daveho/HW_VGA/Episode04/Materials/theory-010.pdf

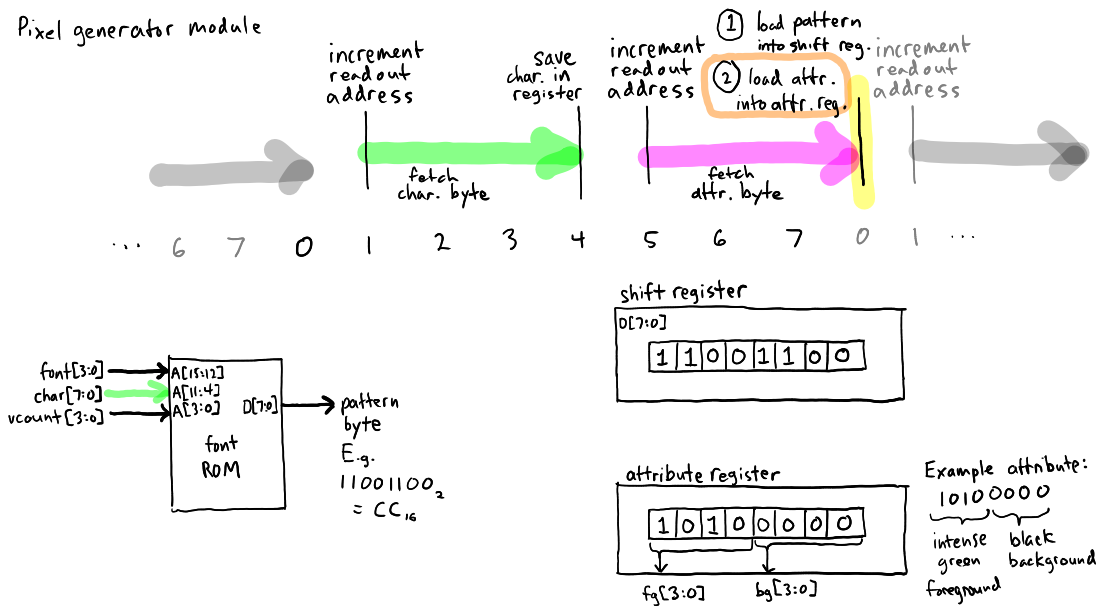
[picture p13: page 2]
