daveho/HW_VGA/Episode04/Materials/theory-011.pdf

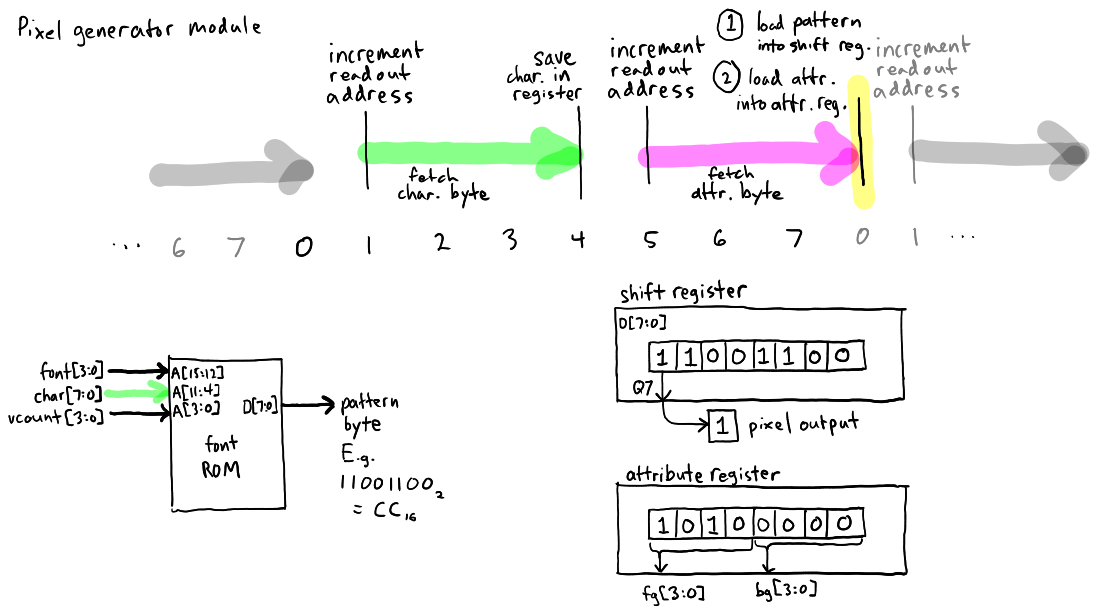
[picture p14: page 2]
