daveho/HW_VGA/Episode04/Materials/theory-012.pdf

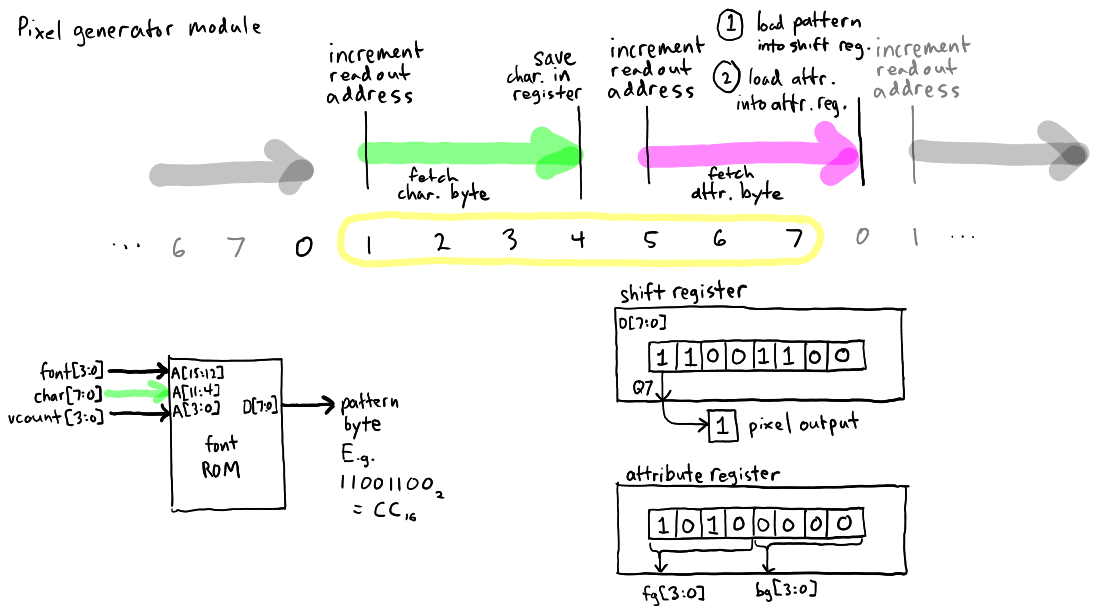
[picture p15: page 2]
