daveho/HW_VGA/Episode04/Materials/theory-013.pdf

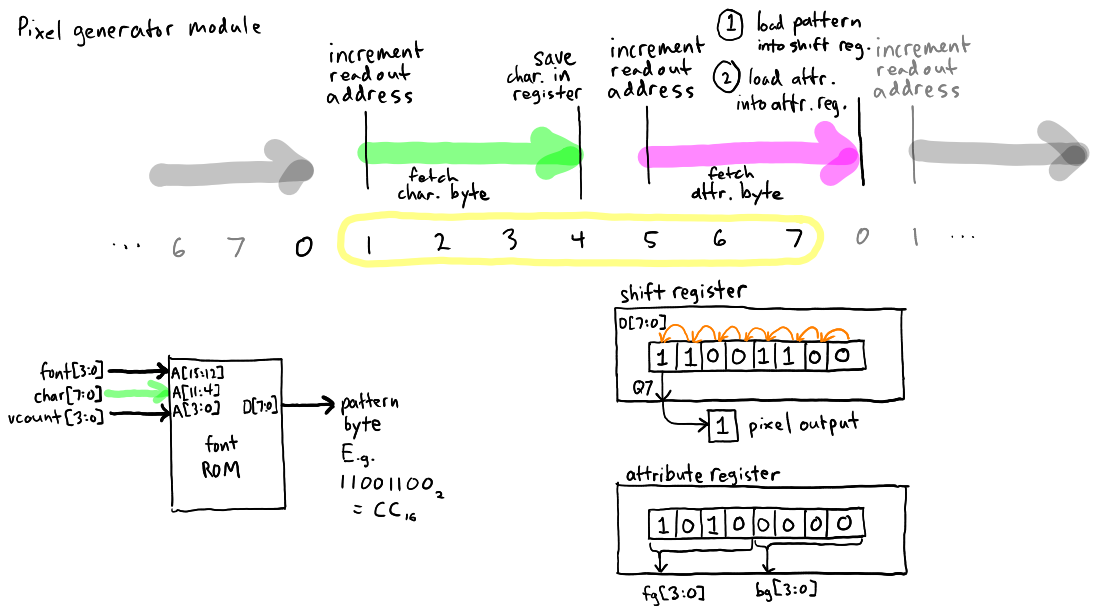
[picture p16: page 2]
