daveho/HW_VGA/Episode04/Materials/theory-014.pdf

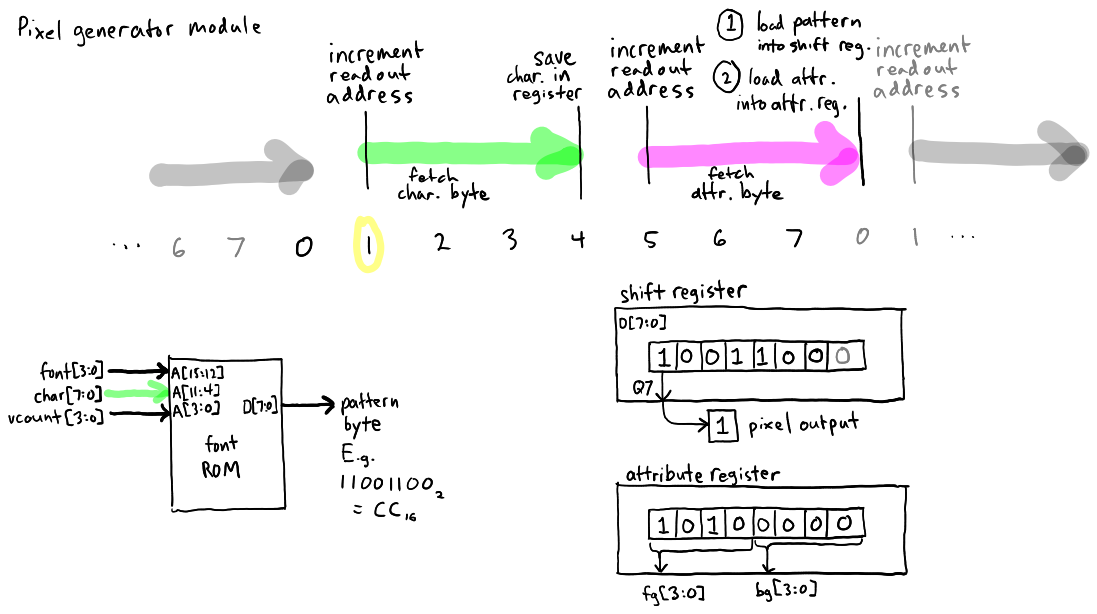
[picture p17: page 2]
