daveho/HW_VGA/Episode04/Materials/theory-015.pdf

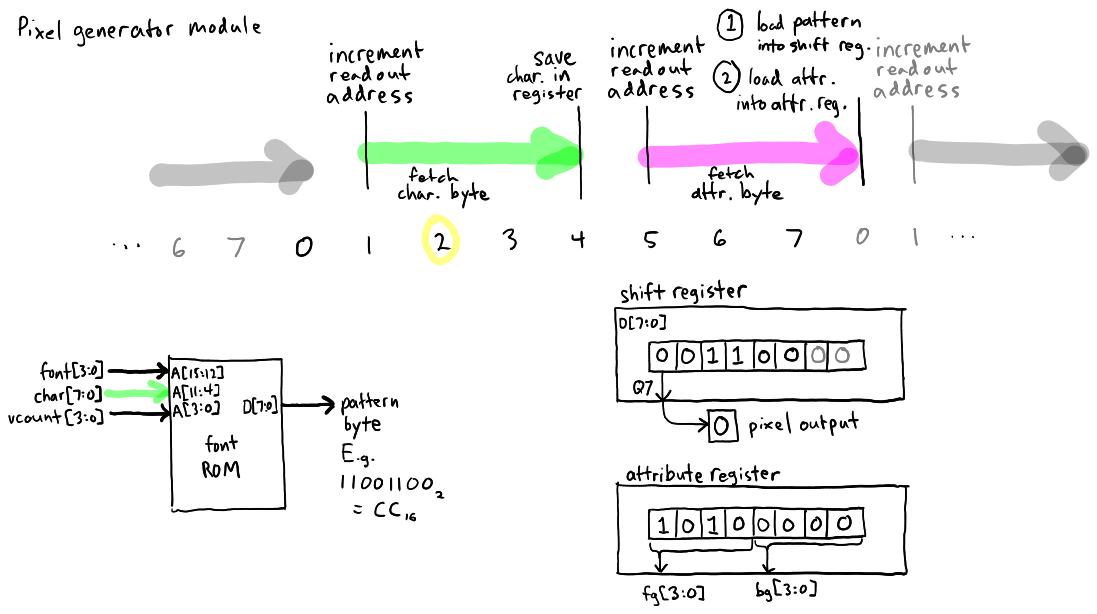
[picture p18: page 2]
