daveho/HW_VGA/Episode04/Materials/theory-016.pdf

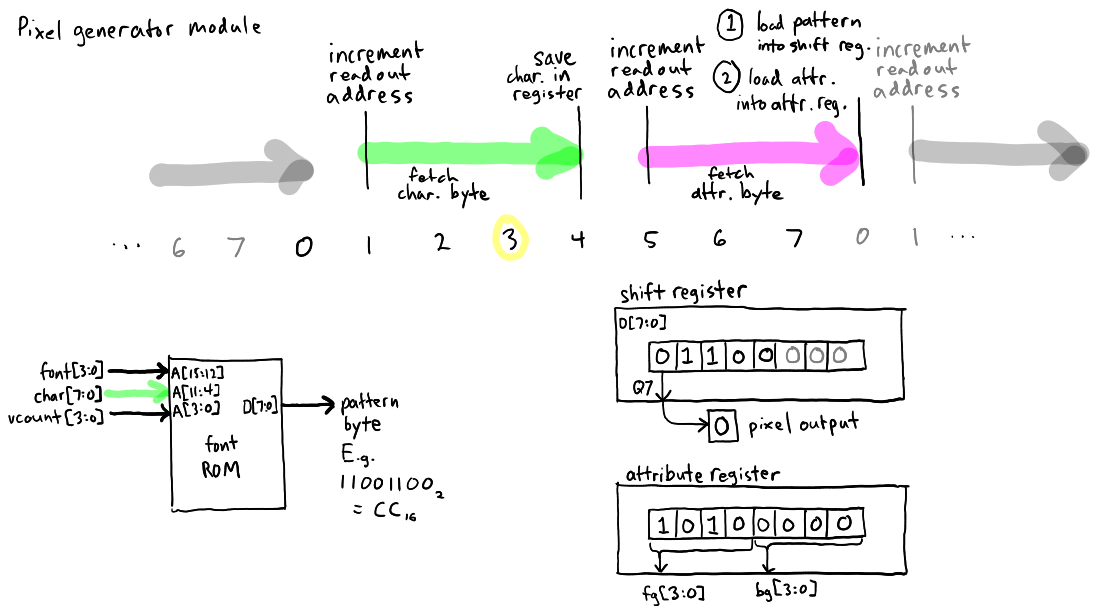
[picture p19: page 2]
