daveho/HW_VGA/Episode04/Materials/theory-017.pdf

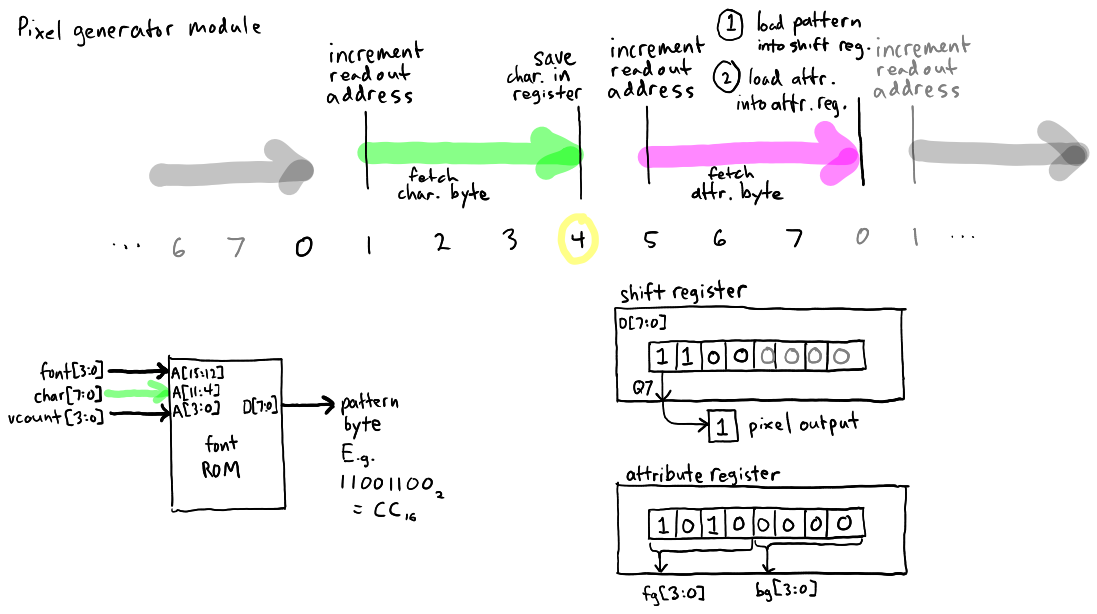
[picture p20: page 2]
