daveho/HW_VGA/Episode04/Materials/theory-018.pdf

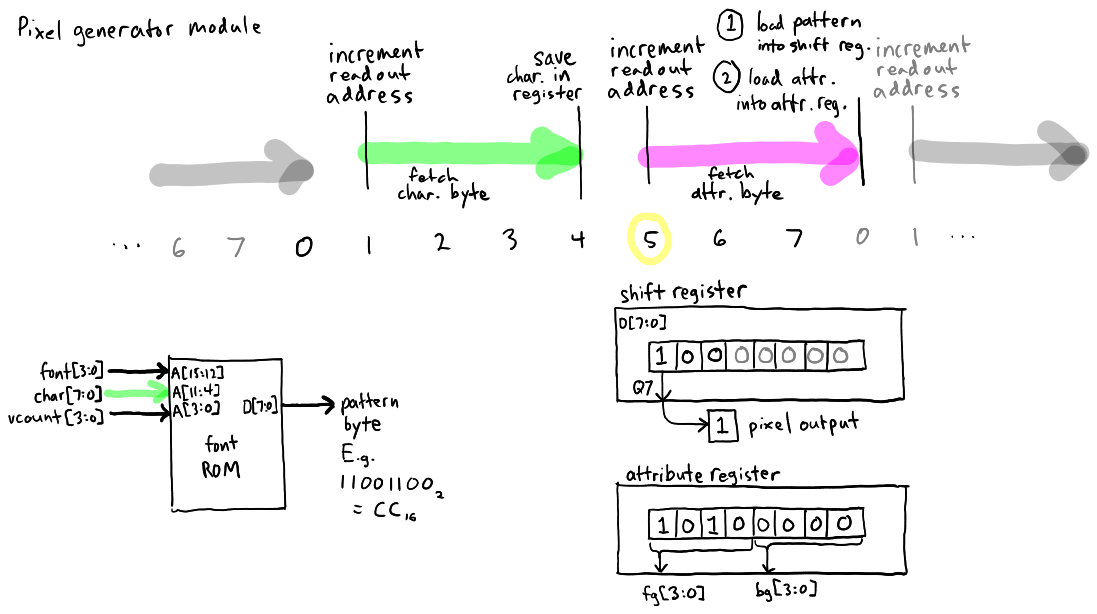
[picture p21: page 2]
