daveho/HW_VGA/Episode04/Materials/theory-019.pdf

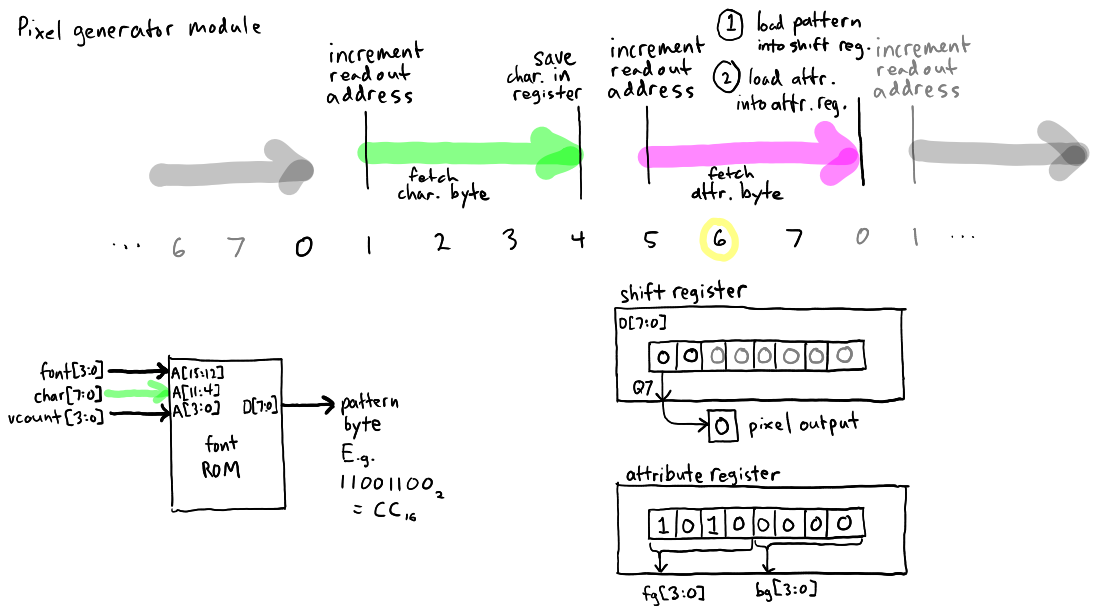
[picture p22: page 2]
