daveho/HW_VGA/Episode04/Materials/theory-020.pdf

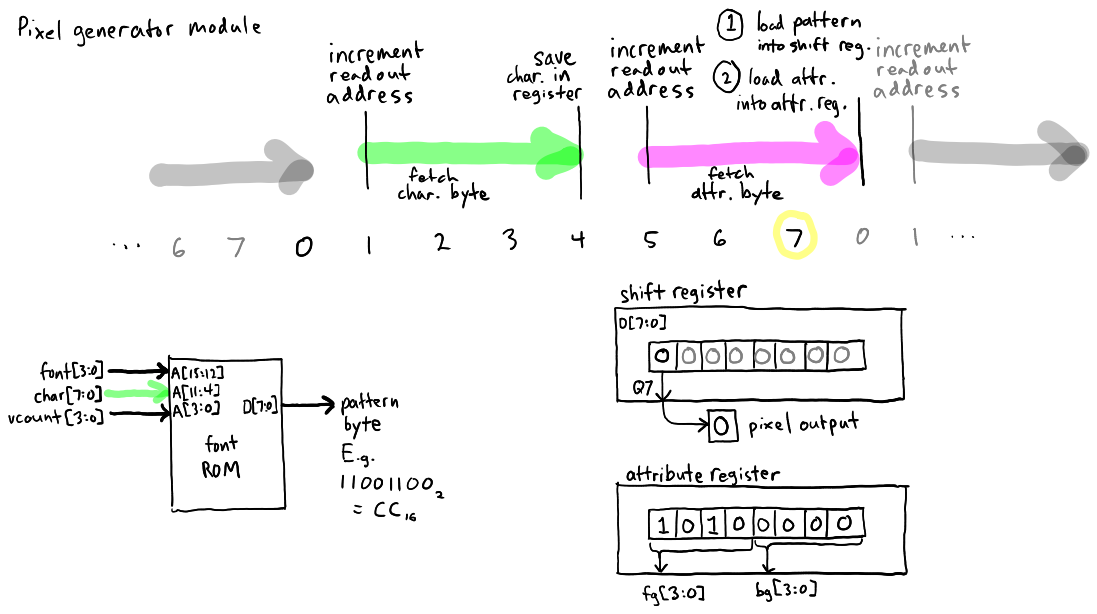
[picture p23: page 2]
