daveho/HW_VGA/Episode03/Materials/readout-overview-054.pdf

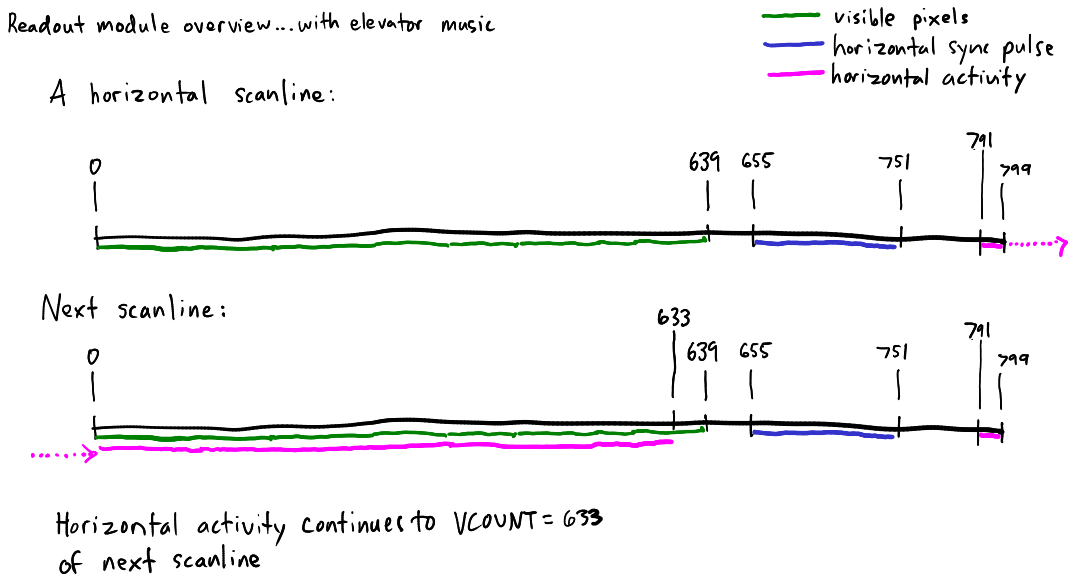
[picture p24: page 2]
