daveho/HW_VGA/Episode03/Materials/readout-overview-065.pdf

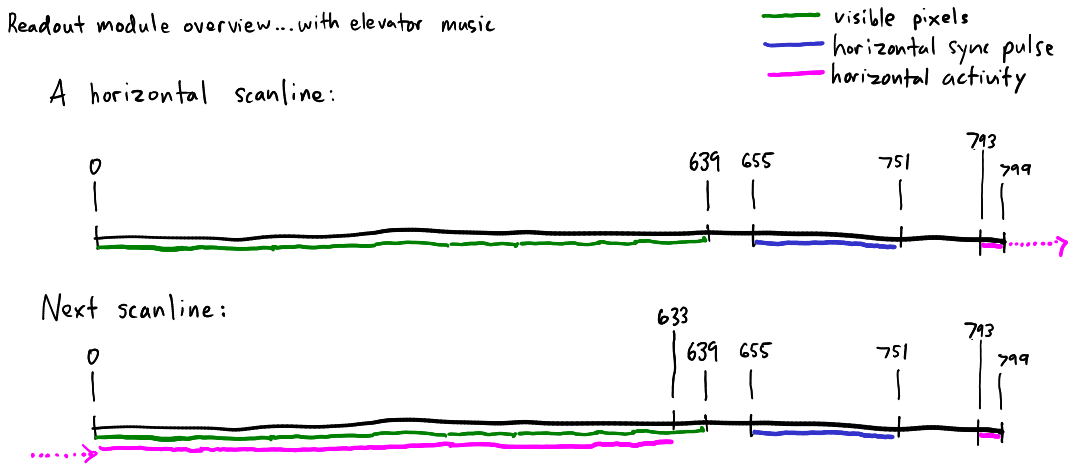
[picture p25: page 2]
