daveho/HW_VGA/Episode03/Materials/readout-overview-066.pdf

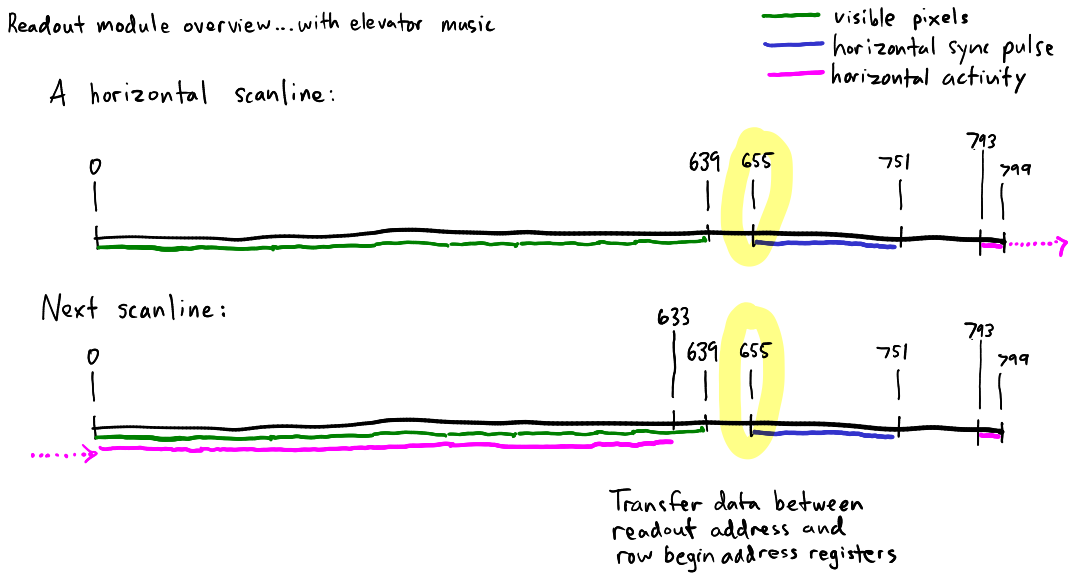
[picture p26: page 2]
