daveho/HW_VGA/Episode03/Materials/readout-overview-067.pdf

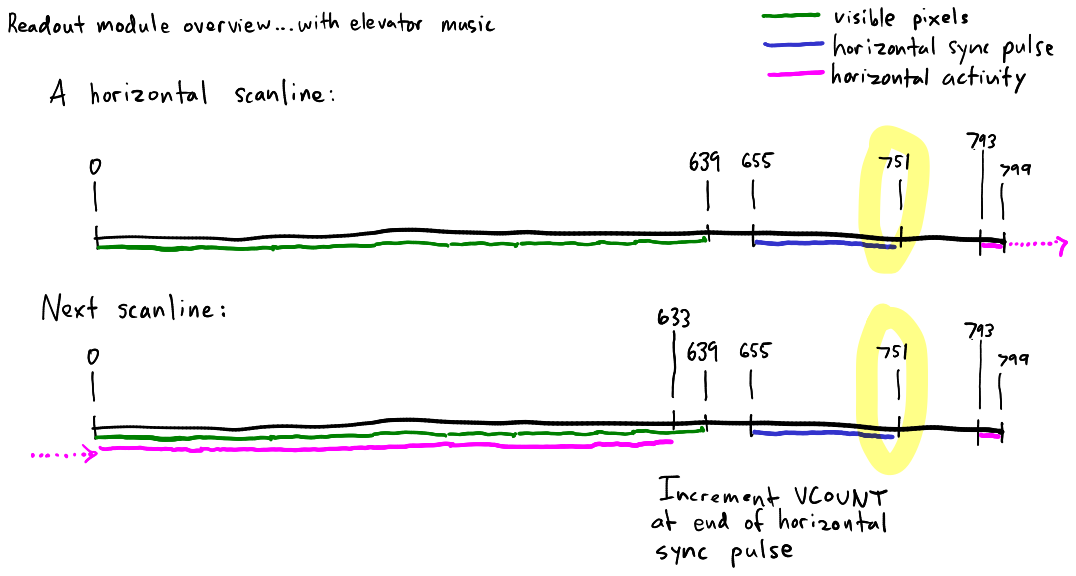
[picture p27: page 2]
