daveho/HW_VGA/Episode03/Materials/readout-overview-068.pdf

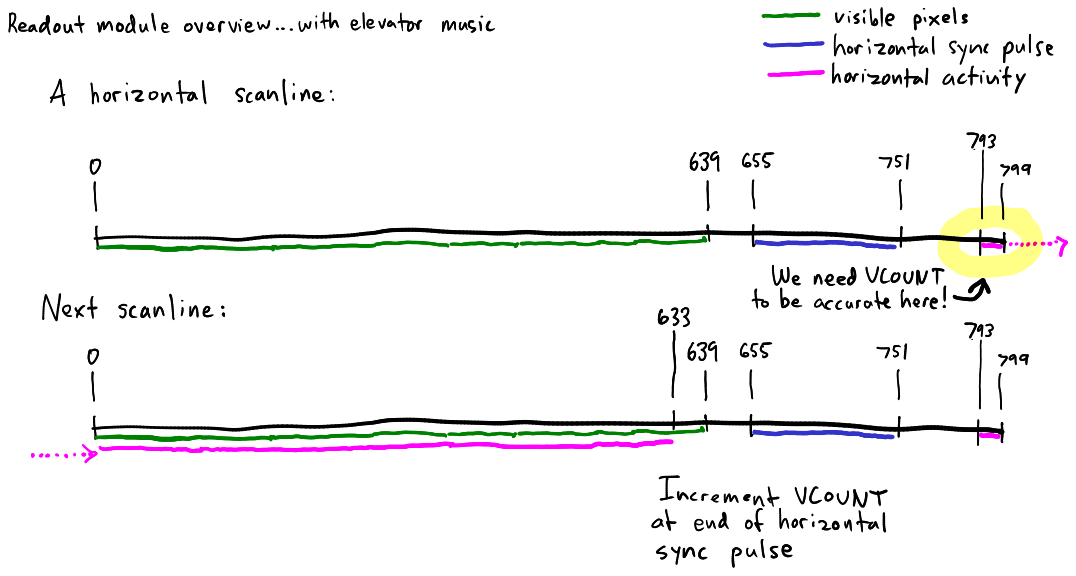
[picture p28: page 2]
