daveho/HW_VGA/Episode03/Materials/readout-overview-061.pdf

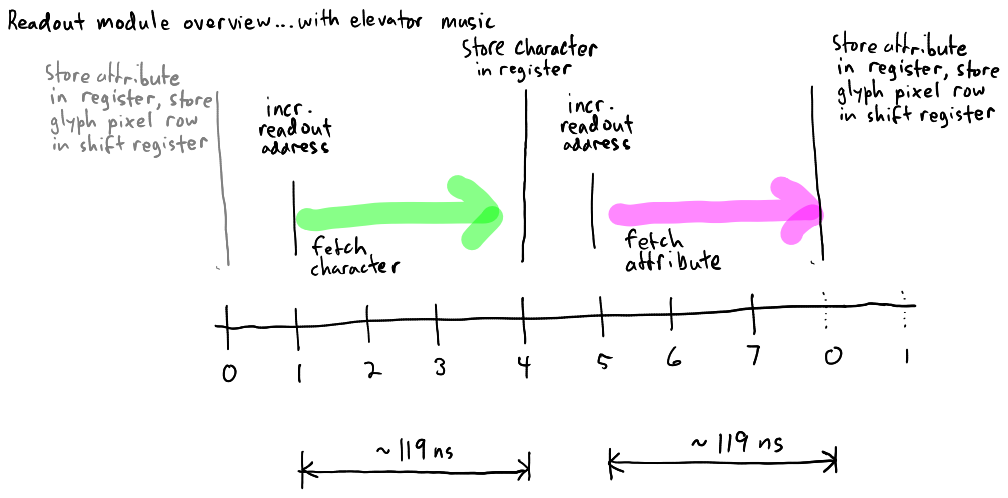
[picture p29: page 2]
