daveho/HW_VGA/Episode03/Materials/readout-overview-060a.pdf

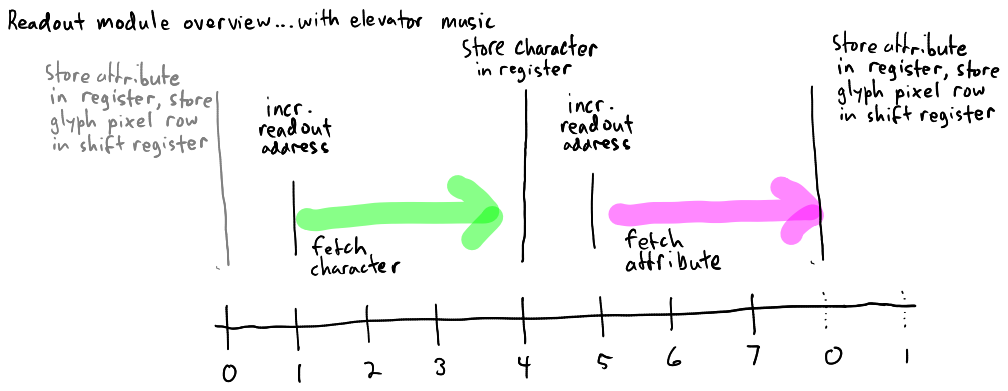
[picture p30: page 2]
