daveho/HW_VGA/Episode03/Materials/readout-overview-055.pdf

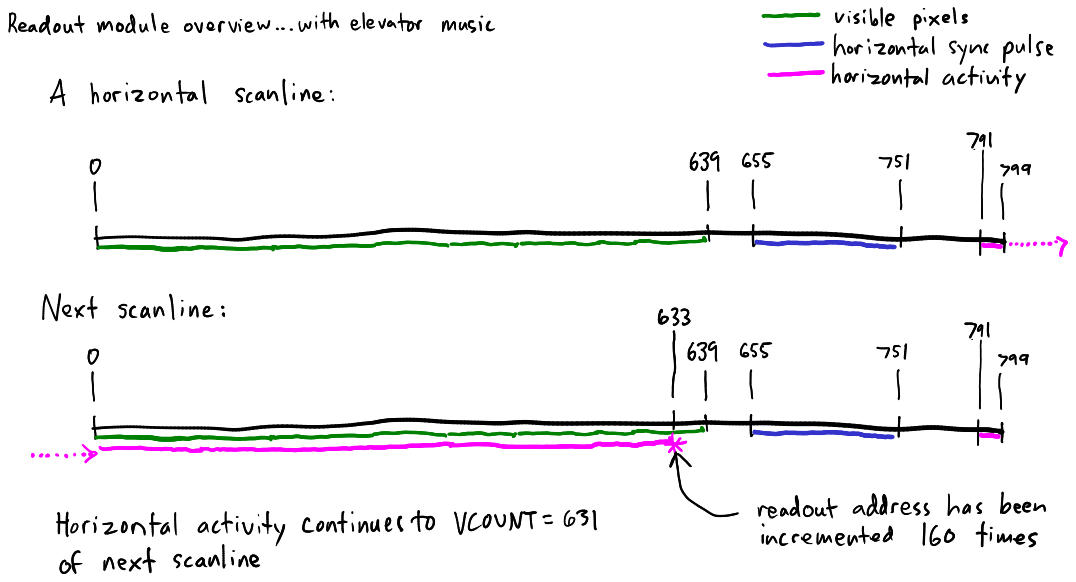
[picture p31: page 2]
