daveho/HW_VGA/Episode03/Materials/readout-overview-053a.pdf

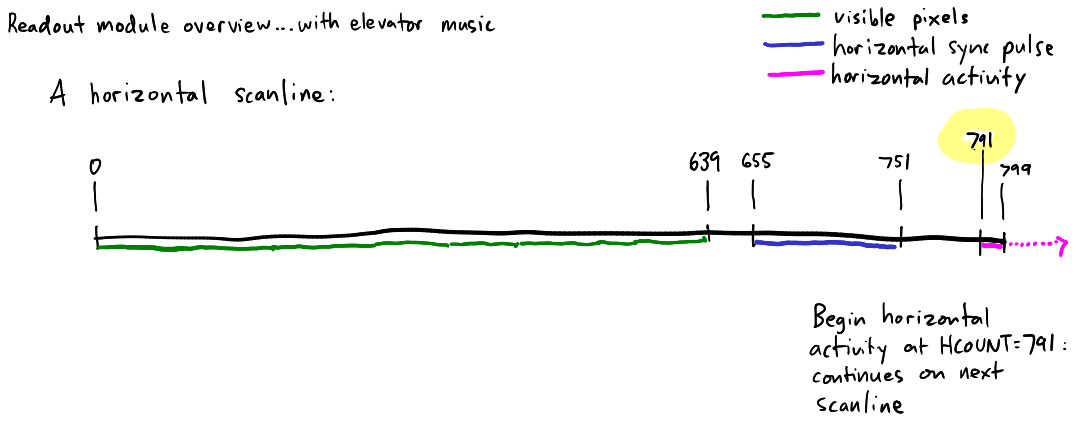
[picture p32: page 2]
