daveho/HW_VGA/Episode03/Materials/readout-overview-037b.pdf

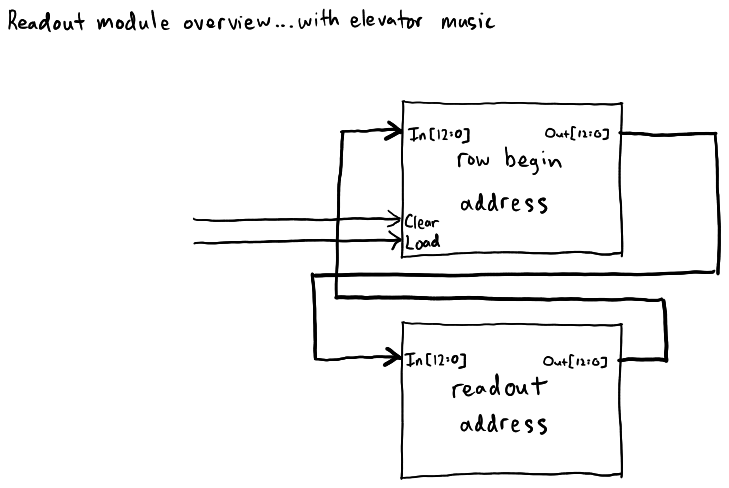
[picture p33: page 2]
