daveho/HW_VGA/Episode03/Materials/readout-overview-002.pdf

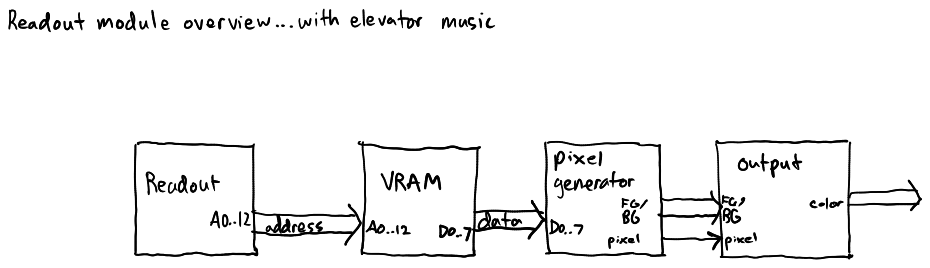
[picture p34: page 2]
