daveho/HW_VGA/Episode03/Materials/readout-overview-003.pdf

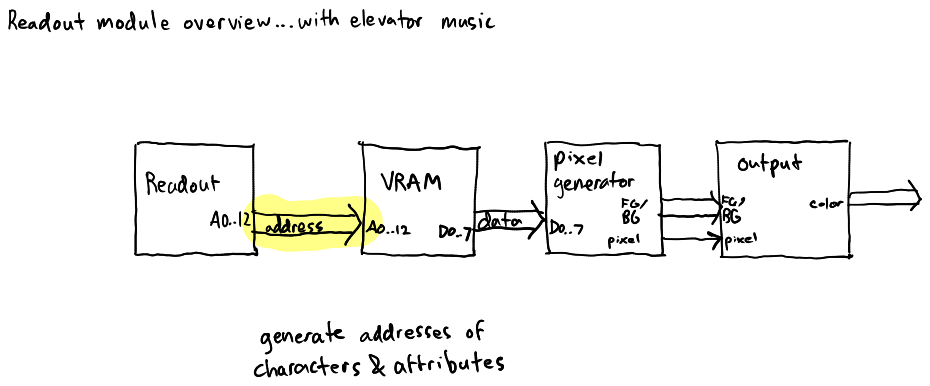
[picture p35: page 2]
