daveho/HW_VGA/Episode03/Materials/readout-overview-004.pdf

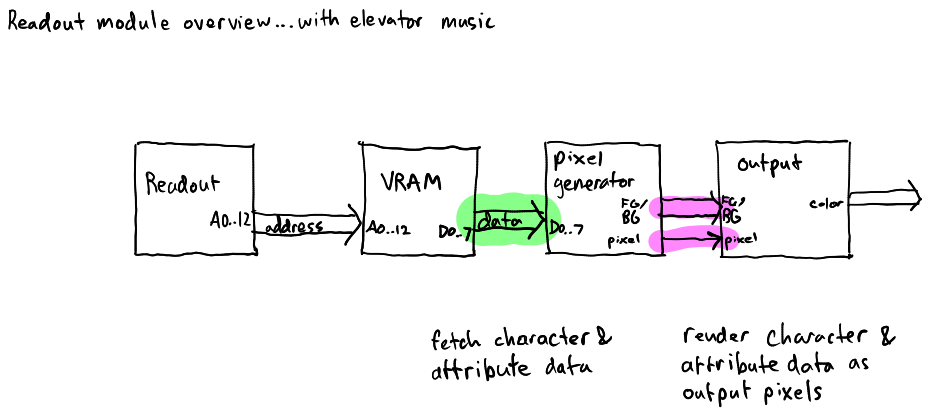
[picture p36: page 2]
