daveho/HW_VGA/Episode03/Materials/readout-overview-005.pdf

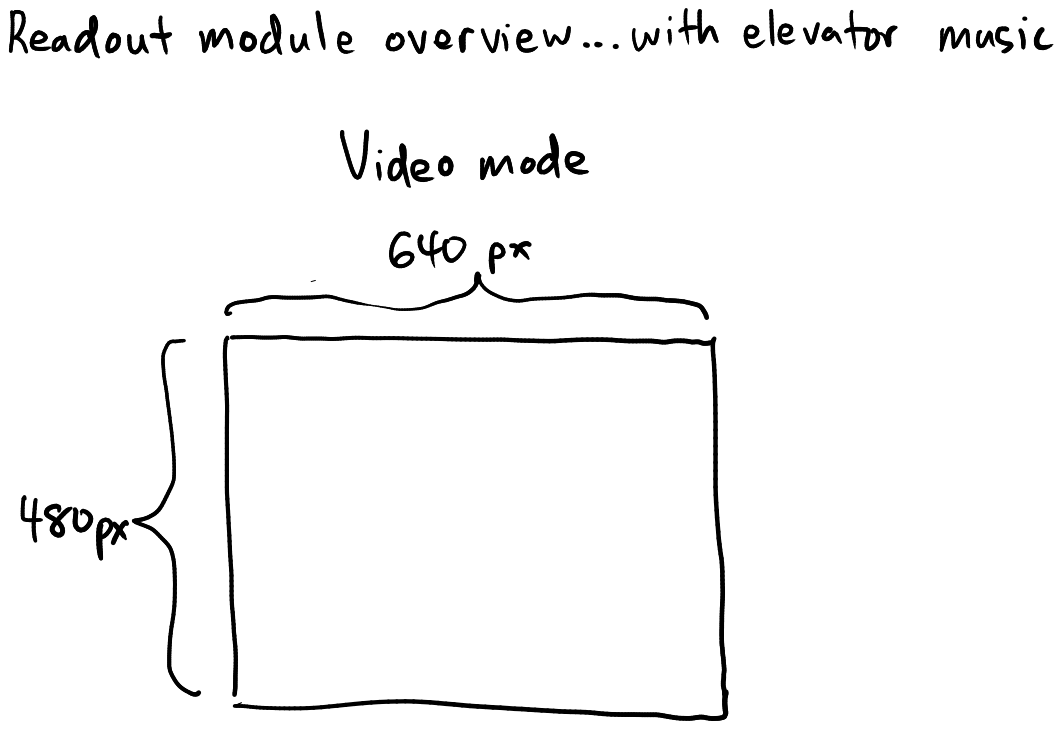
[picture p37: page 2]
