daveho/HW_VGA/Episode03/Materials/readout-overview-006.pdf

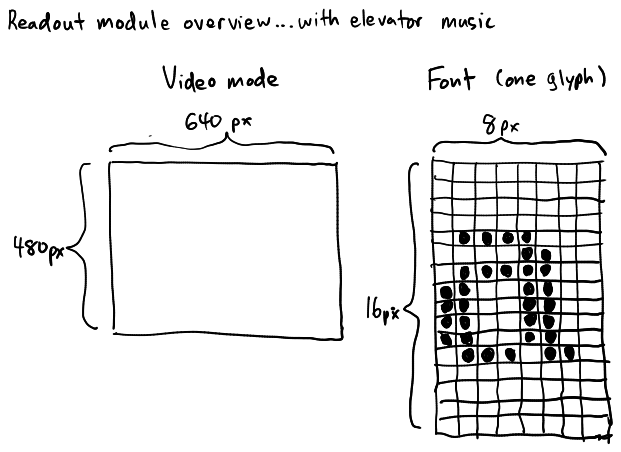
[picture p38: page 2]
