daveho/HW_VGA/Episode03/Materials/readout-overview-007.pdf

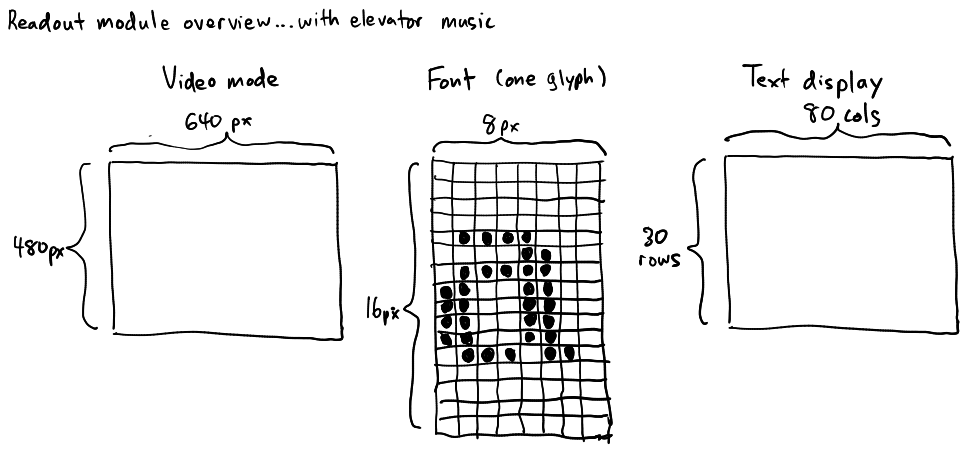
[picture p39: page 2]
