daveho/HW_VGA/Episode03/Materials/readout-overview-008.pdf

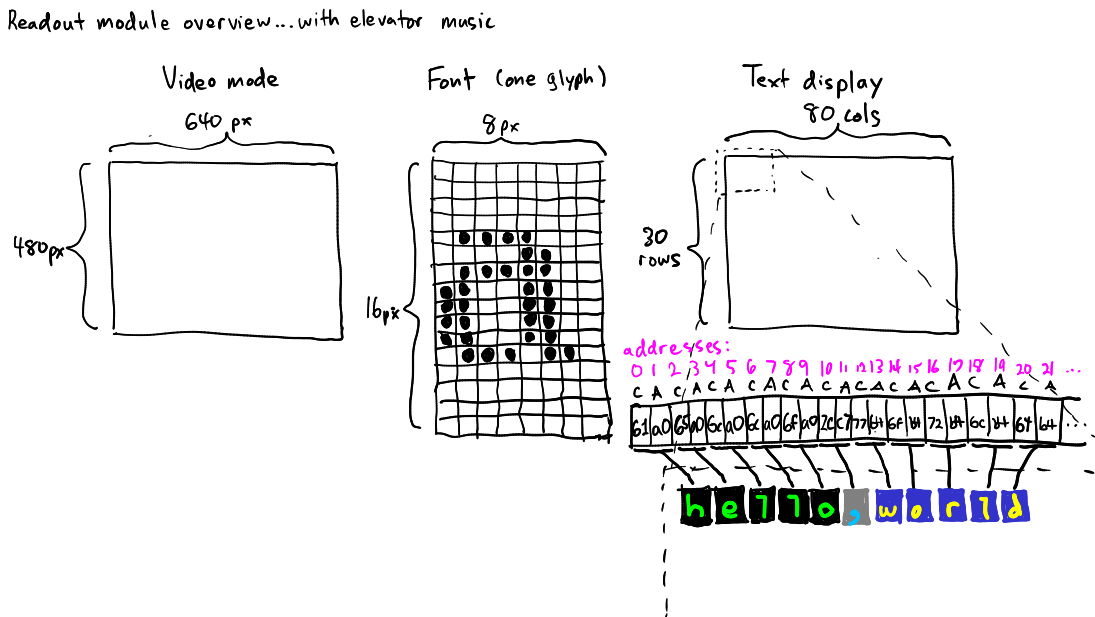
[picture p40: page 2]
