daveho/HW_VGA/Episode03/Materials/readout-overview-009.pdf

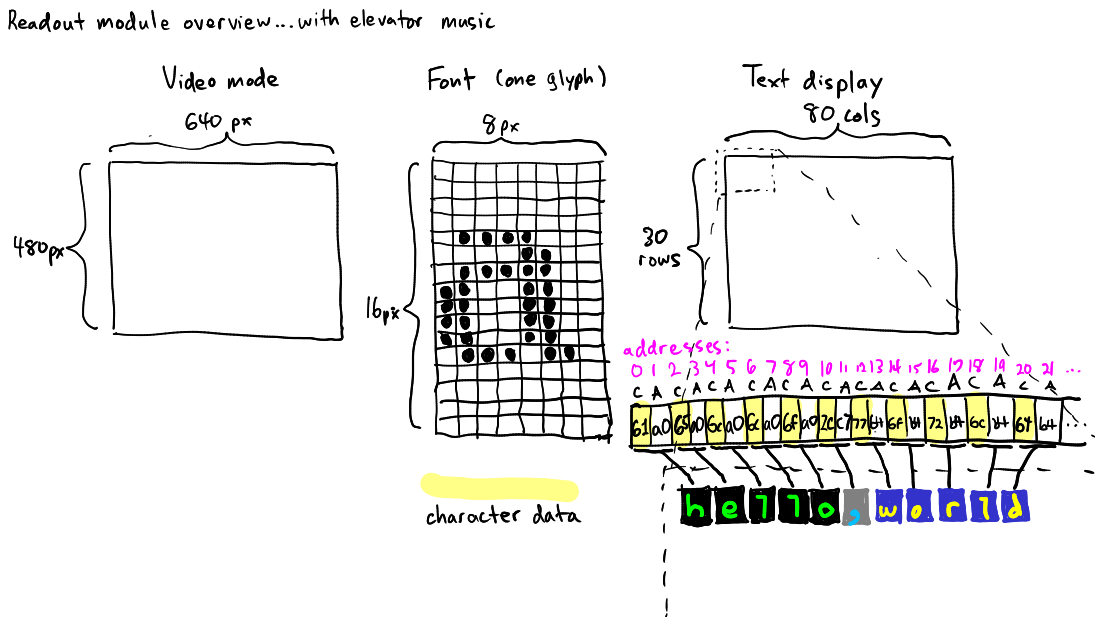
[picture p41: page 2]
