daveho/HW_VGA/Episode03/Materials/readout-overview-010.pdf

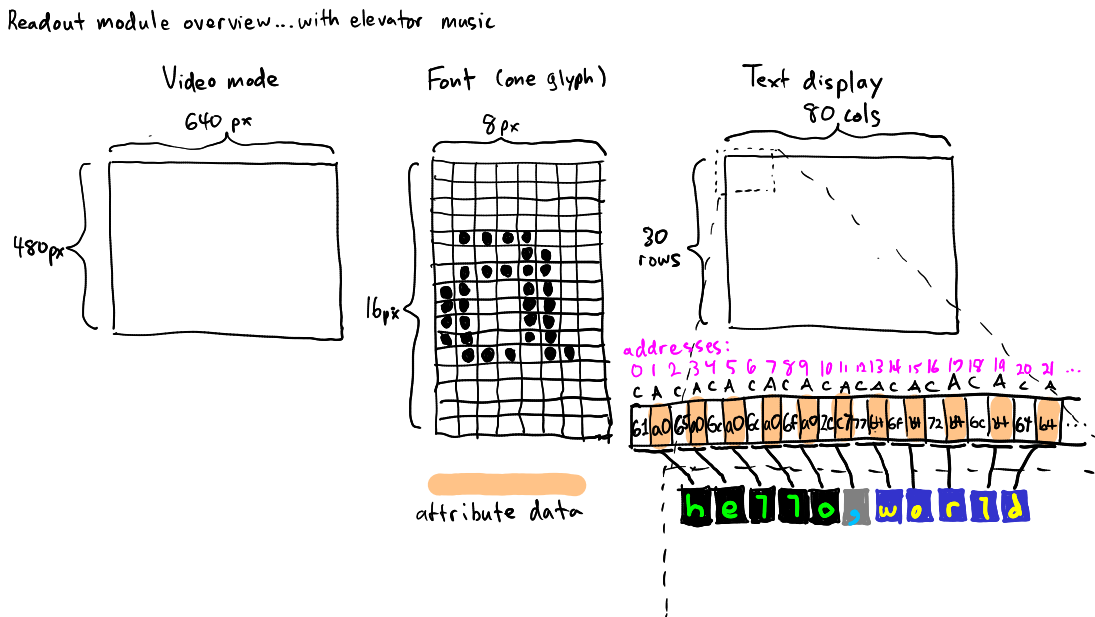
[picture p42: page 2]
