daveho/HW_VGA/Episode03/Materials/readout-overview-011.pdf

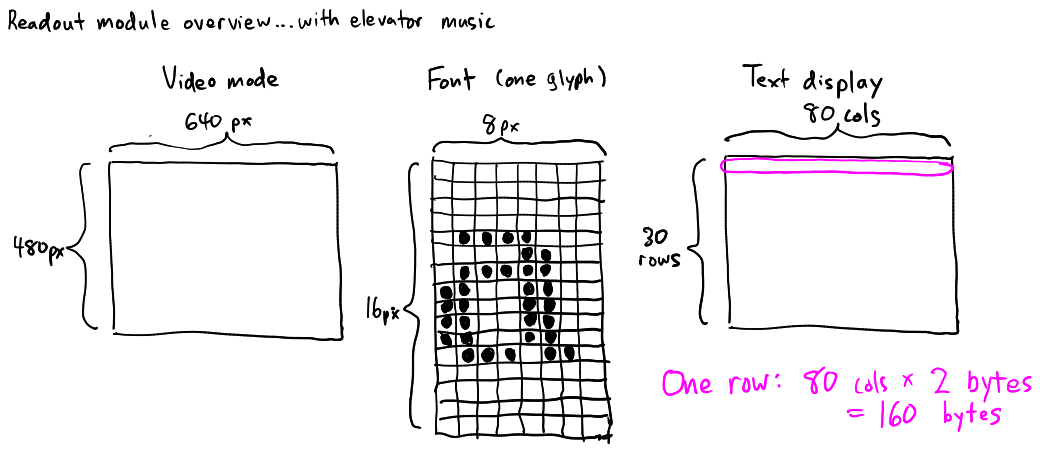
[picture p43: page 2]
