daveho/HW_VGA/Episode03/Materials/readout-overview-012.pdf

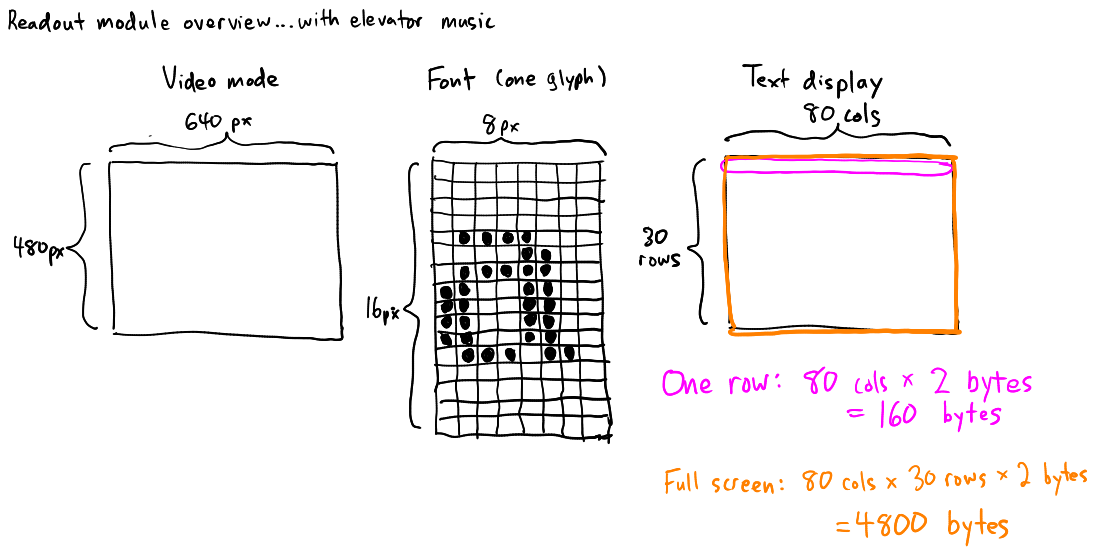
[picture p44: page 2]
