daveho/HW_VGA/Episode03/Materials/readout-overview-013.pdf

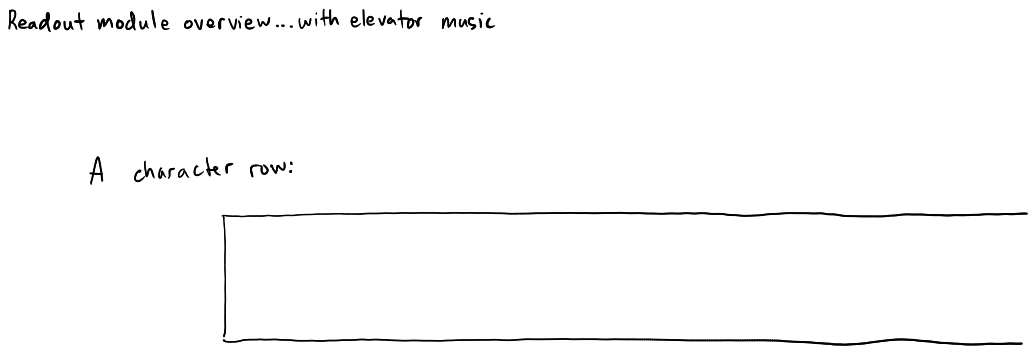
[picture p45: page 2]
