daveho/HW_VGA/Episode03/Materials/readout-overview-014.pdf

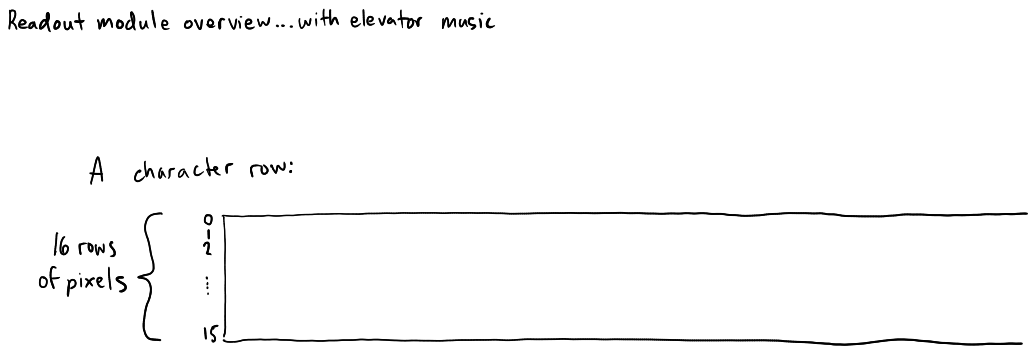
[picture p46: page 2]
