daveho/HW_VGA/Episode03/Materials/readout-overview-015.pdf

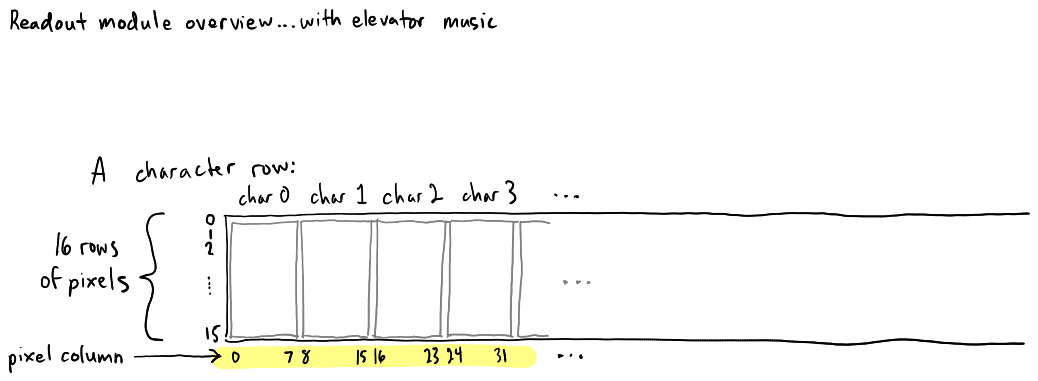
[picture p47: page 2]
