daveho/HW_VGA/Episode03/Materials/readout-overview-016.pdf

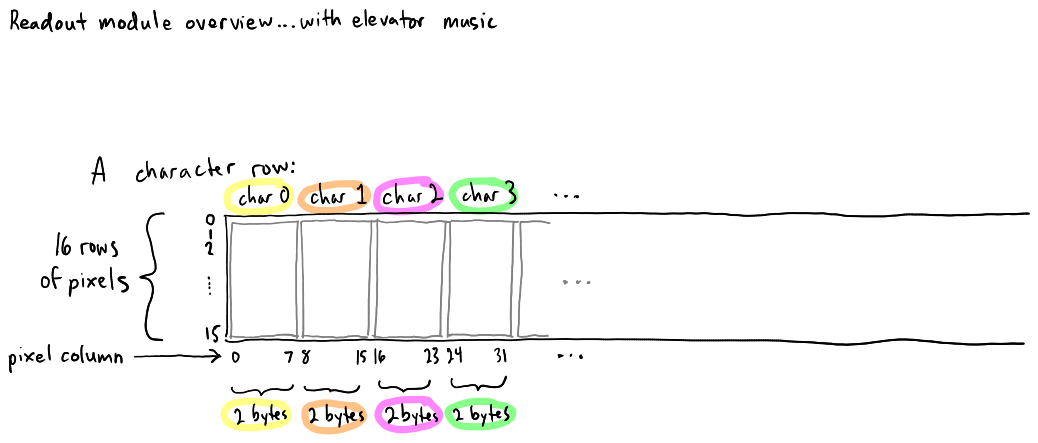
[picture p48: page 2]
