daveho/HW_VGA/Episode03/Materials/readout-overview-017.pdf

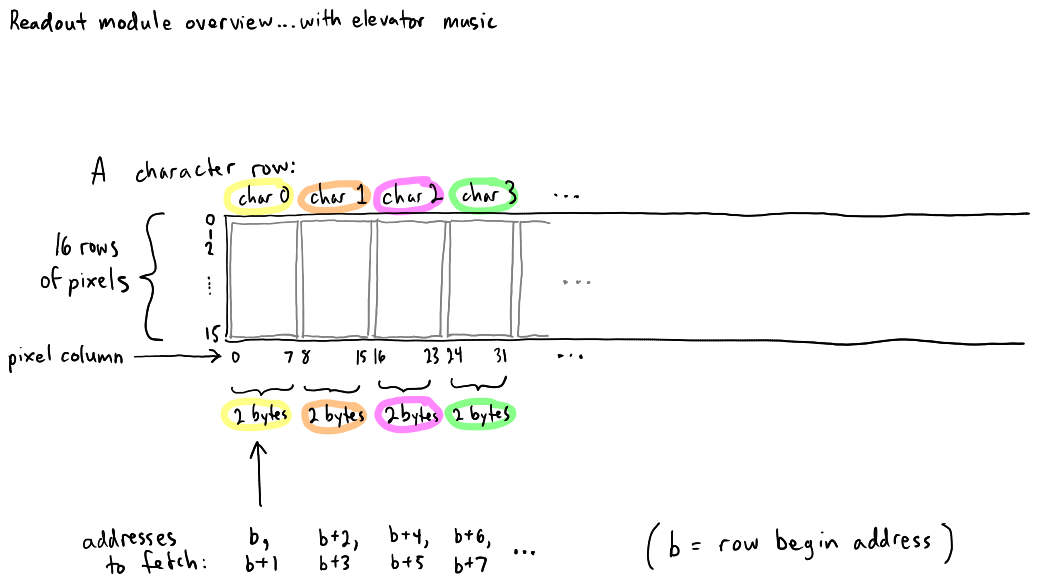
[picture p49: page 2]
