daveho/HW_VGA/Episode03/Materials/readout-overview-019.pdf

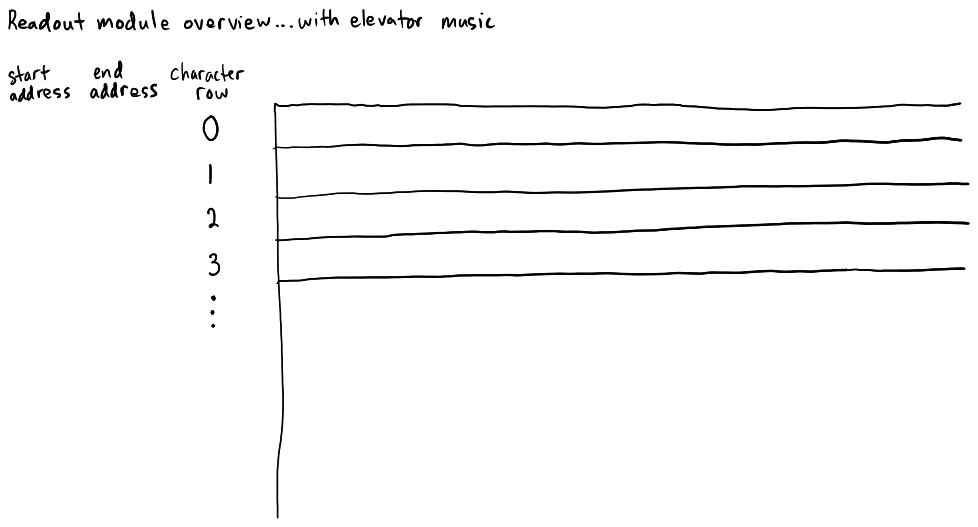
[picture p50: page 2]
