daveho/HW_VGA/Episode03/Materials/readout-overview-020.pdf

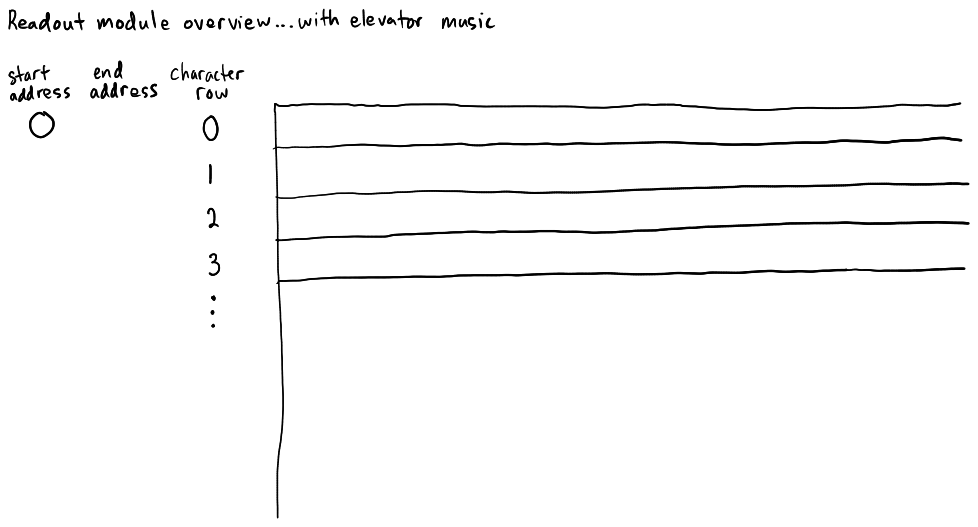
[picture p51: page 2]
