daveho/HW_VGA/Episode03/Materials/readout-overview-021.pdf

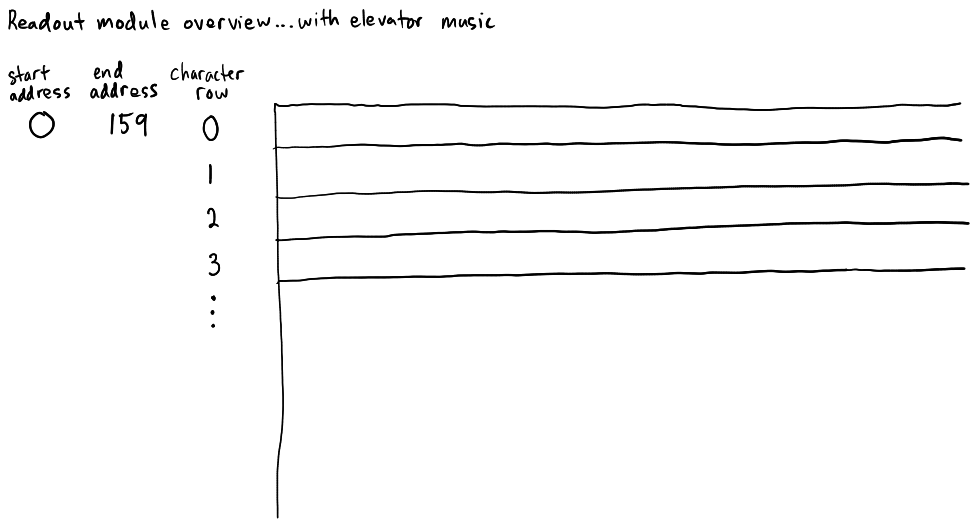
[picture p52: page 2]
