daveho/HW_VGA/Episode03/Materials/readout-overview-022.pdf

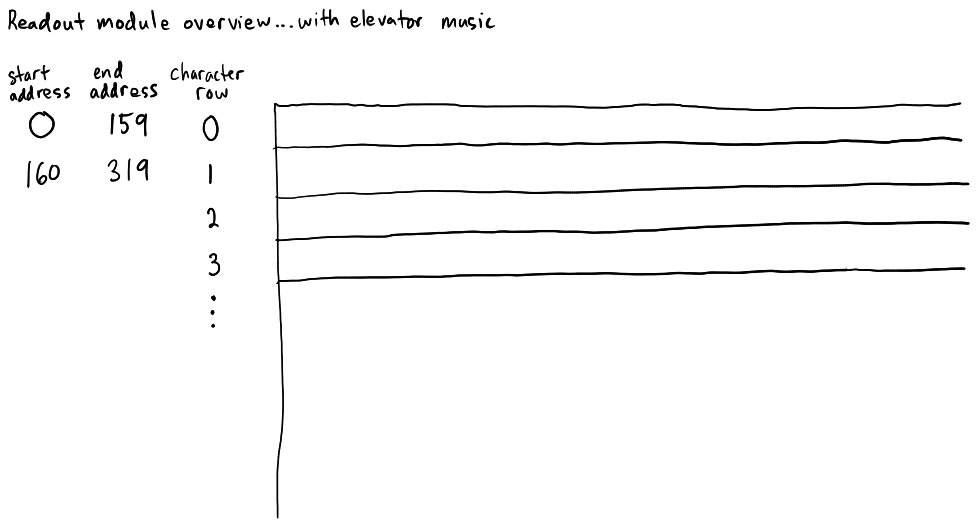
[picture p53: page 2]
