daveho/HW_VGA/Episode03/Materials/readout-overview-023.pdf

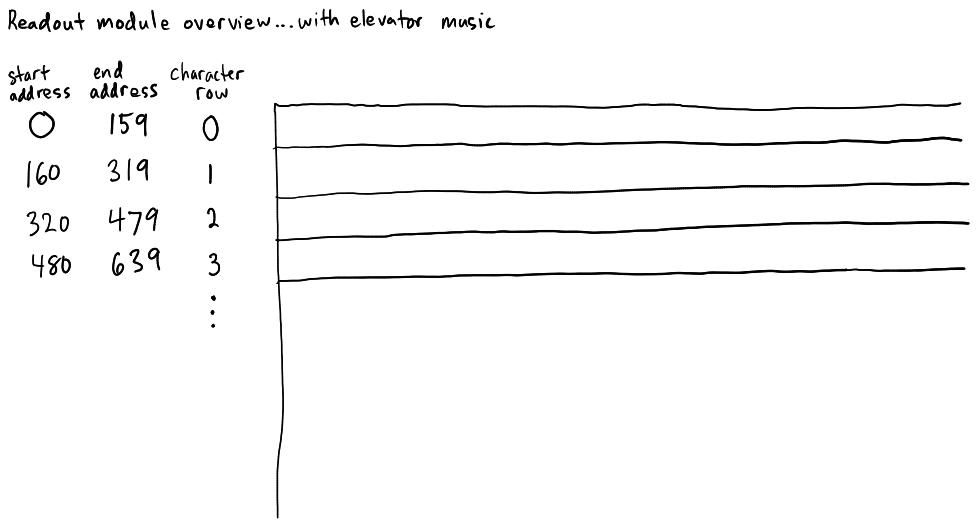
[picture p54: page 2]
