daveho/HW_VGA/Episode03/Materials/readout-overview-024.pdf

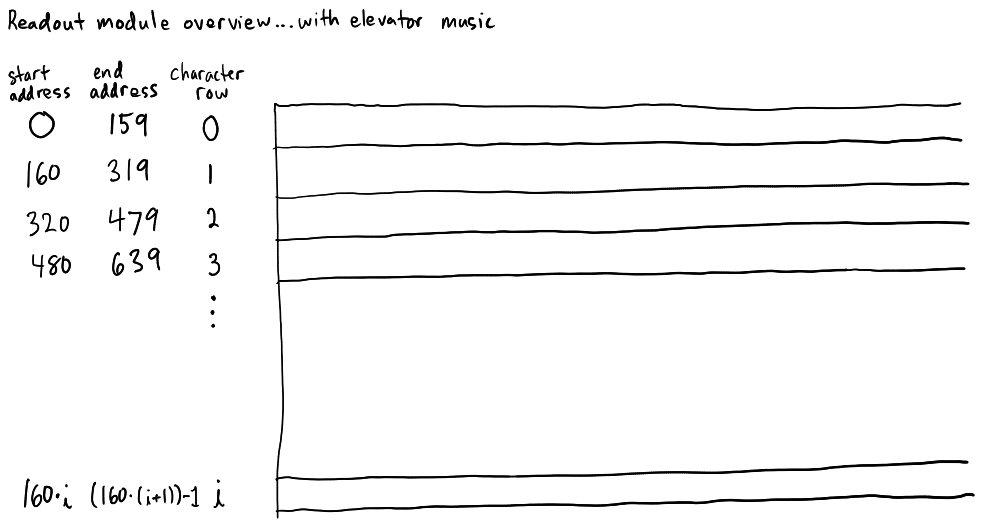
[picture p55: page 2]
