daveho/HW_VGA/Episode03/Materials/readout-overview-025.pdf

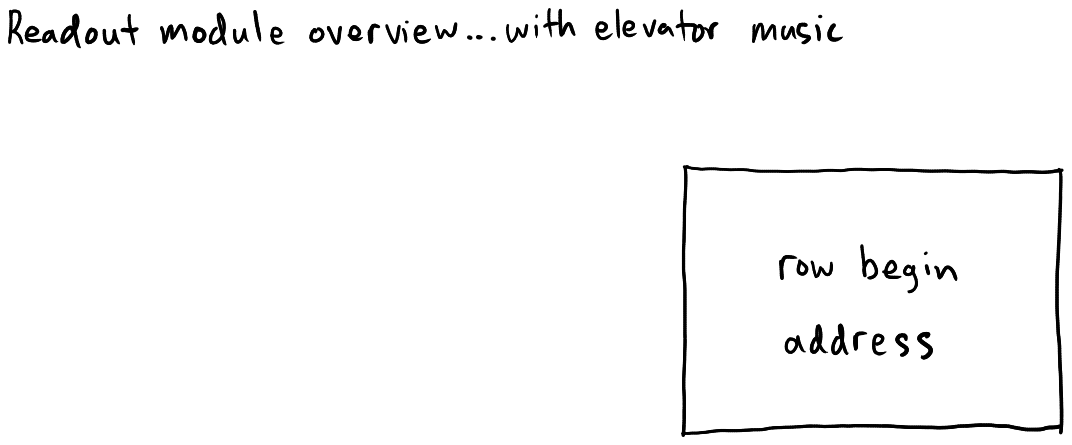
[picture p56: page 2]
