daveho/HW_VGA/Episode03/Materials/readout-overview-026.pdf

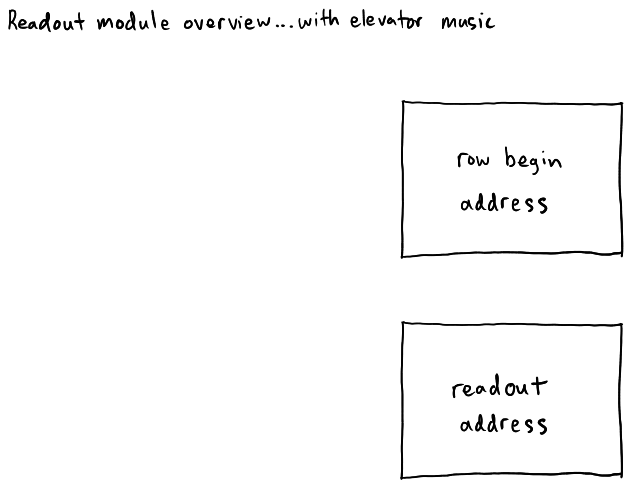
[picture p57: page 2]
