daveho/HW_VGA/Episode03/Materials/readout-overview-027.pdf

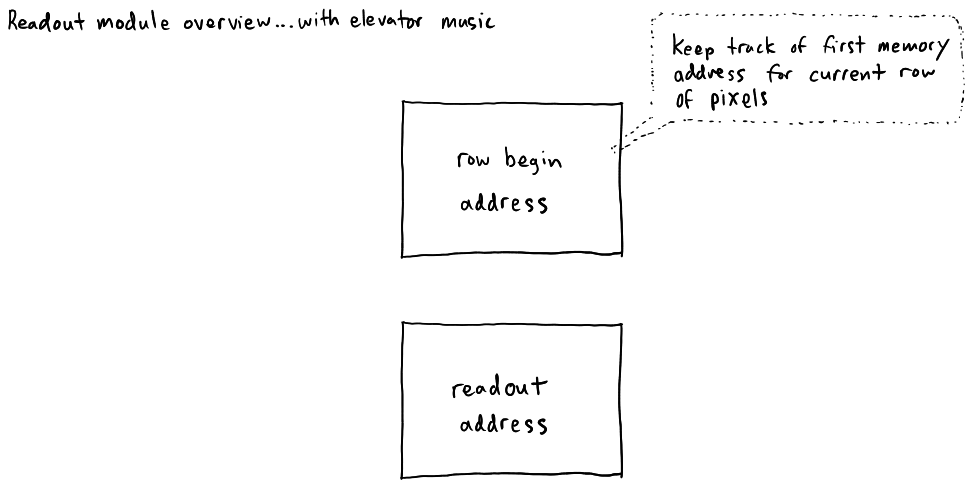
[picture p58: page 2]
