daveho/HW_VGA/Episode03/Materials/readout-overview-028.pdf

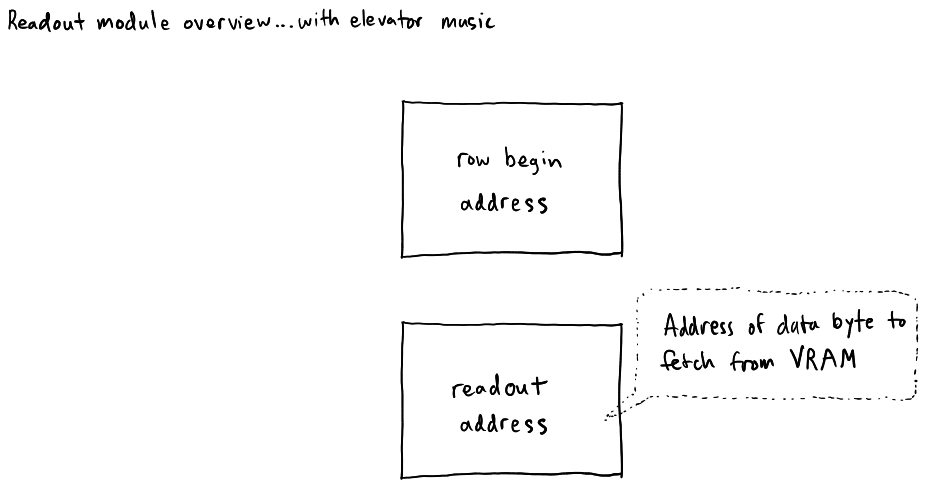
[picture p59: page 2]
