daveho/HW_VGA/Episode03/Materials/readout-overview-029.pdf

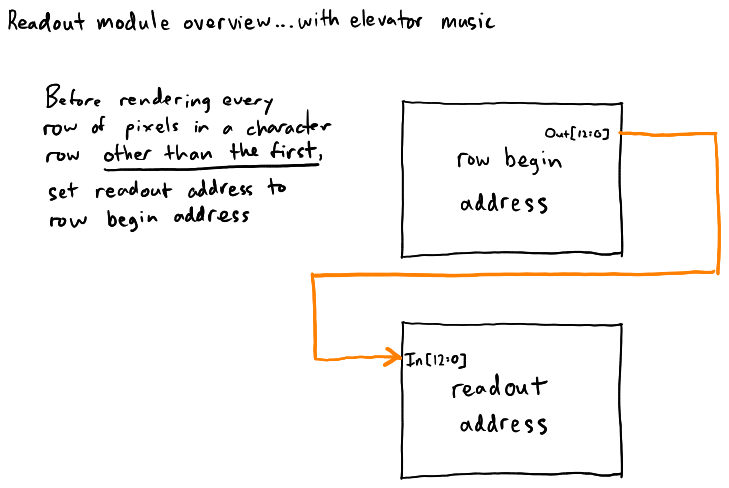
[picture p60: page 2]
