daveho/HW_VGA/Episode03/Materials/readout-overview-030.pdf

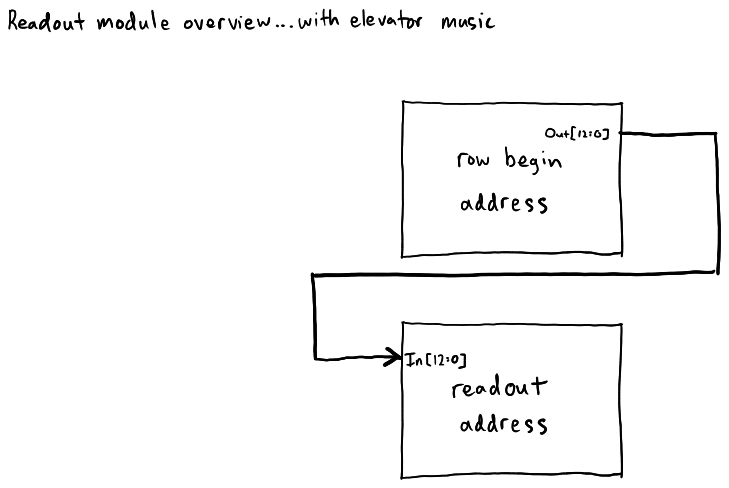
[picture p61: page 2]
