daveho/HW_VGA/Episode03/Materials/readout-overview-031.pdf

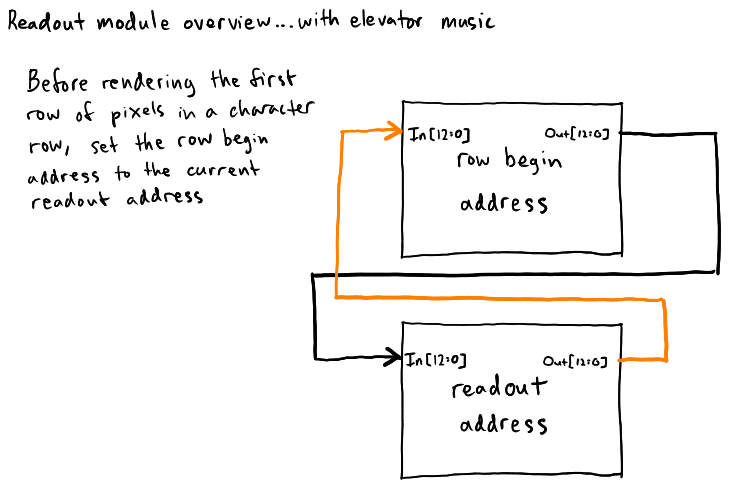
[picture p62: page 2]
