daveho/HW_VGA/Episode03/Materials/readout-overview-032.pdf

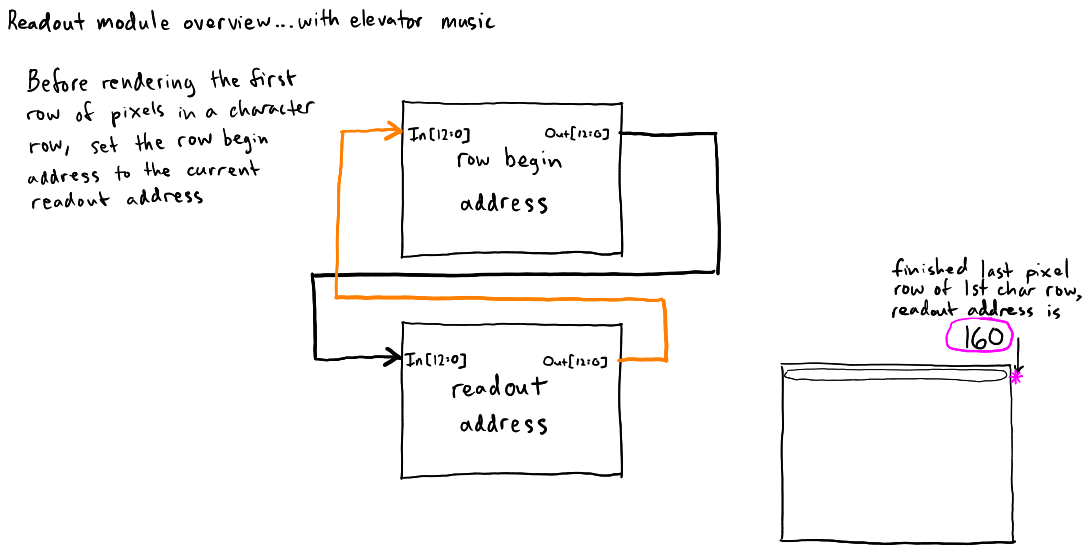
[picture p63: page 2]
