daveho/HW_VGA/Episode03/Materials/readout-overview-033.pdf

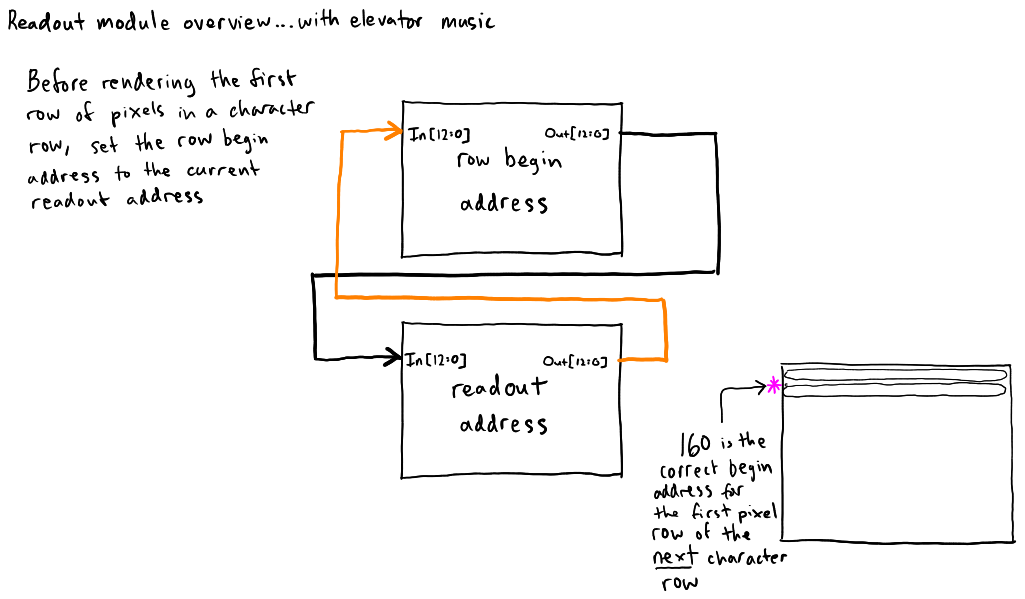
[picture p64: page 2]
