daveho/HW_VGA/Episode03/Materials/readout-overview-001.png

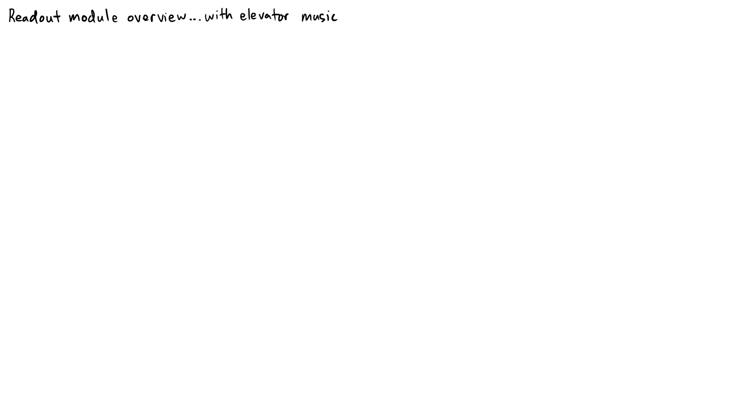
Episode03/Materials/readout-overview-001.png
