daveho/HW_VGA/Episode03/Materials/readout-overview-002.png

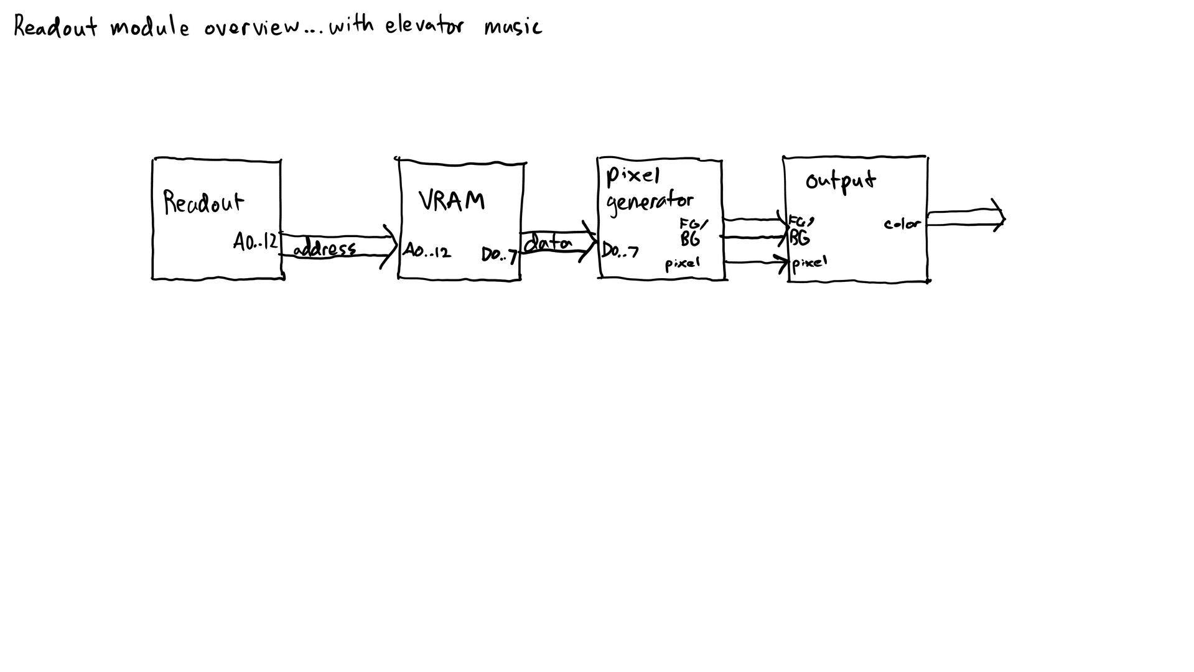
Episode03/Materials/readout-overview-002.png
