daveho/HW_VGA/Episode03/Materials/readout-overview-004.png

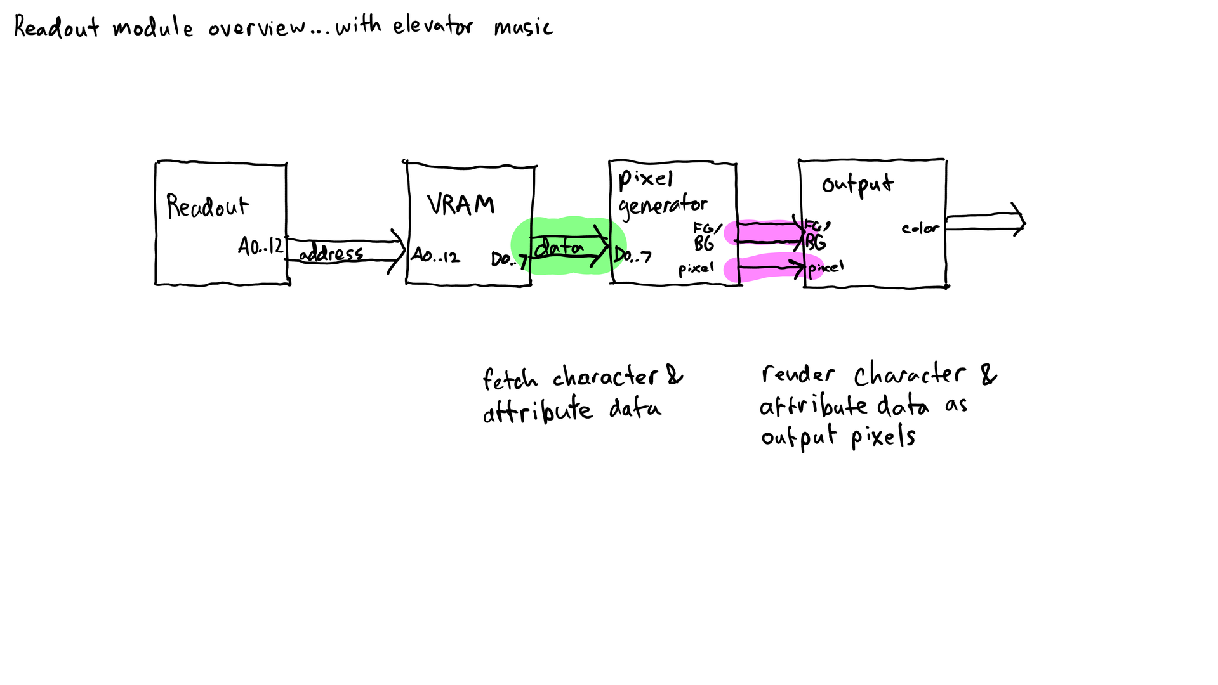
Episode03/Materials/readout-overview-004.png
