daveho/HW_VGA/Episode03/Materials/readout-overview-005.png

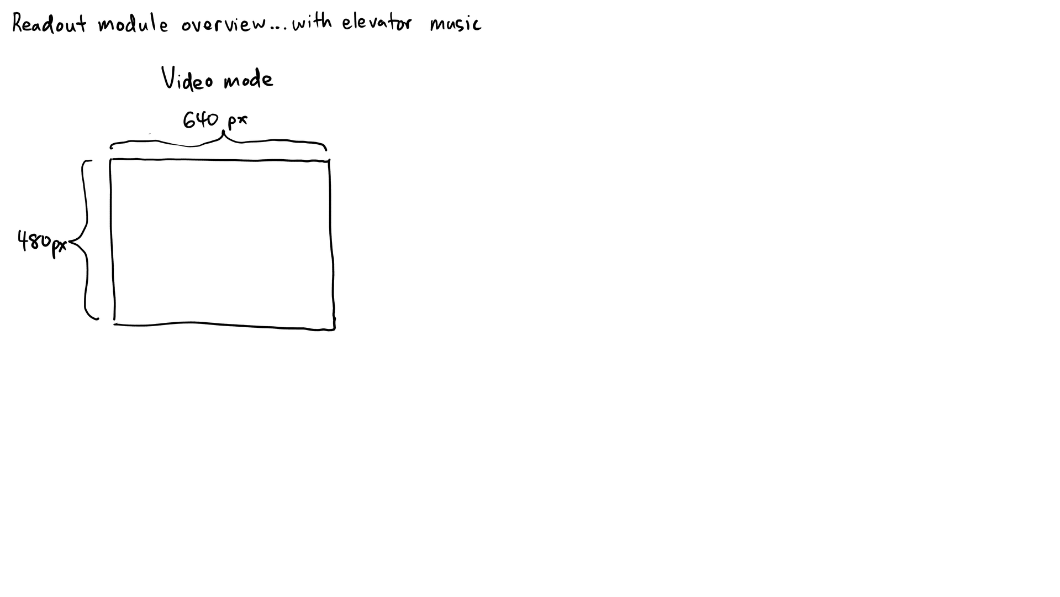
Episode03/Materials/readout-overview-005.png
