daveho/HW_VGA/Episode03/Materials/readout-overview-006.png

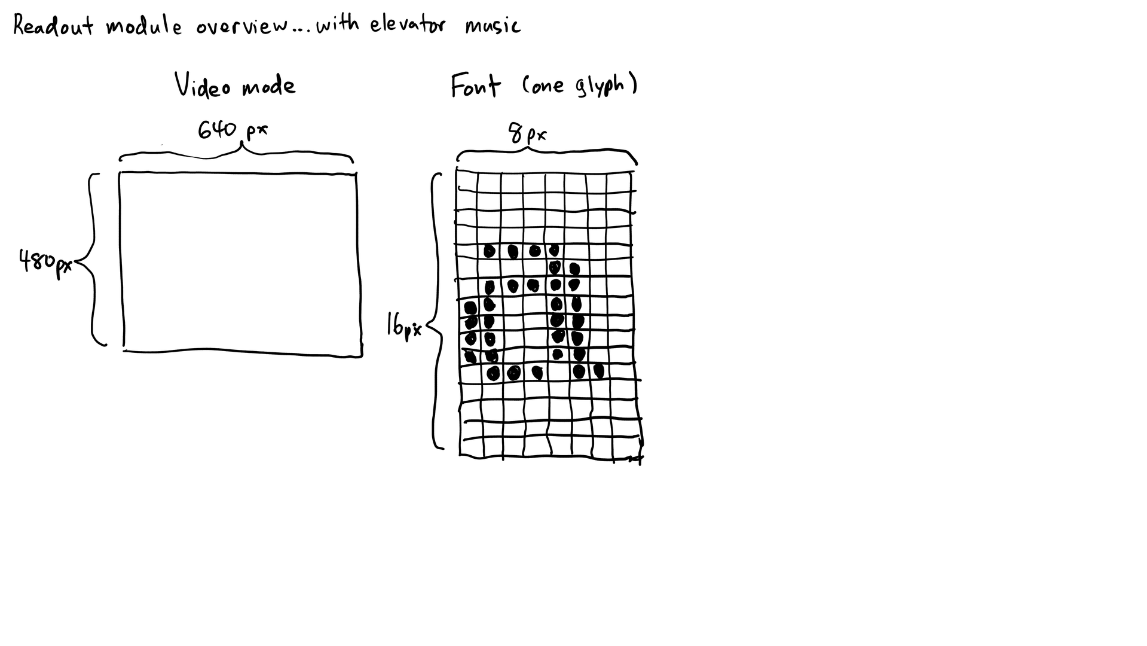
Episode03/Materials/readout-overview-006.png
