daveho/HW_VGA/Episode03/Materials/readout-overview-007.png

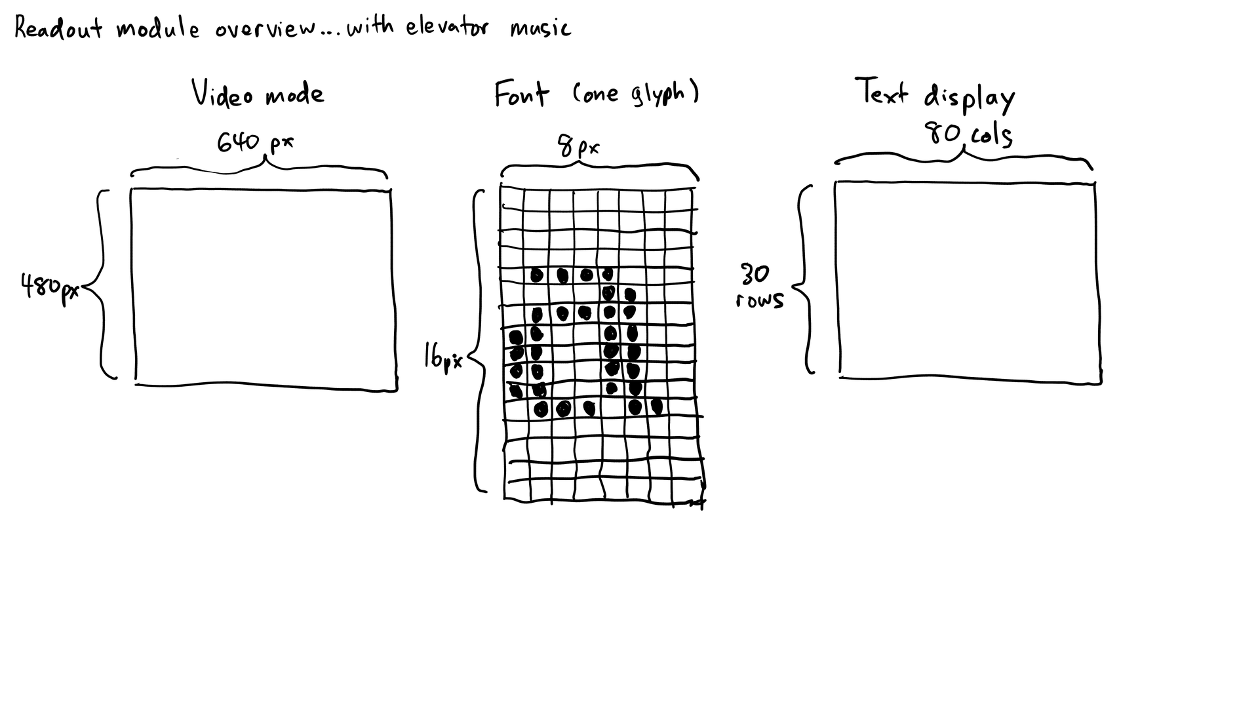
Episode03/Materials/readout-overview-007.png
