daveho/HW_VGA/Episode03/Materials/readout-overview-012.png

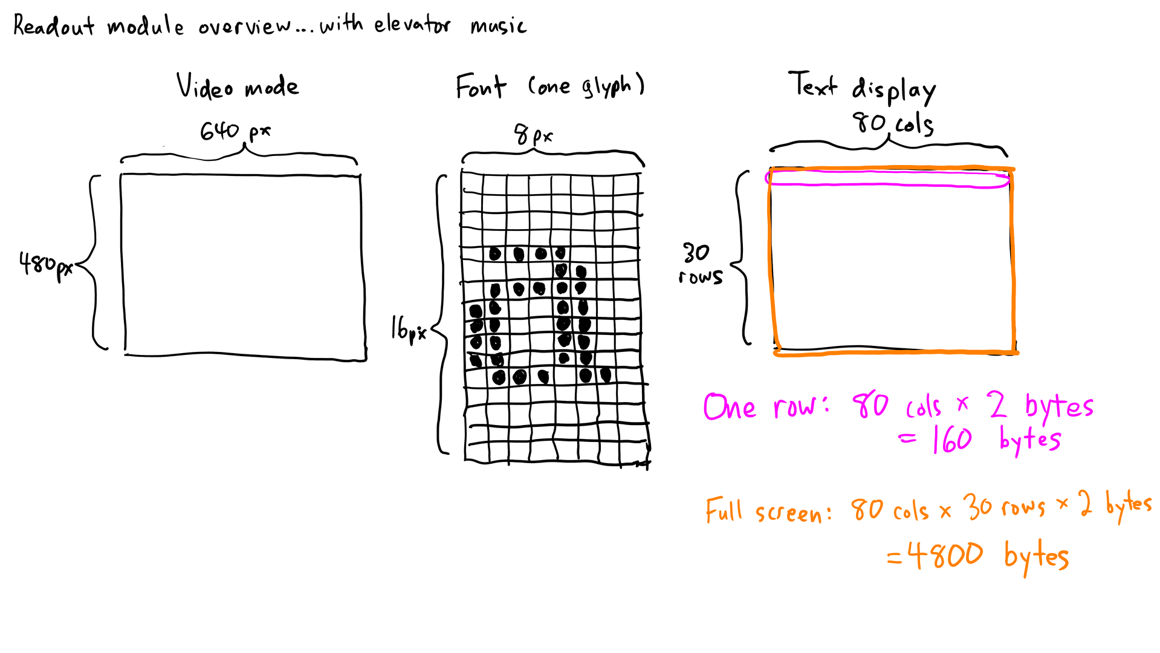
Episode03/Materials/readout-overview-012.png
