daveho/HW_VGA/Episode03/Materials/readout-overview-013.png

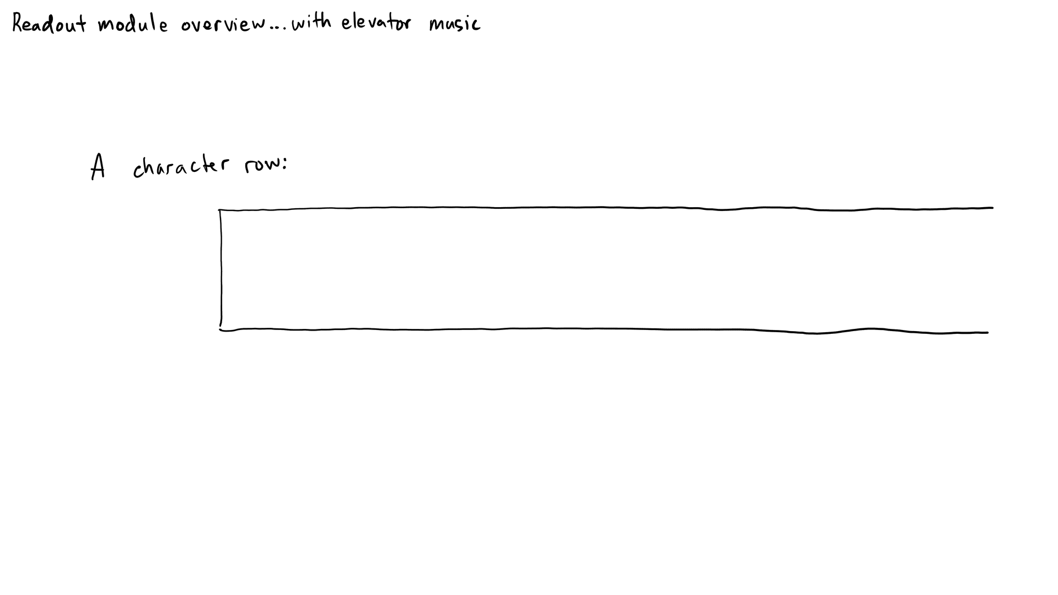
Episode03/Materials/readout-overview-013.png
