daveho/HW_VGA/Episode03/Materials/readout-overview-015.png

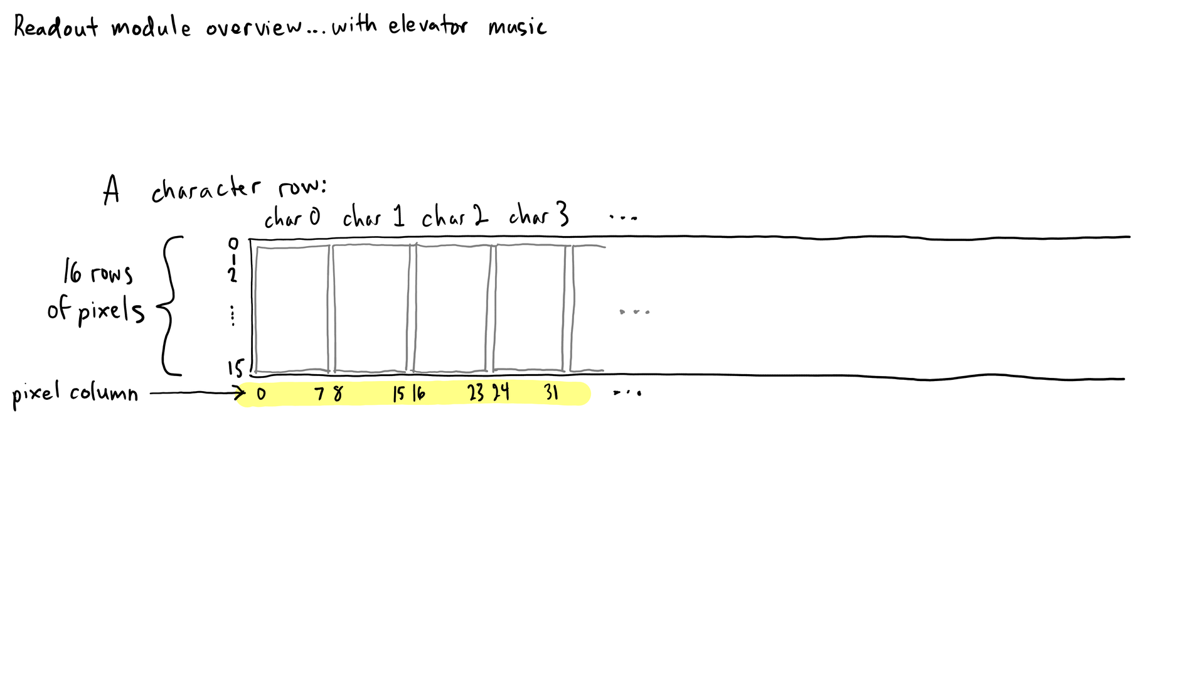
Episode03/Materials/readout-overview-015.png
