daveho/HW_VGA/Episode03/Materials/readout-overview-016.png

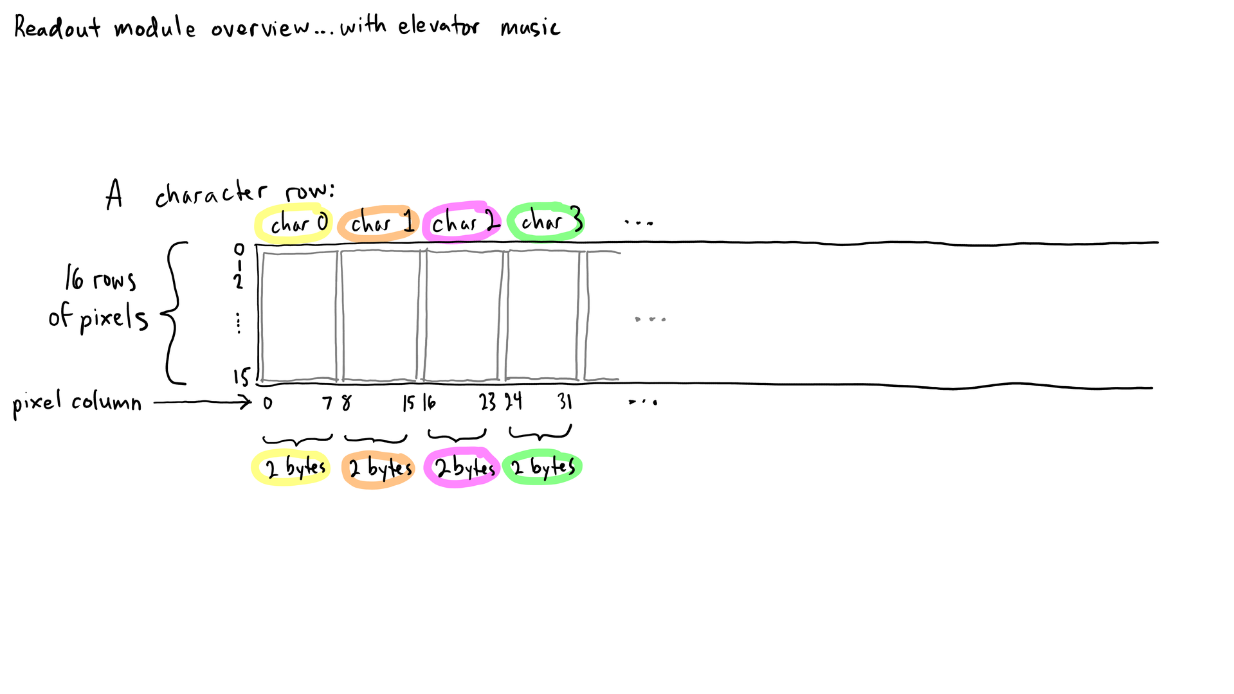
Episode03/Materials/readout-overview-016.png
