daveho/HW_VGA/Episode03/Materials/readout-overview-017.png

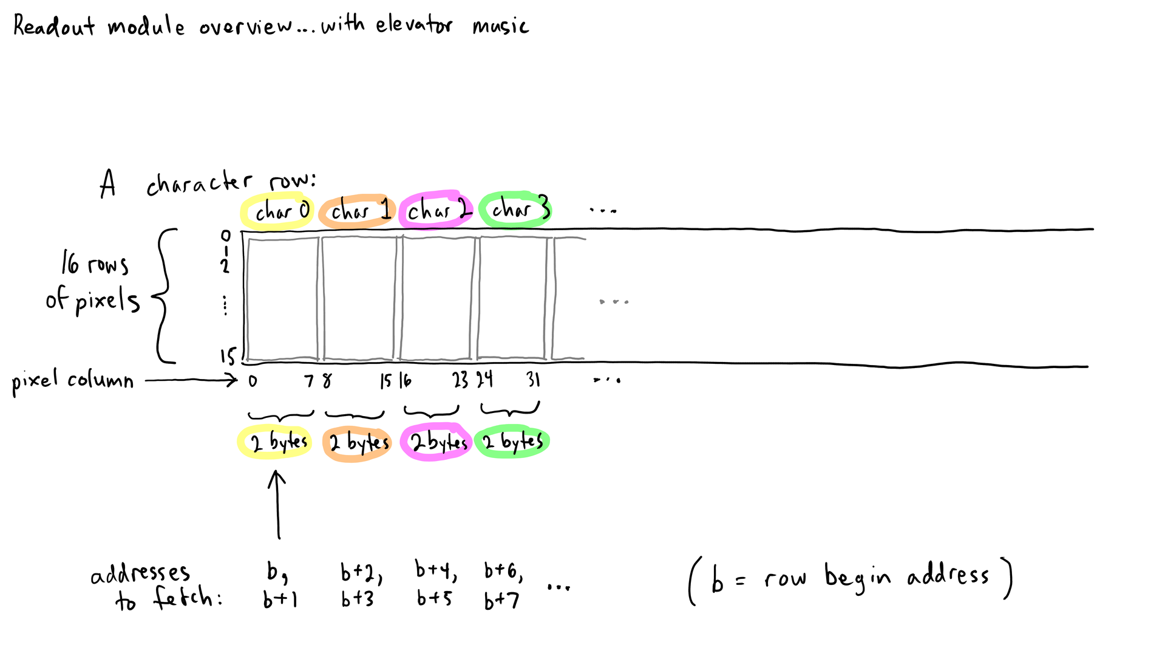
Episode03/Materials/readout-overview-017.png
