daveho/HW_VGA/Episode03/Materials/readout-overview-018.png

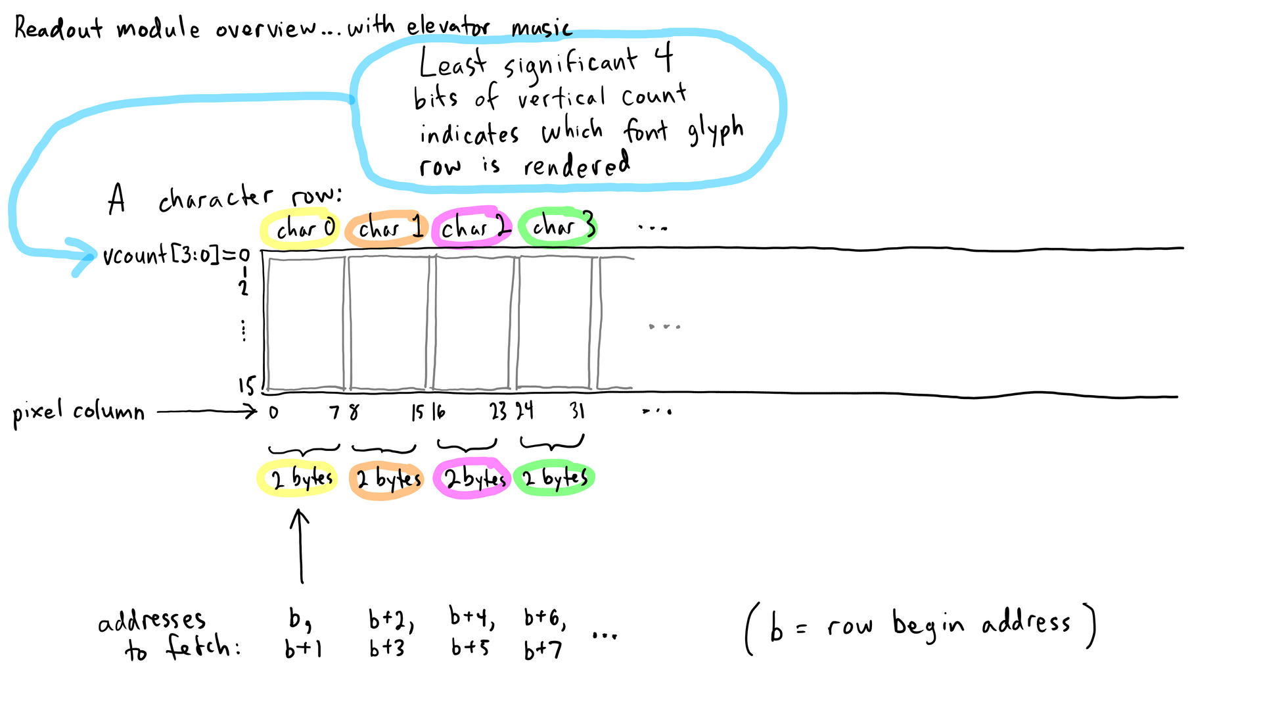
Episode03/Materials/readout-overview-018.png
