daveho/HW_VGA/Episode03/Materials/readout-overview-019.png

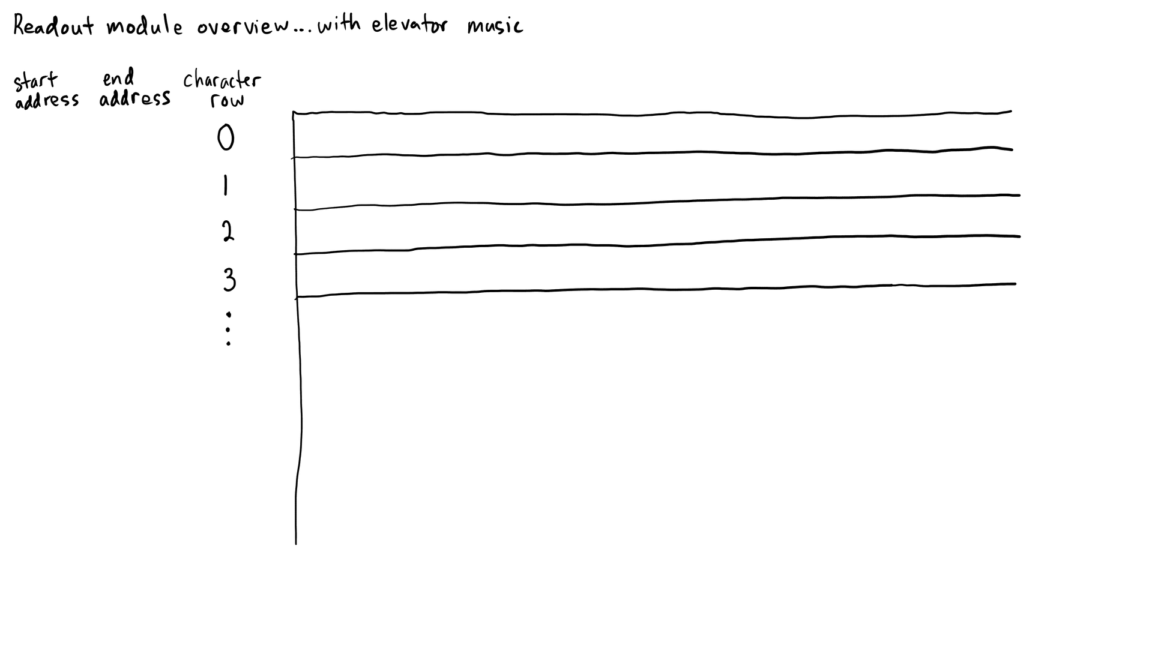
Episode03/Materials/readout-overview-019.png
