daveho/HW_VGA/Episode03/Materials/readout-overview-024.png

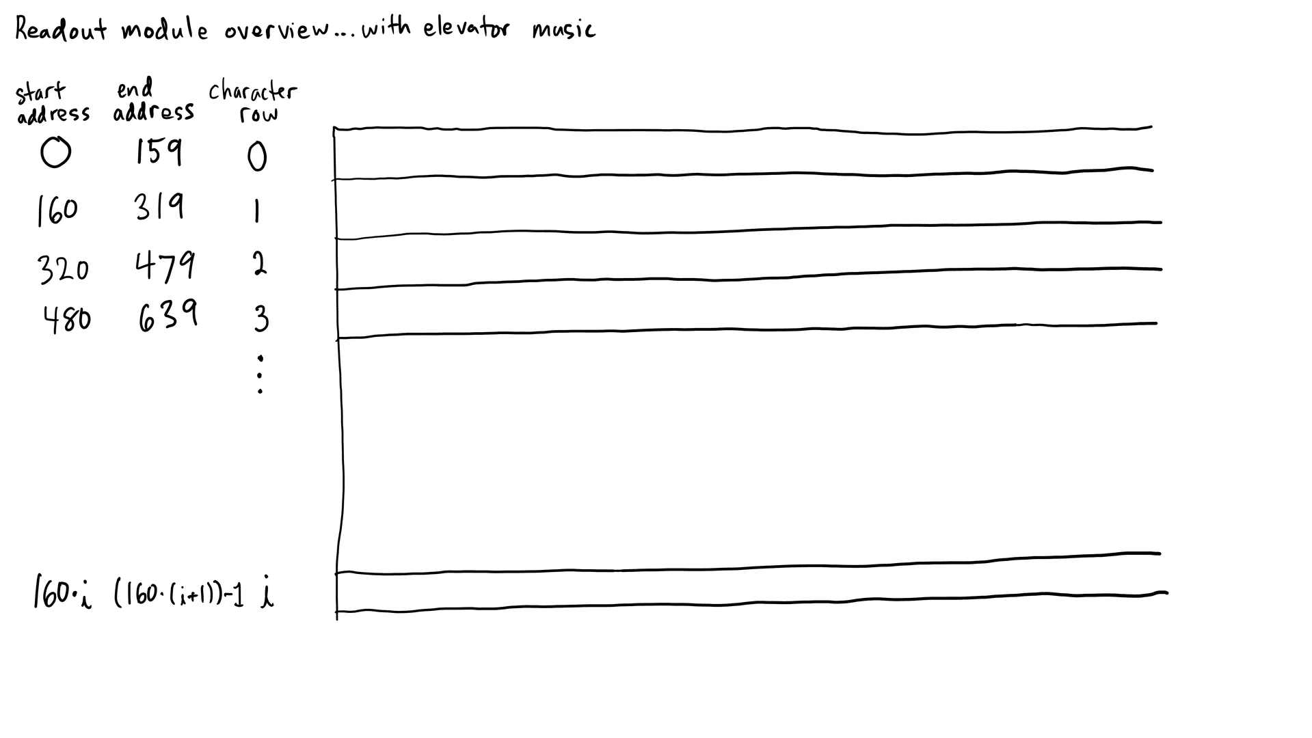
Episode03/Materials/readout-overview-024.png
