daveho/HW_VGA/Episode03/Materials/readout-overview-025.png

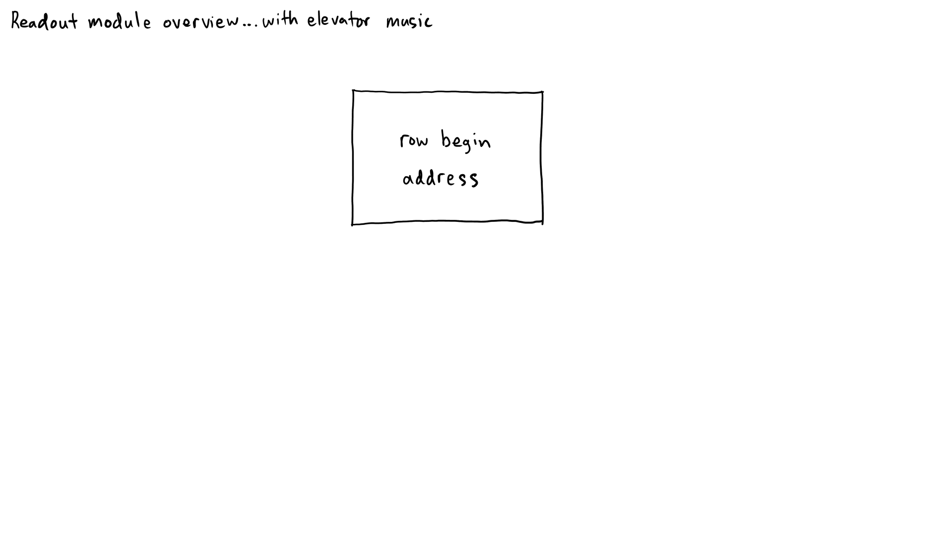
Episode03/Materials/readout-overview-025.png
