daveho/HW_VGA/Episode03/Materials/readout-overview-026.png

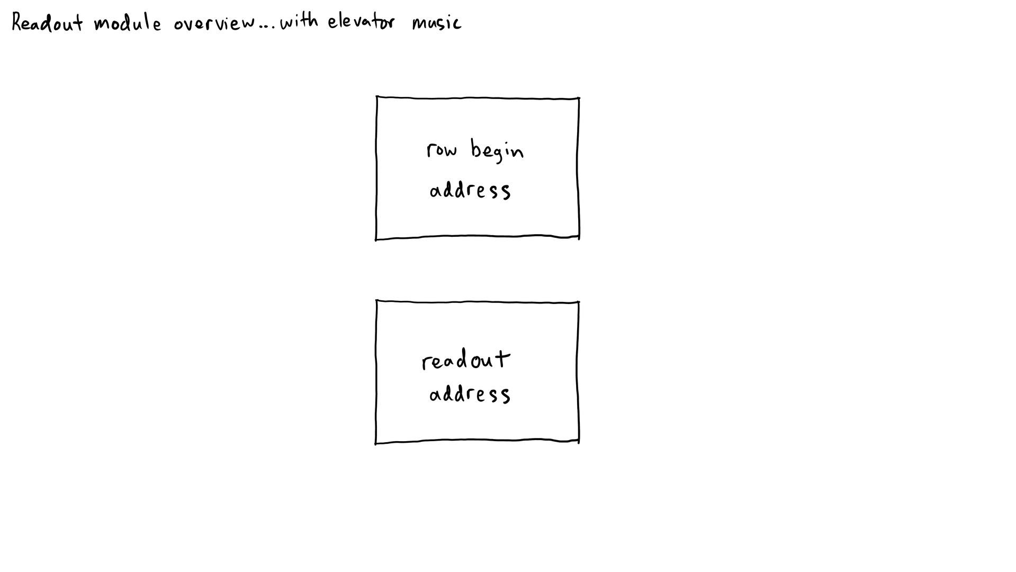
Episode03/Materials/readout-overview-026.png
