daveho/HW_VGA/Episode03/Materials/readout-overview-027.png

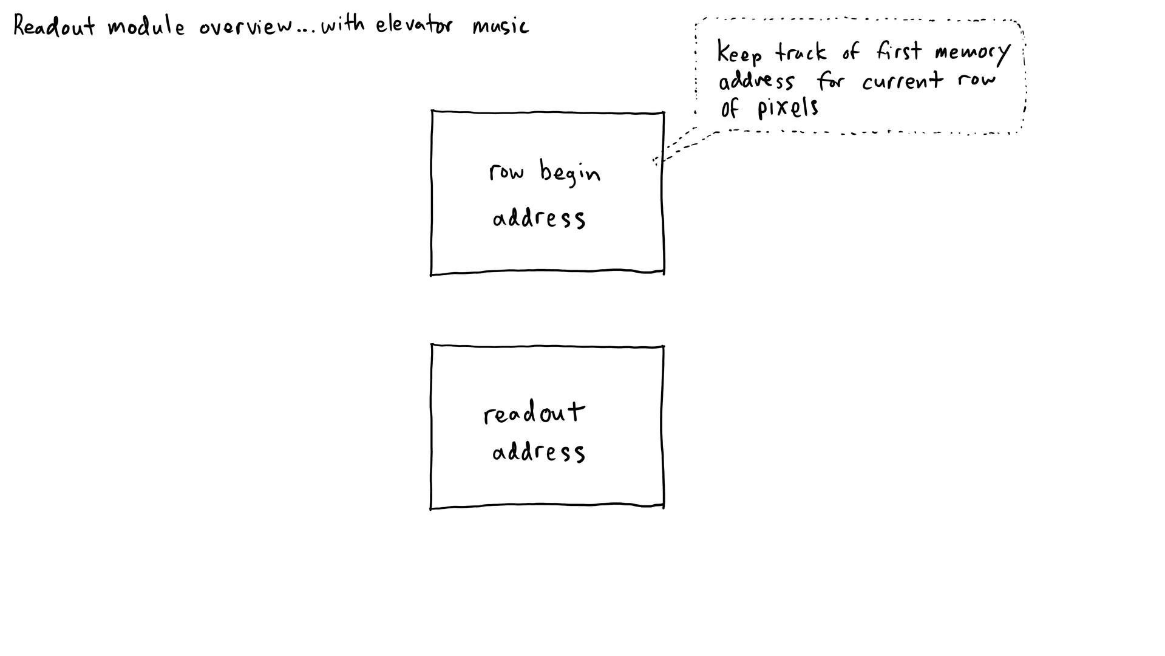
Episode03/Materials/readout-overview-027.png
