daveho/HW_VGA/Episode03/Materials/readout-overview-028.png

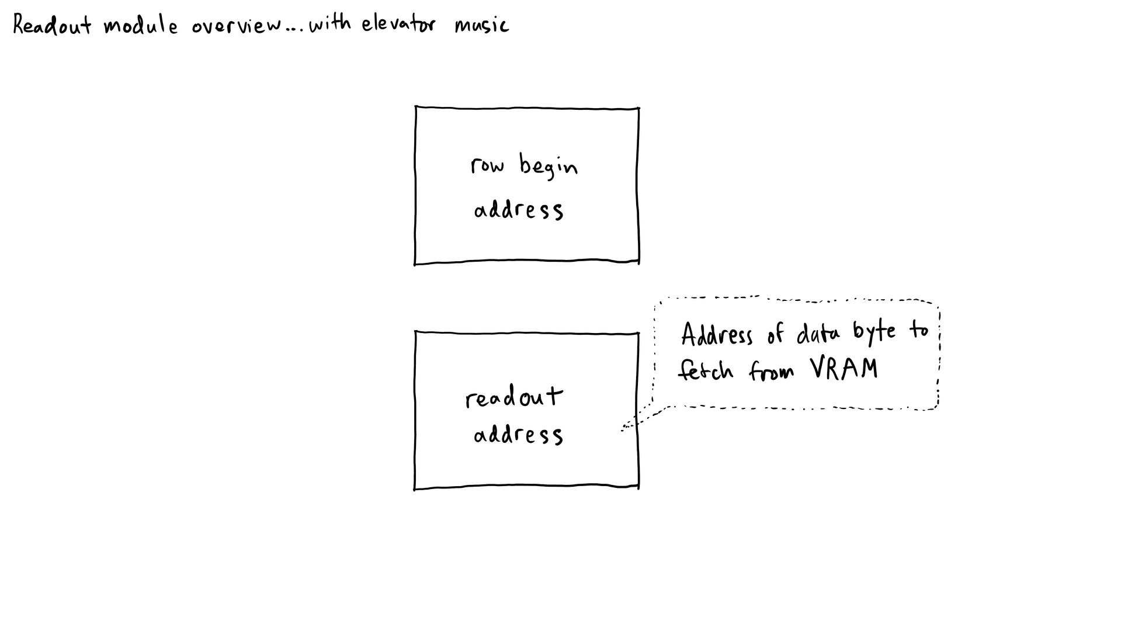
Episode03/Materials/readout-overview-028.png
