daveho/HW_VGA/Episode03/Materials/readout-overview-029.png

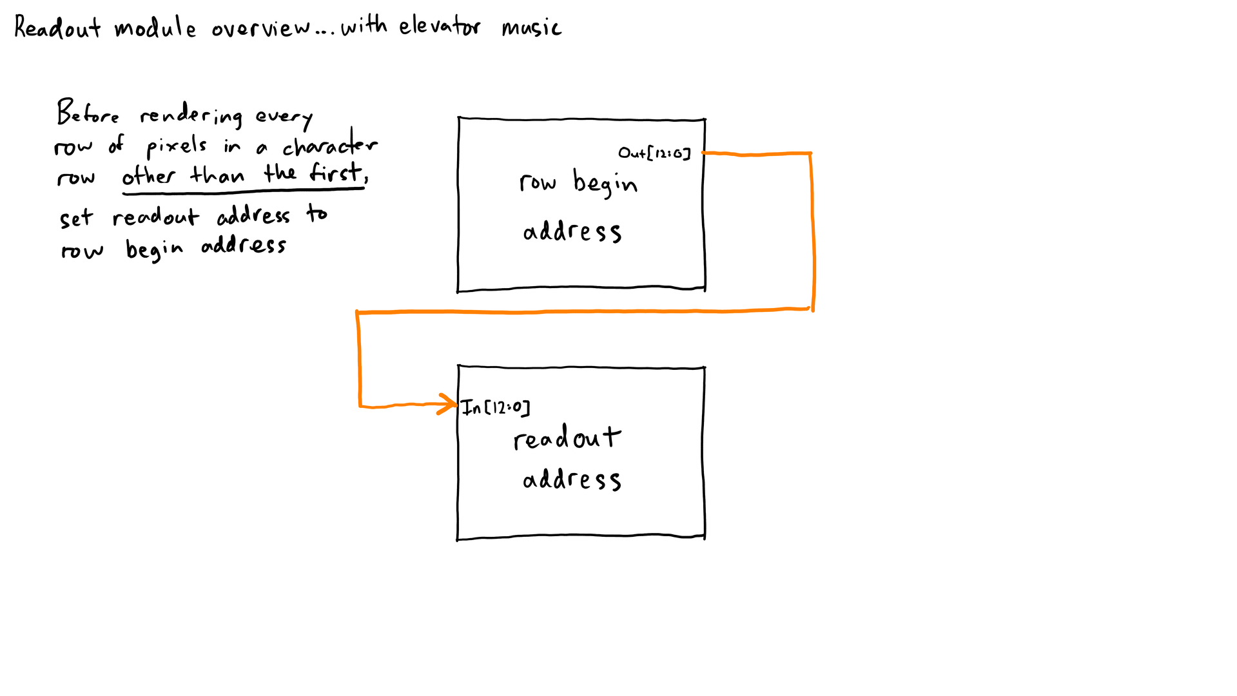
Episode03/Materials/readout-overview-029.png
