daveho/HW_VGA/Episode03/Materials/readout-overview-032.png

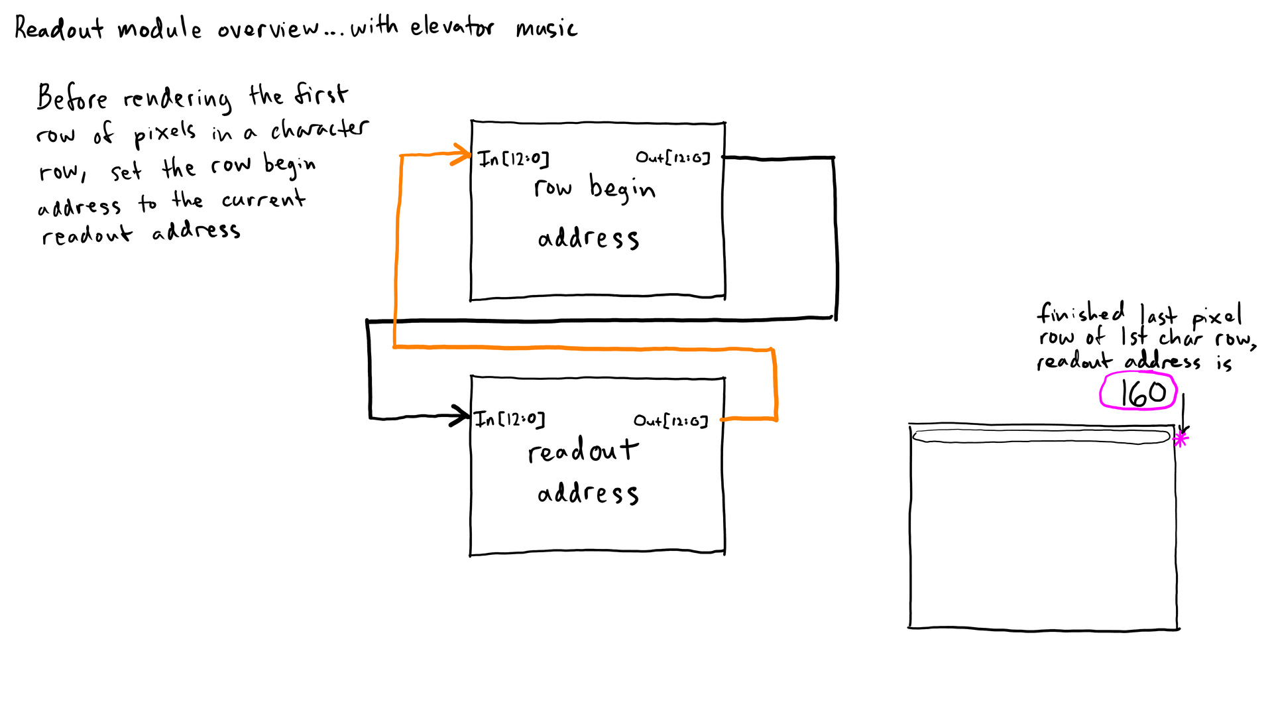
Episode03/Materials/readout-overview-032.png
