daveho/HW_VGA/Episode03/Materials/readout-overview-033.png

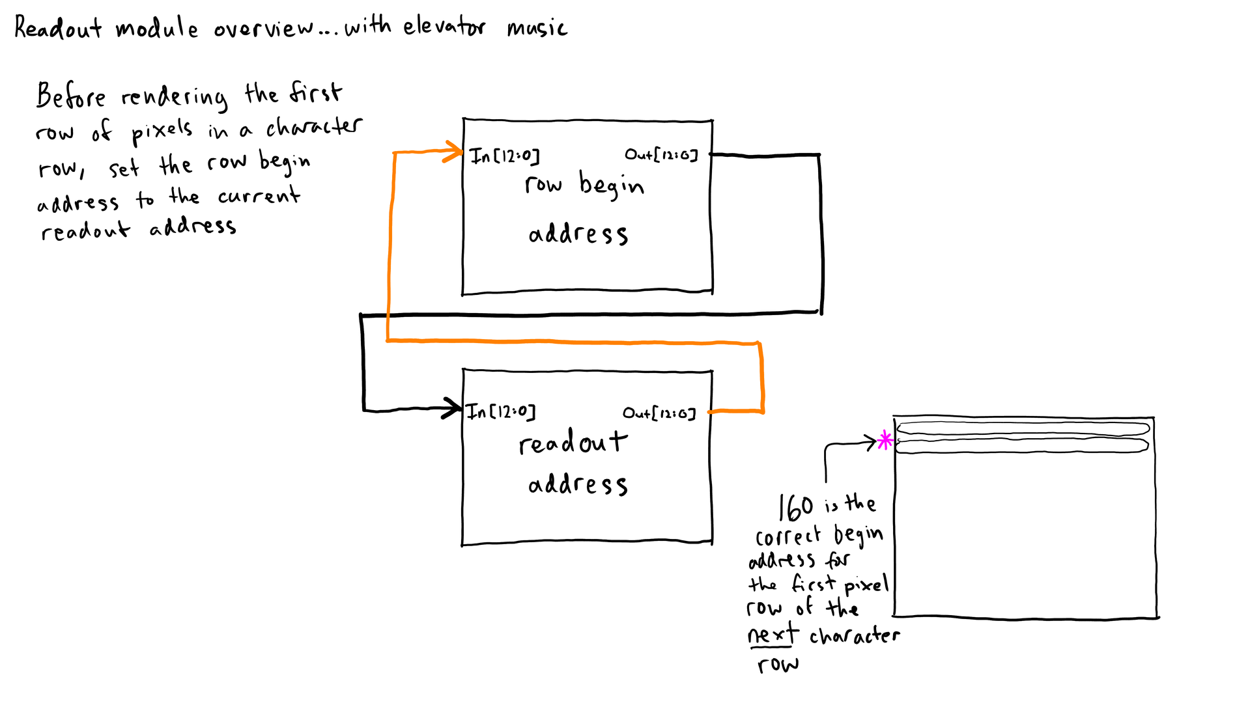
Episode03/Materials/readout-overview-033.png
