daveho/HW_VGA/Episode03/Materials/readout-overview-035.png

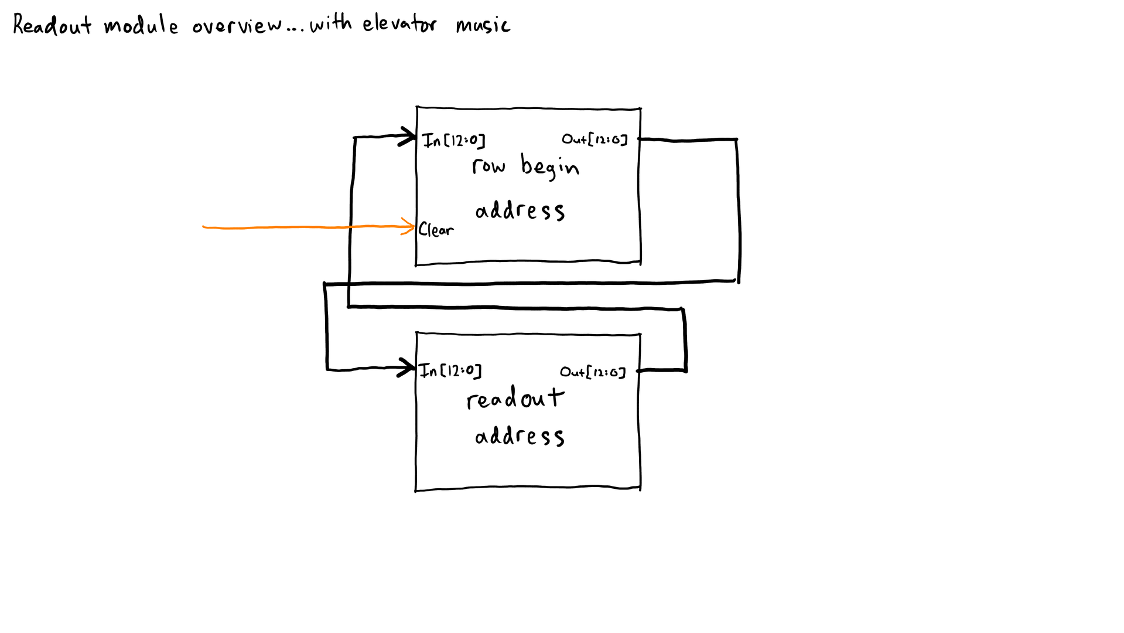
Episode03/Materials/readout-overview-035.png
