daveho/HW_VGA/Episode03/Materials/readout-overview-037a.png

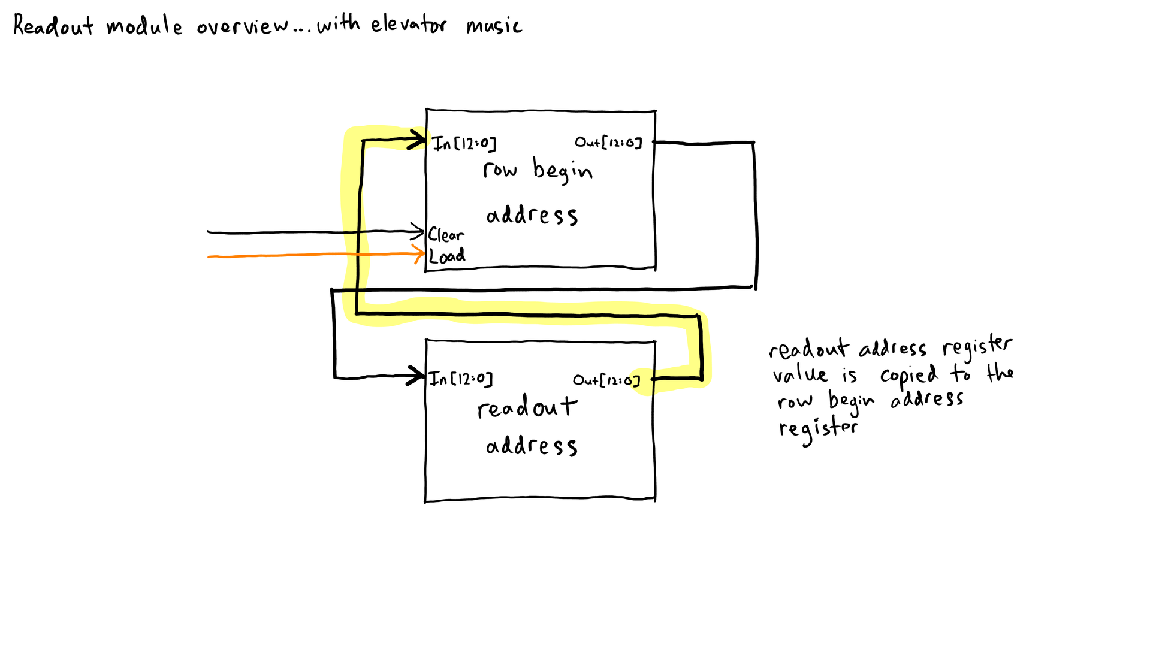
Episode03/Materials/readout-overview-037a.png
