daveho/HW_VGA/Episode03/Materials/readout-overview-039a.png

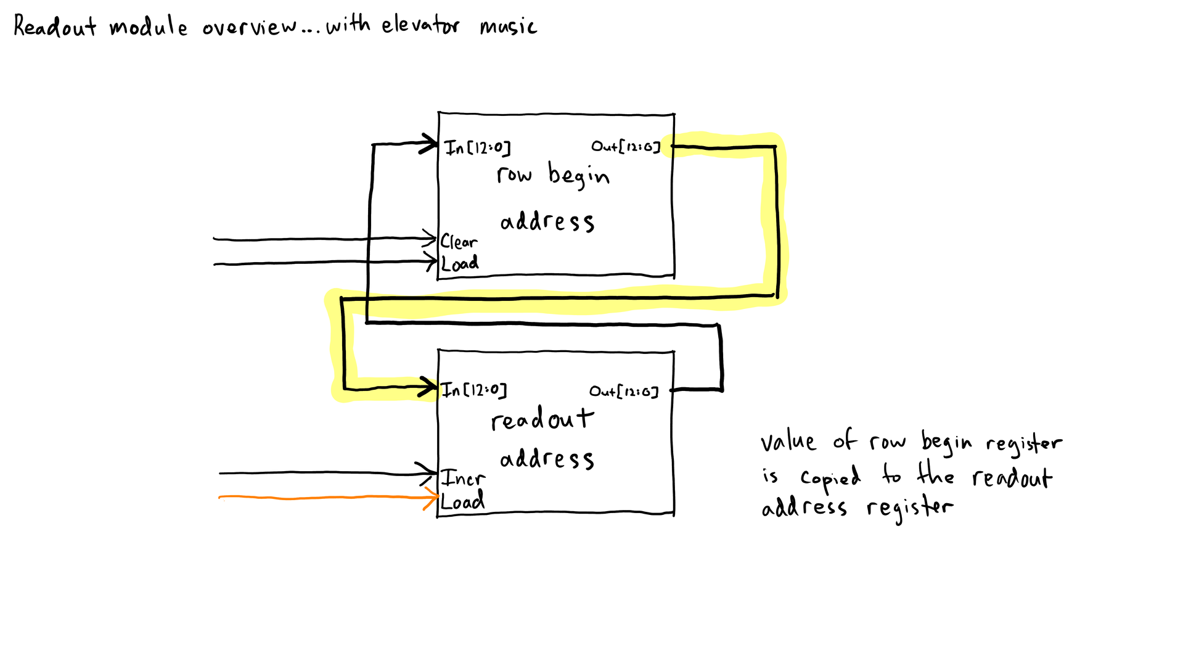
Episode03/Materials/readout-overview-039a.png
