daveho/HW_VGA/Episode03/Materials/readout-overview-040.png

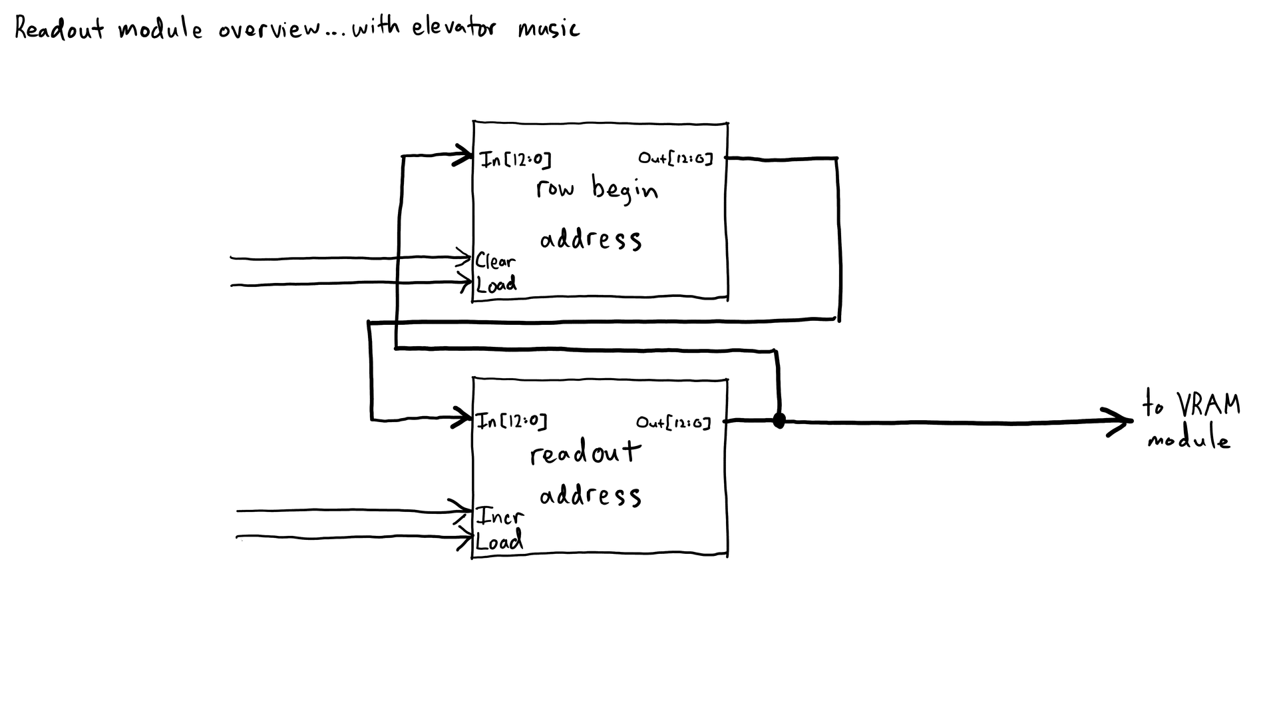
Episode03/Materials/readout-overview-040.png
