daveho/HW_VGA/Episode03/Materials/readout-overview-047.png

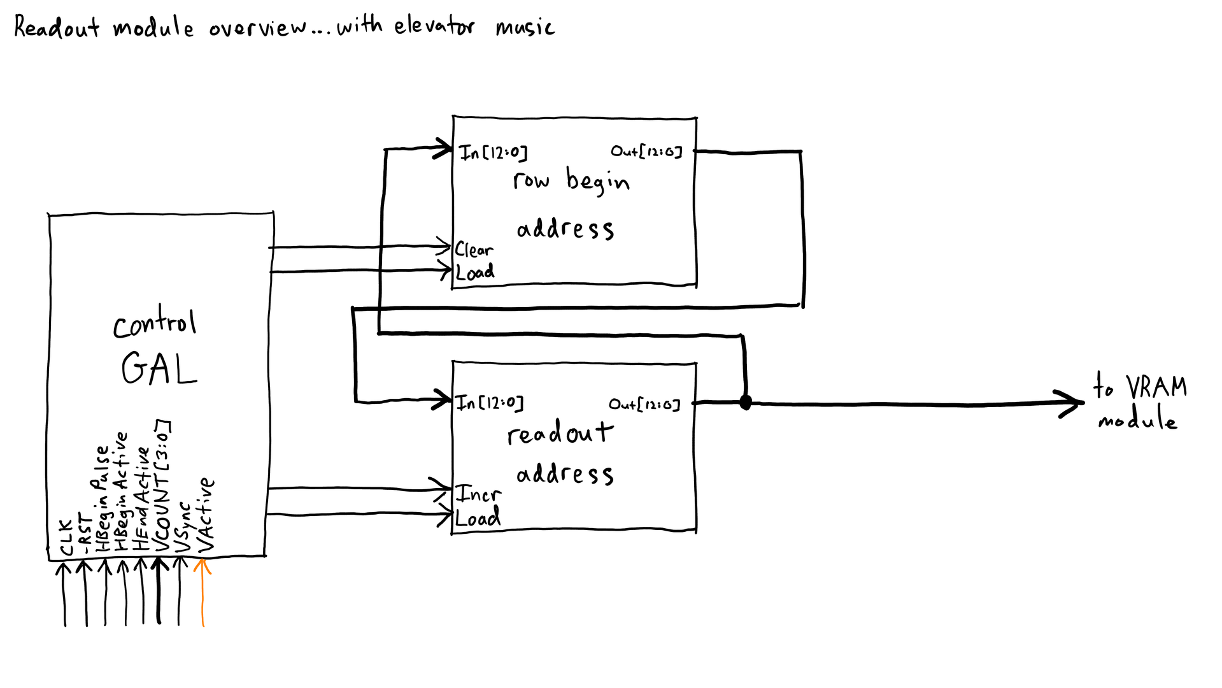
Episode03/Materials/readout-overview-047.png
