daveho/HW_VGA/Episode03/Materials/readout-overview-050.png

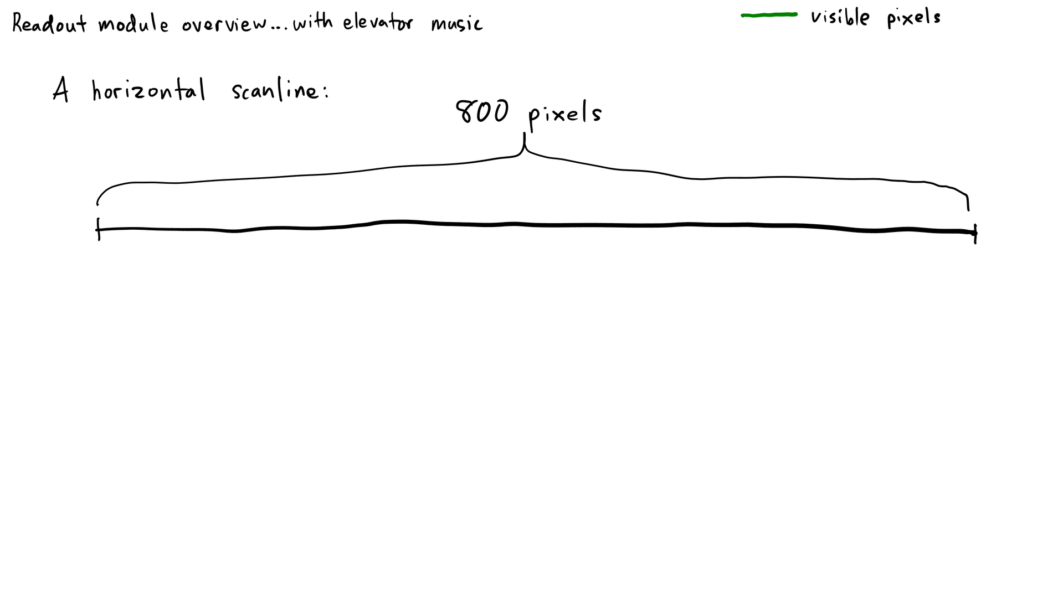
Episode03/Materials/readout-overview-050.png
