daveho/HW_VGA/Episode03/Materials/readout-overview-051.png

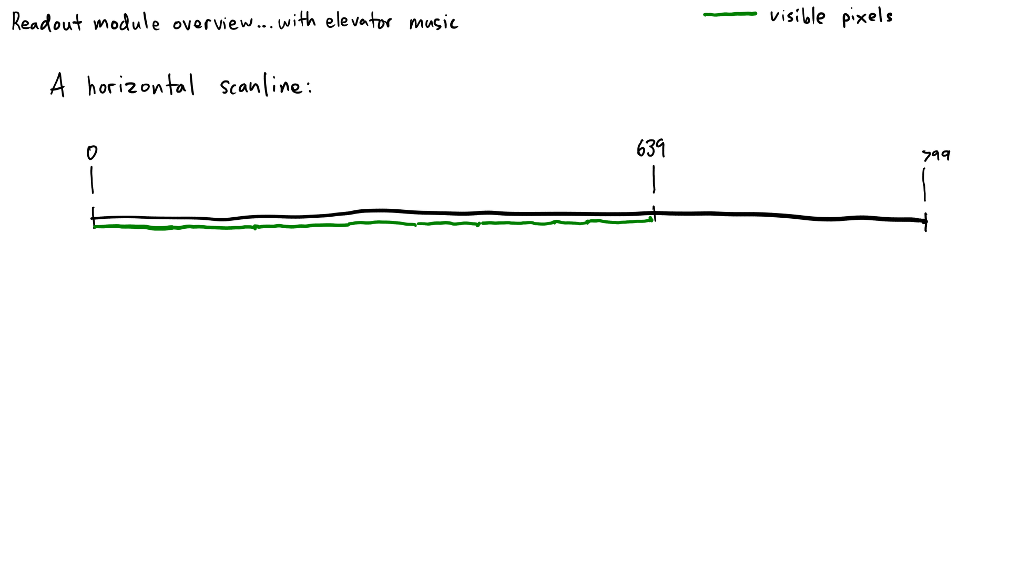
Episode03/Materials/readout-overview-051.png
