daveho/HW_VGA/Episode03/Materials/readout-overview-052.png

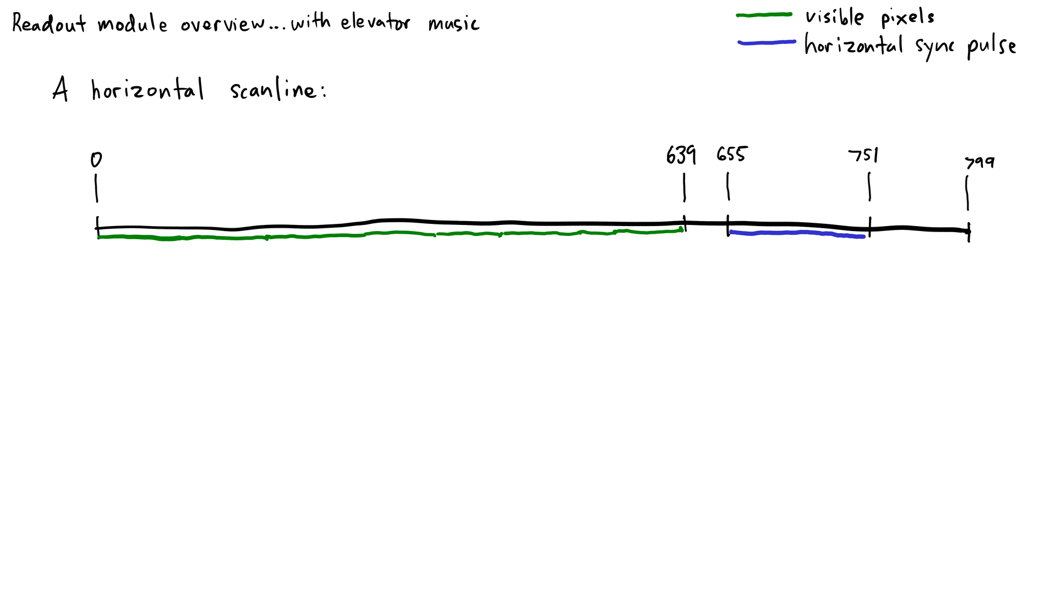
Episode03/Materials/readout-overview-052.png
