daveho/HW_VGA/Episode03/Materials/readout-overview-053.png

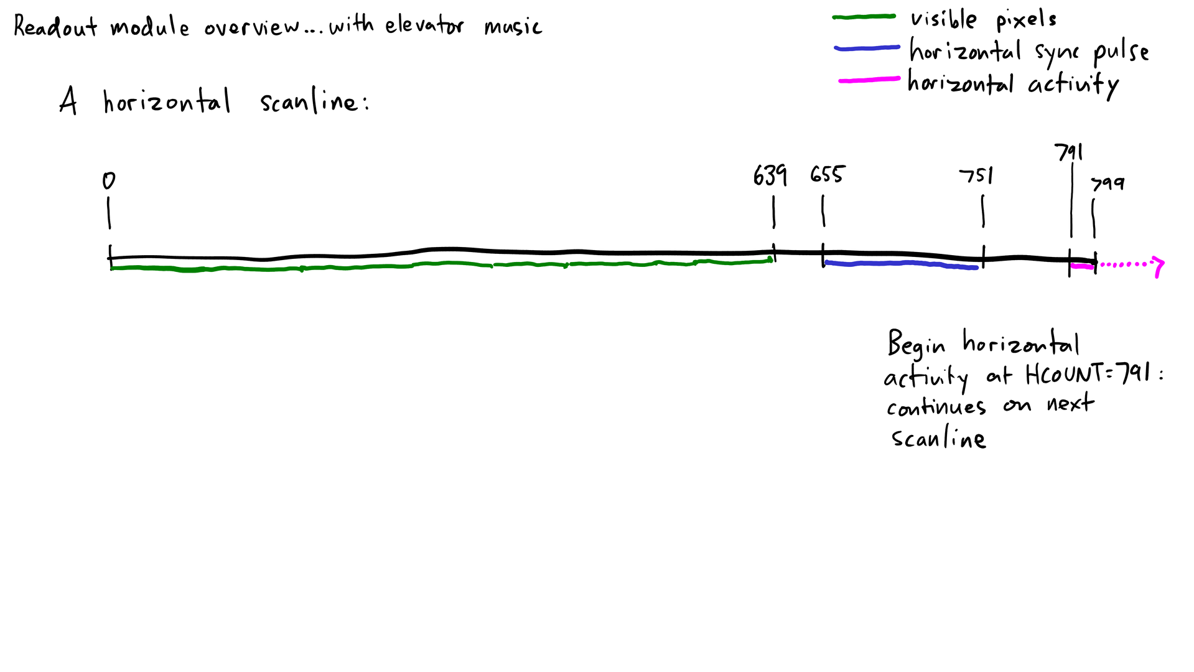
Episode03/Materials/readout-overview-053.png
