daveho/HW_VGA/Episode03/Materials/readout-overview-054.png

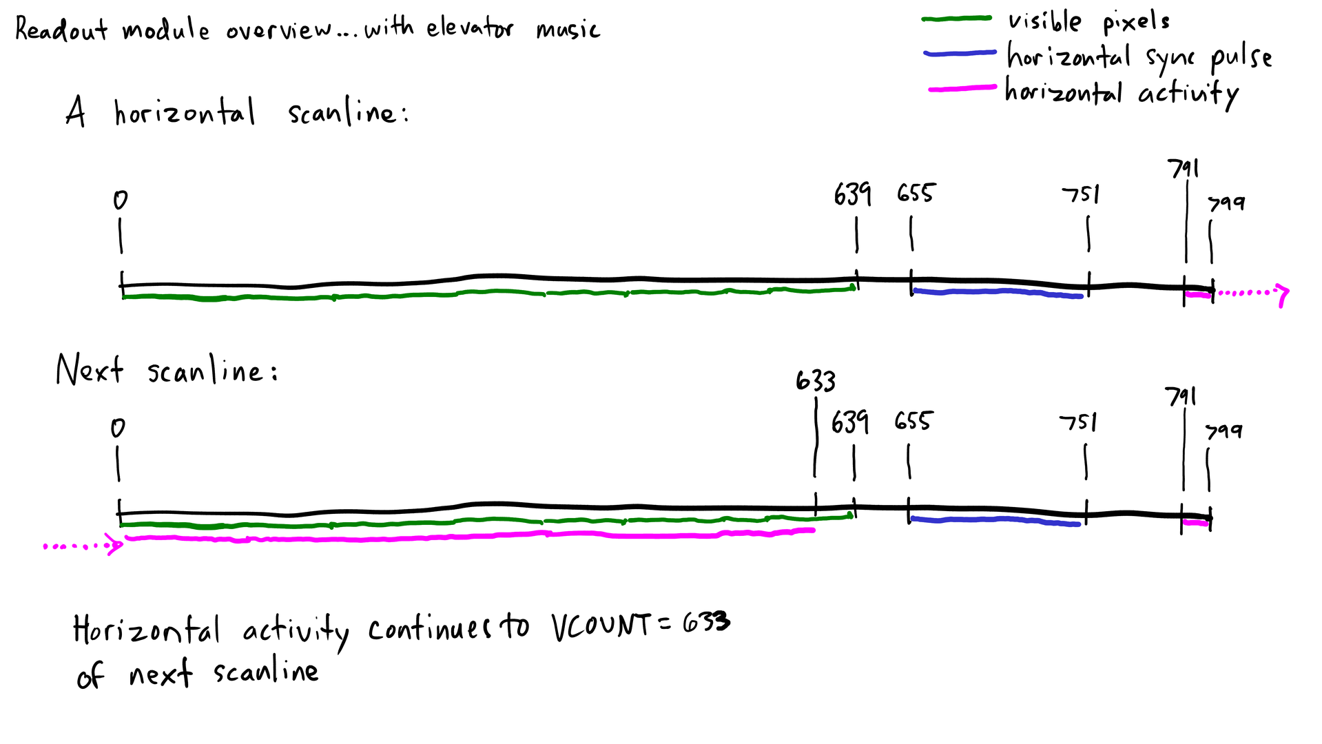
Episode03/Materials/readout-overview-054.png
