daveho/HW_VGA/Episode03/Materials/readout-overview-055.png

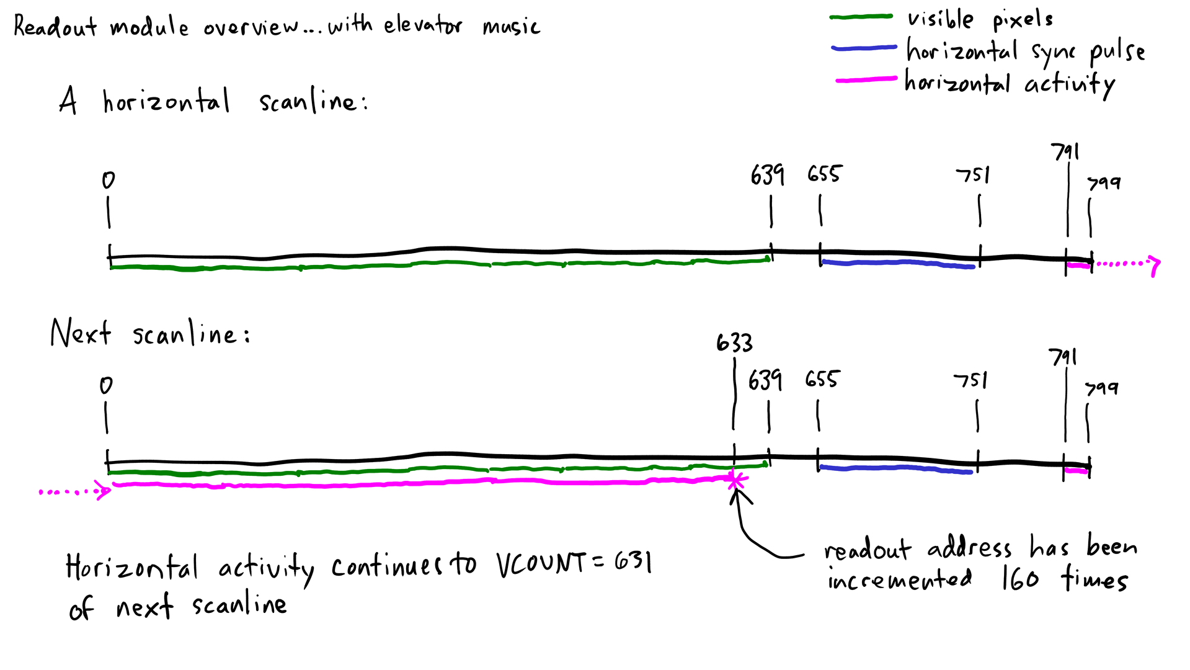
Episode03/Materials/readout-overview-055.png
