daveho/HW_VGA/Episode03/Materials/readout-overview-056.png

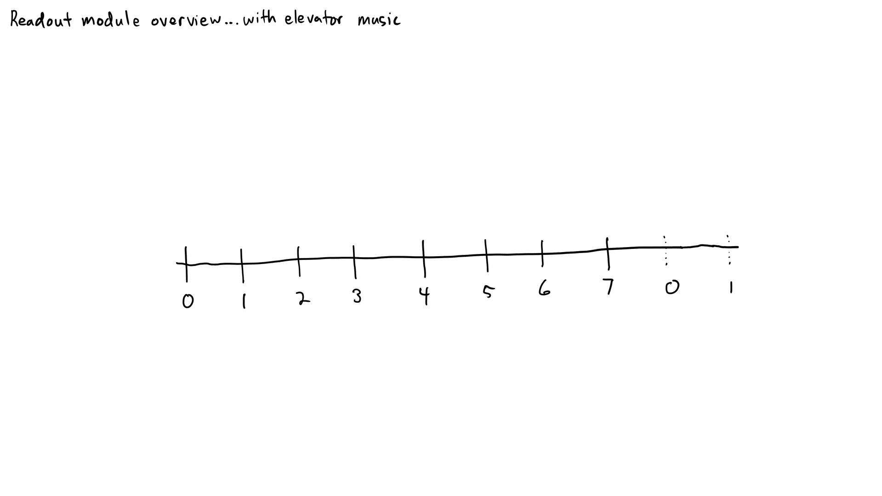
Episode03/Materials/readout-overview-056.png
