daveho/HW_VGA/Episode03/Materials/readout-overview-057.png

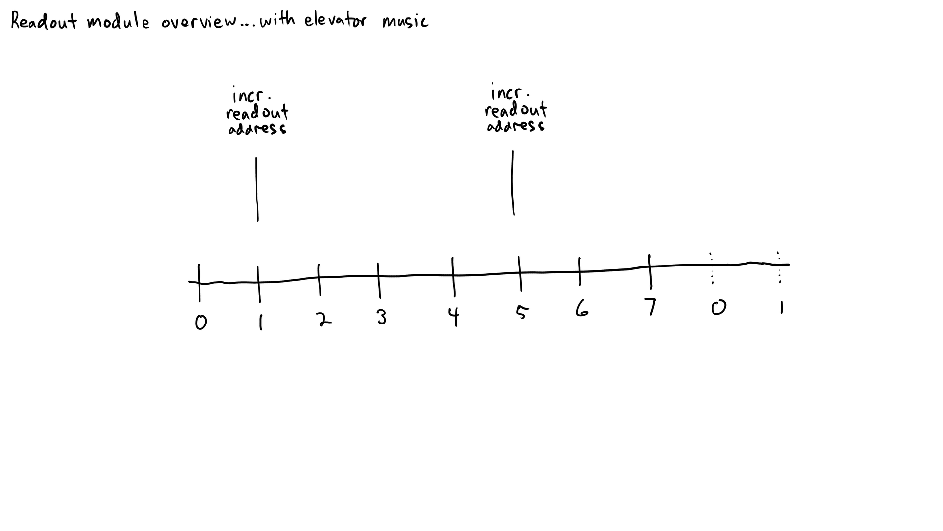
Episode03/Materials/readout-overview-057.png
