daveho/HW_VGA/Episode03/Materials/readout-overview-058.png

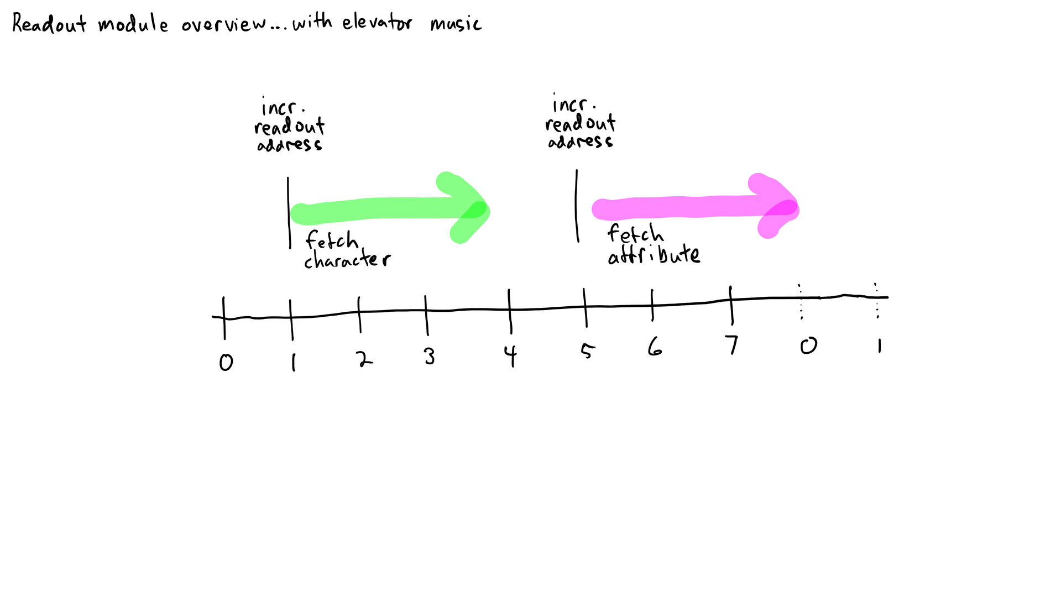
Episode03/Materials/readout-overview-058.png
