daveho/HW_VGA/Episode03/Materials/readout-overview-060.png

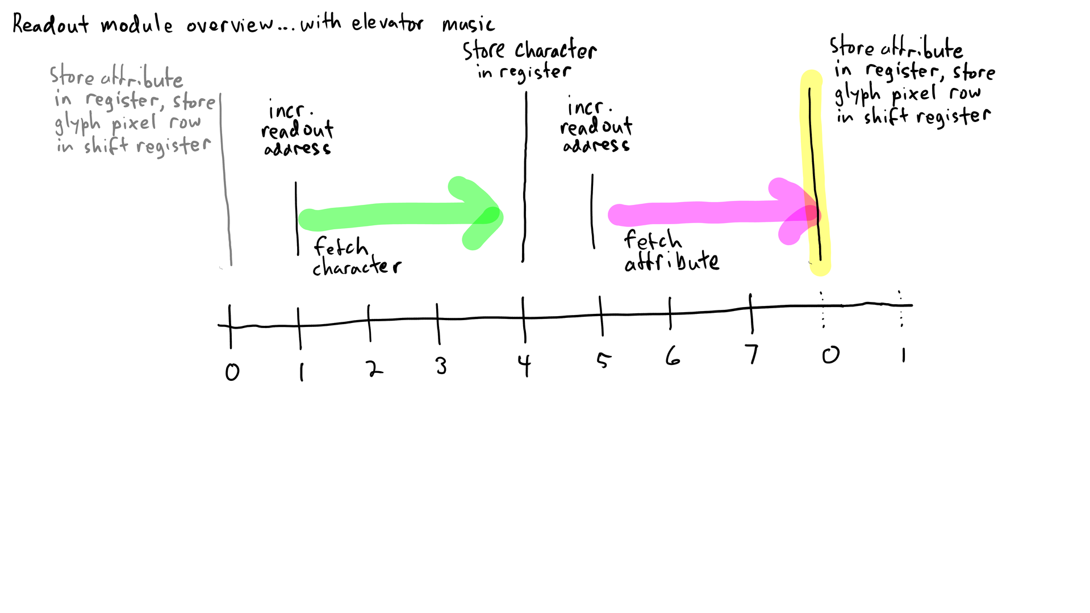
Episode03/Materials/readout-overview-060.png
