daveho/HW_VGA/Episode03/Materials/readout-overview-061.png

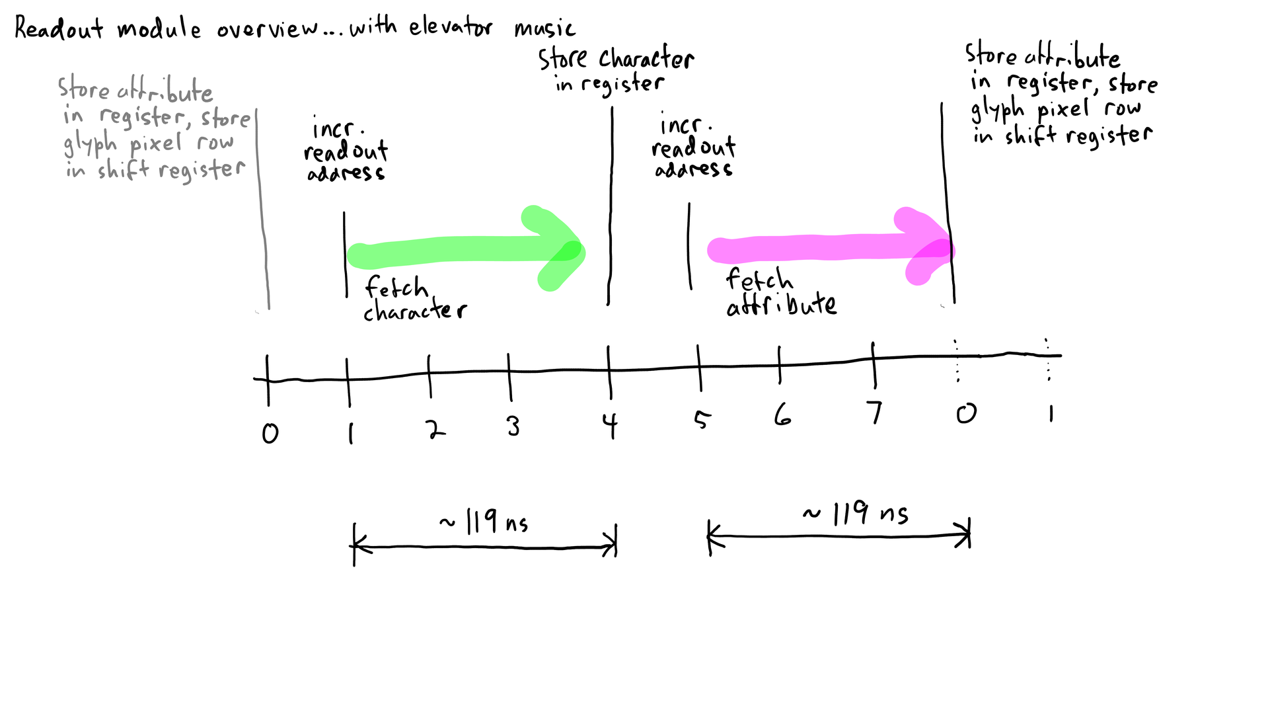
Episode03/Materials/readout-overview-061.png
