daveho/HW_VGA/Episode03/Materials/readout-overview-063.png

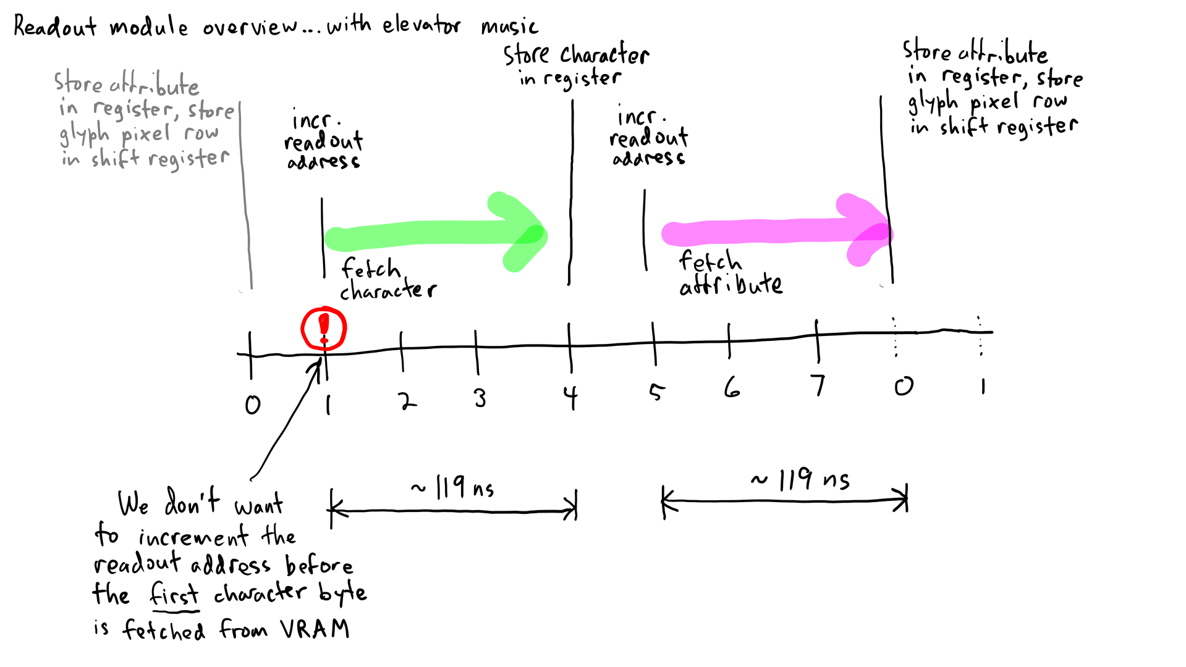
Episode03/Materials/readout-overview-063.png
