daveho/HW_VGA/Episode03/Materials/readout-overview-064.png

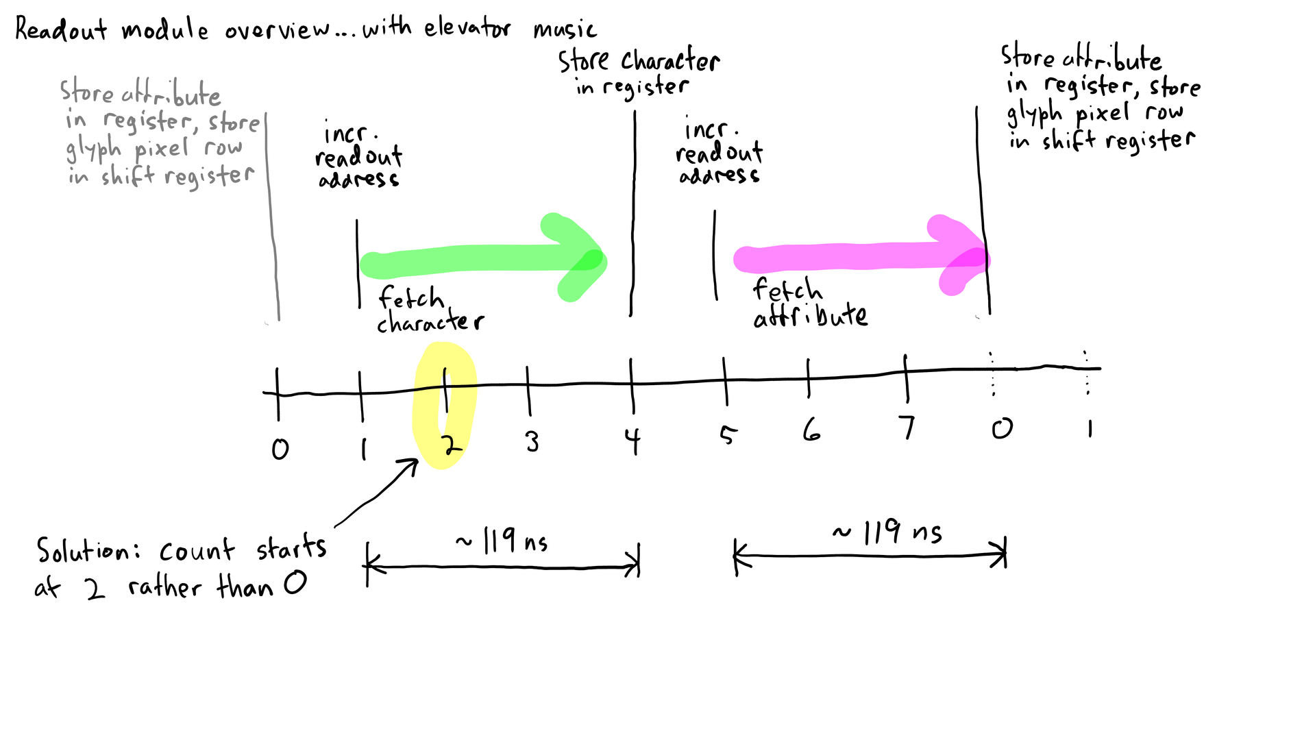
Episode03/Materials/readout-overview-064.png
