daveho/HW_VGA/Episode03/Materials/readout-overview-066.png

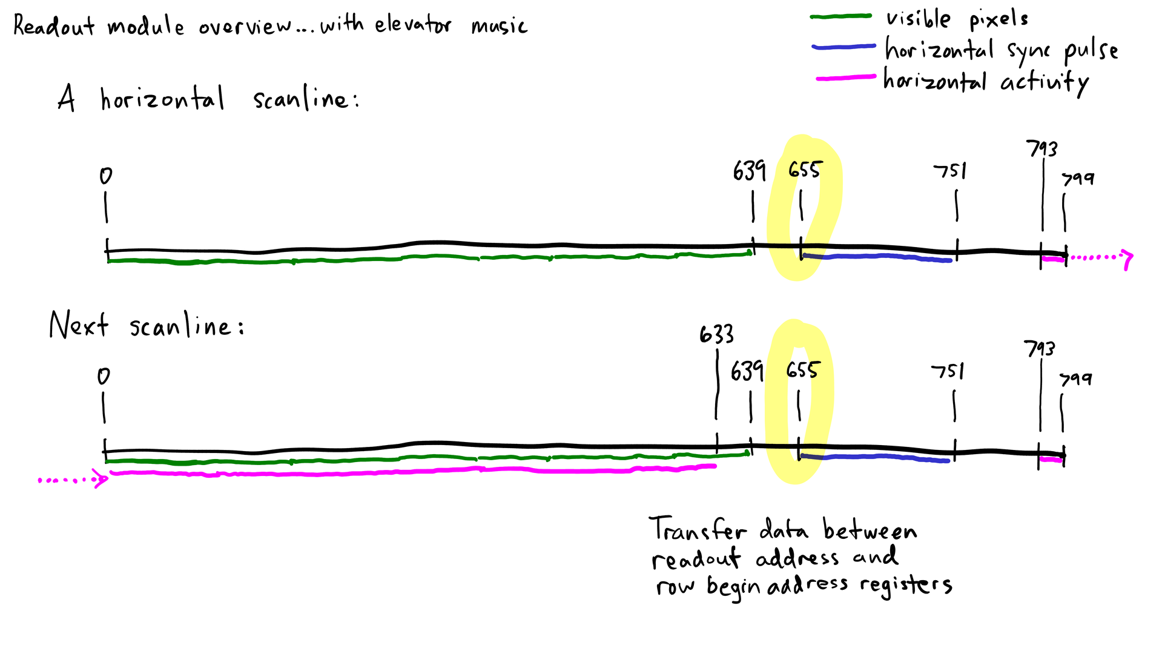
Episode03/Materials/readout-overview-066.png
