daveho/HW_VGA/Episode03/Materials/readout-overview-067.png

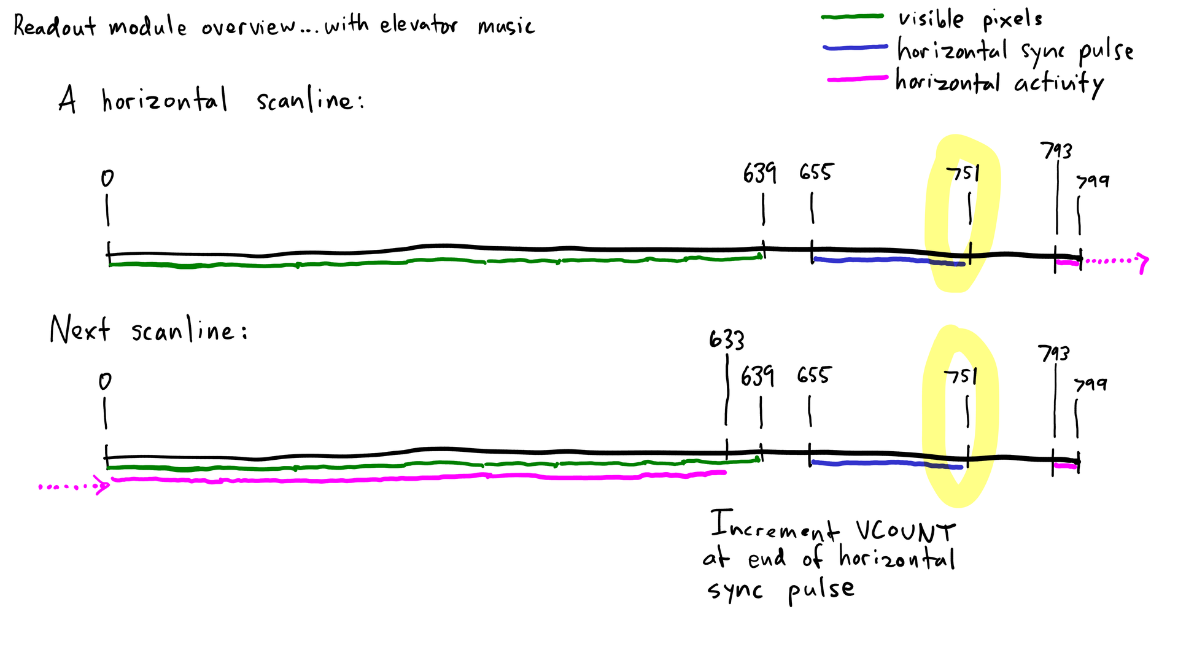
Episode03/Materials/readout-overview-067.png
