daveho/HW_VGA/Episode03/Materials/schematic_01.png

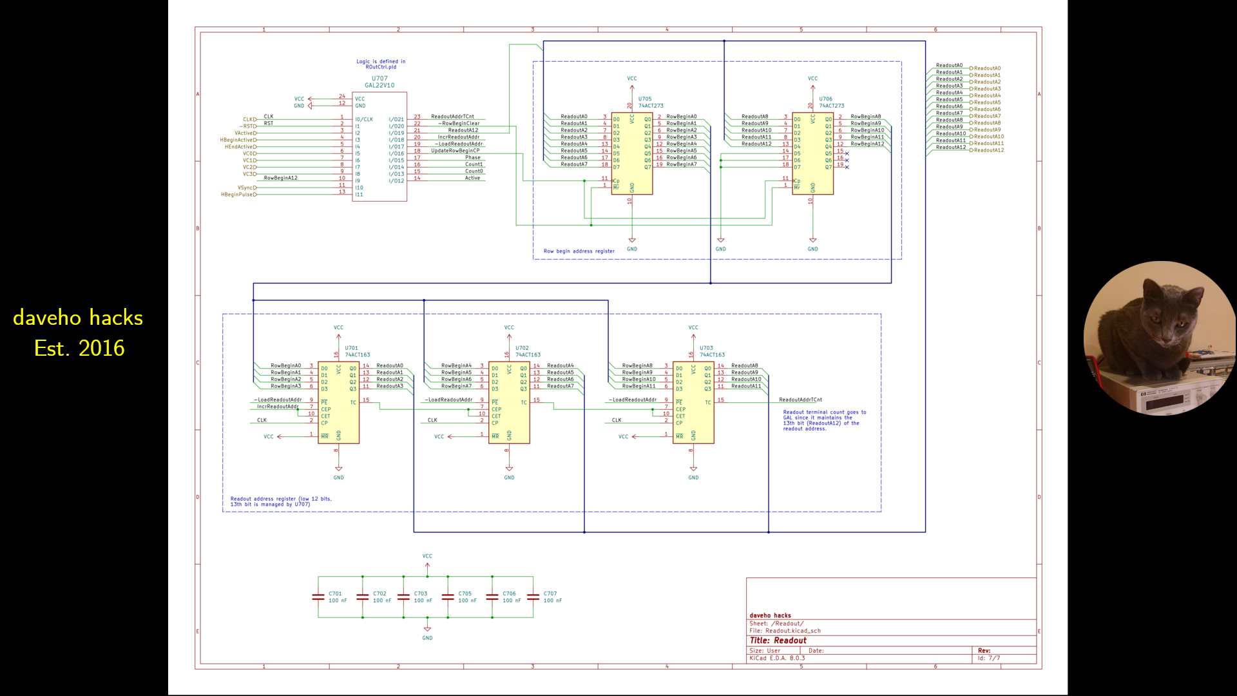
Episode03/Materials/schematic_01.png
