daveho/HW_VGA/Episode04/Materials/schematic-050.png

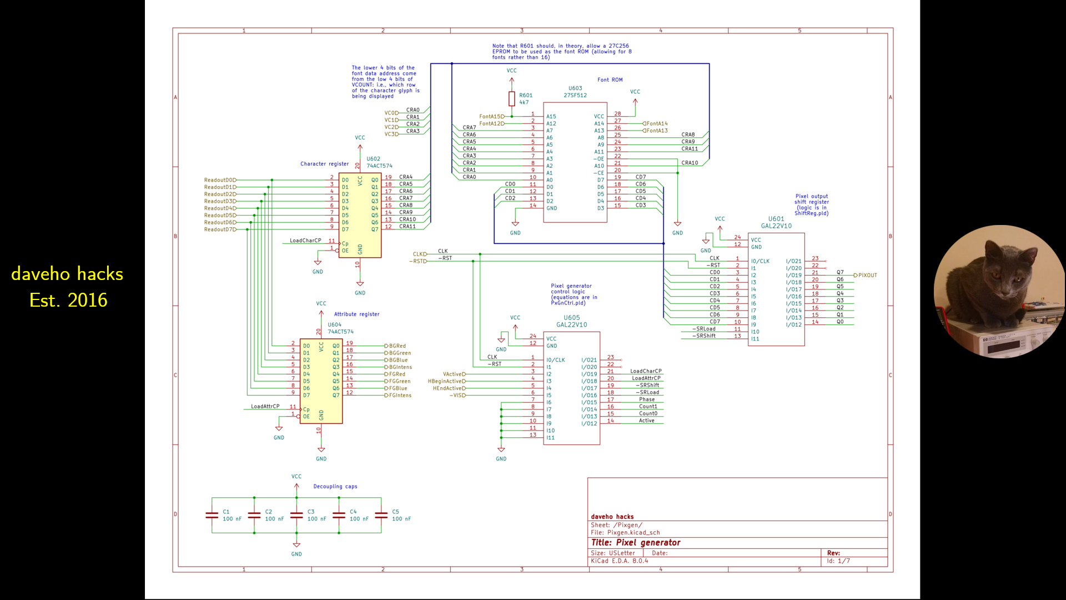
Episode04/Materials/schematic-050.png
