daveho/HW_VGA/Episode04/Materials/theory-001.png

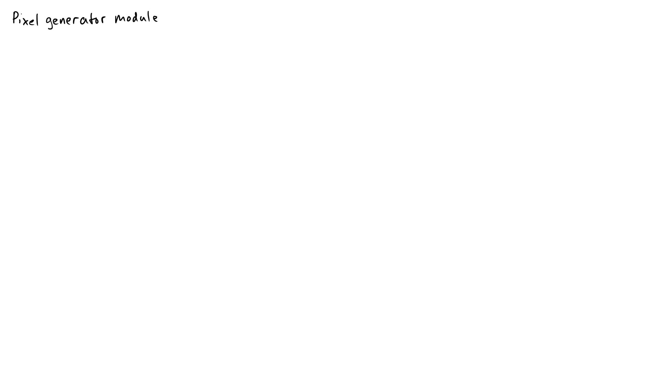
Episode04/Materials/theory-001.png
