daveho/HW_VGA/Episode04/Materials/theory-003.png

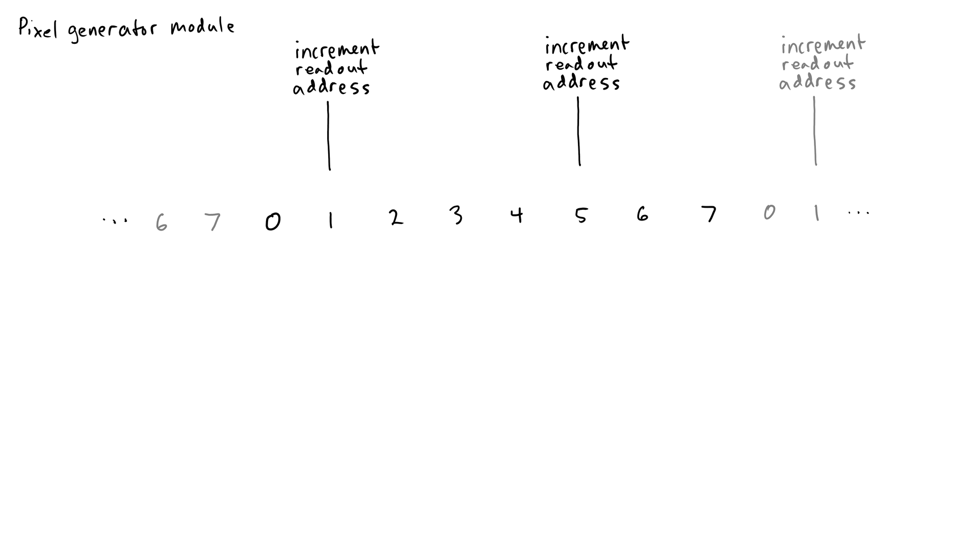
Episode04/Materials/theory-003.png
