daveho/HW_VGA/Episode04/Materials/theory-005.png

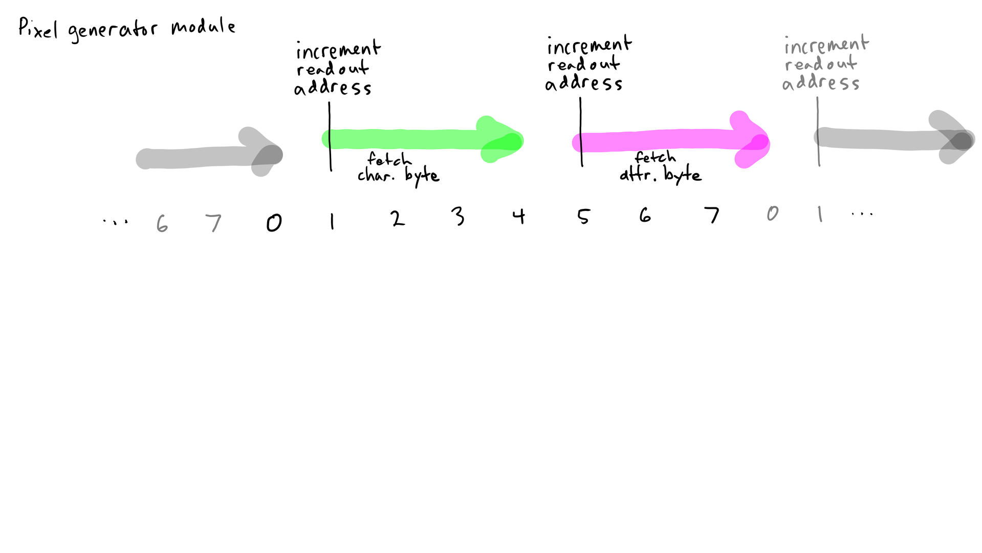
Episode04/Materials/theory-005.png
