daveho/HW_VGA/Episode04/Materials/theory-007.png

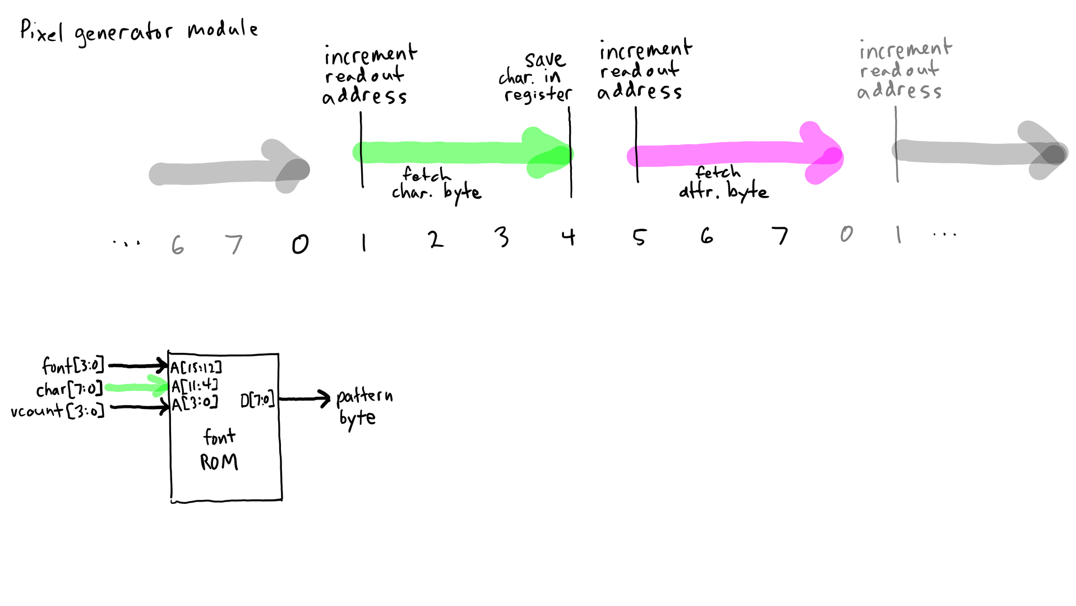
Episode04/Materials/theory-007.png
