daveho/HW_VGA/Episode04/Materials/theory-009.png

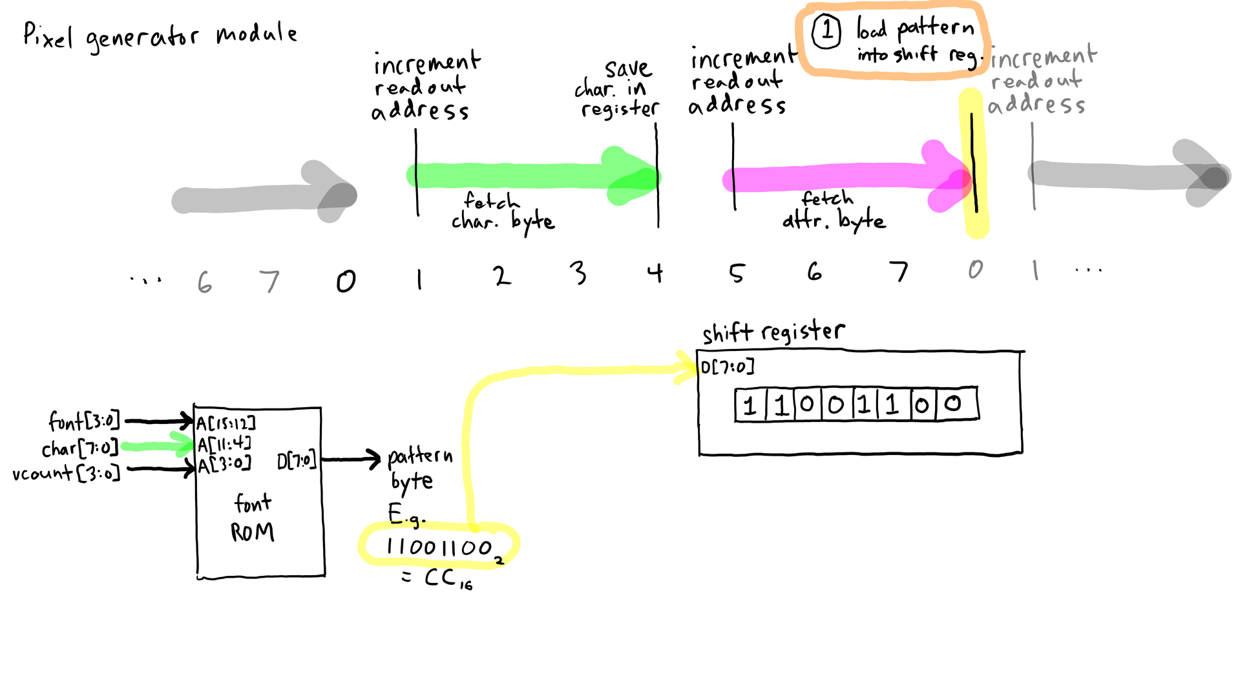
Episode04/Materials/theory-009.png
