daveho/HW_VGA/img/ingo_pic.png

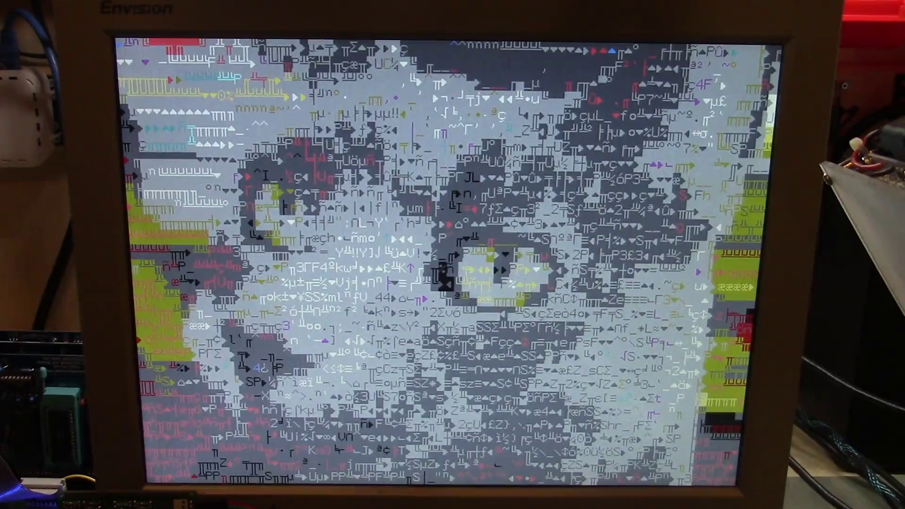
img/ingo_pic.png
