daveho/HW_VGA/Episode02/Materials/HW_VGA_001_vram_module.png

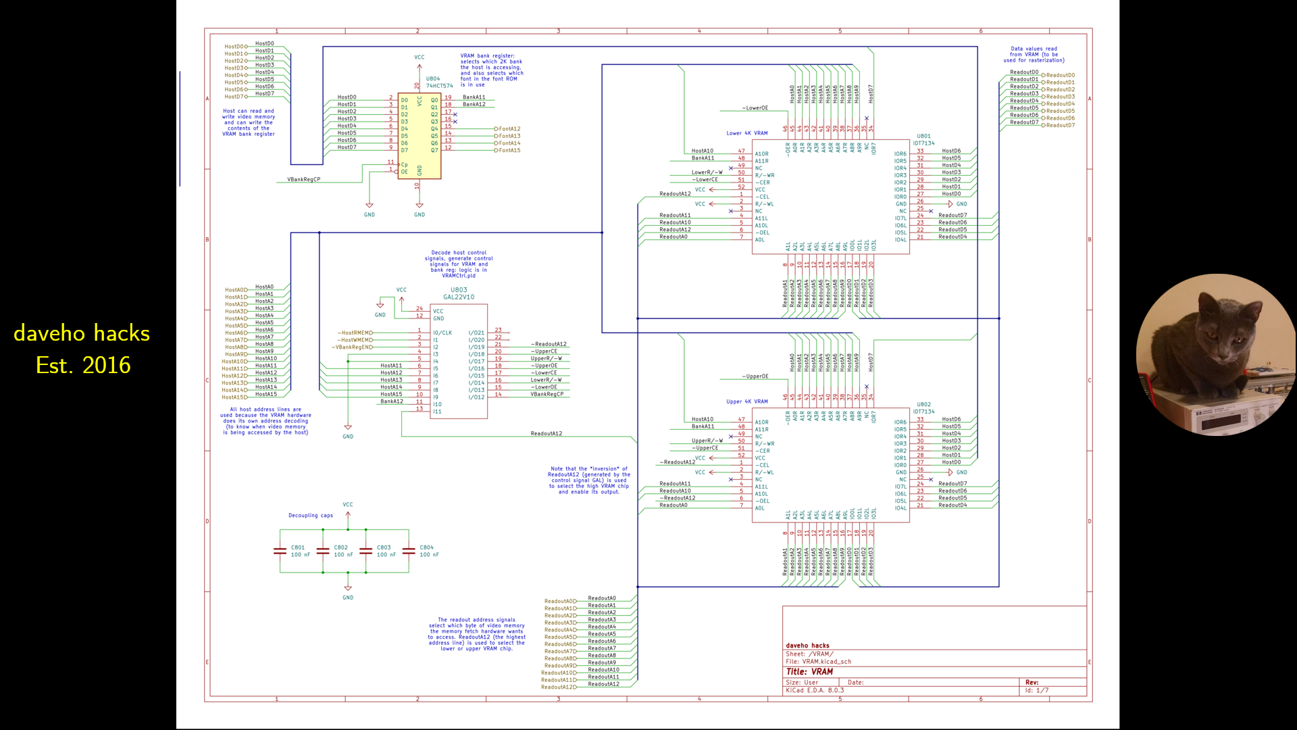
Episode02/Materials/HW_VGA_001_vram_module.png
