daveho/HW_VGA/Episode02/Materials/HW_VGA_003_idt7314_interfaces.png

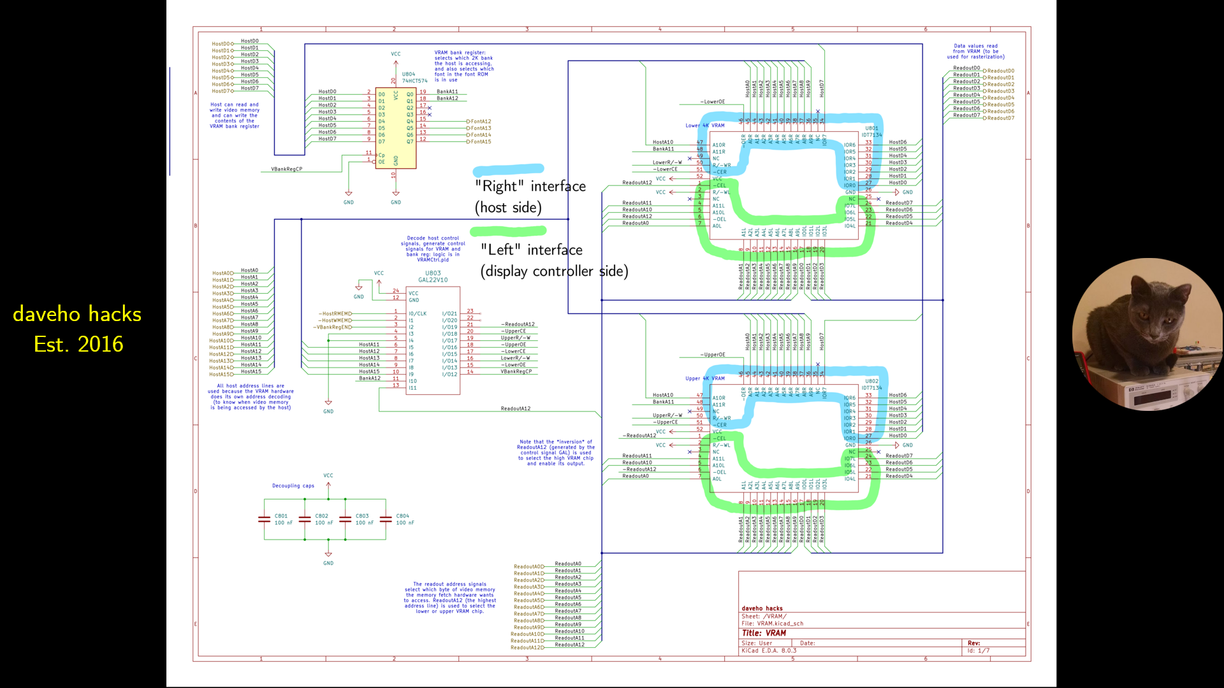
Episode02/Materials/HW_VGA_003_idt7314_interfaces.png
