daveho/HW_VGA/Episode02/Materials/HW_VGA_011_rasterizer_signals.png

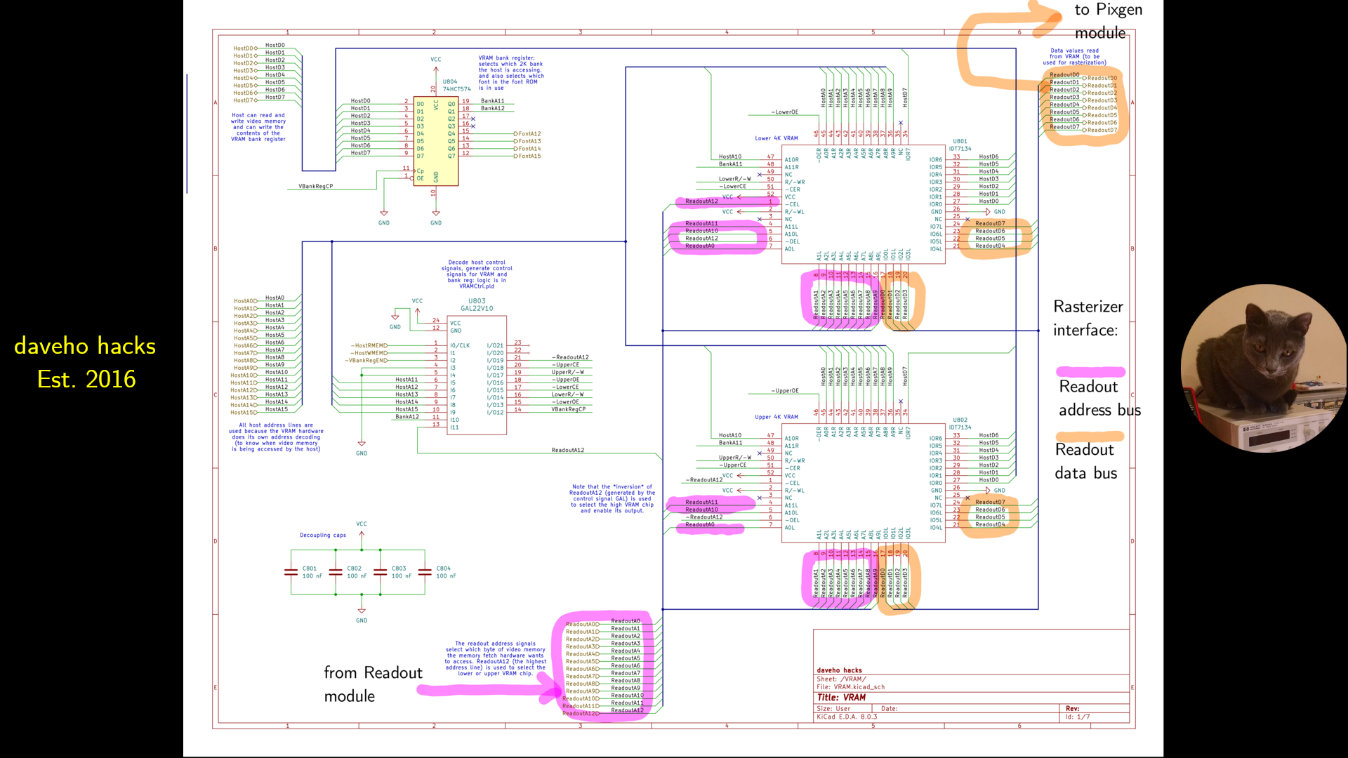
Episode02/Materials/HW_VGA_011_rasterizer_signals.png
