daveho/HW_VGA/Episode02/Materials/HW_VGA_012_internal_signals.png

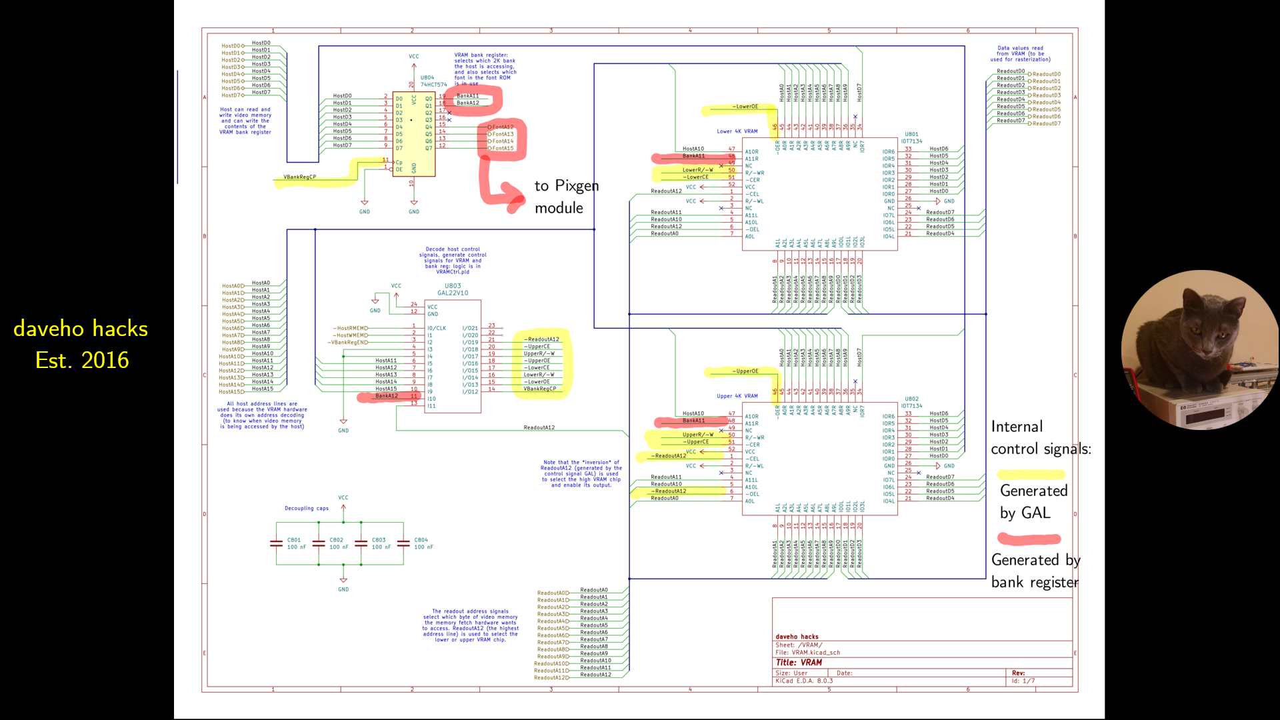
Episode02/Materials/HW_VGA_012_internal_signals.png
