daveho/HW_VGA/Episode02/Materials/HW_VGA_013_vram_window.png

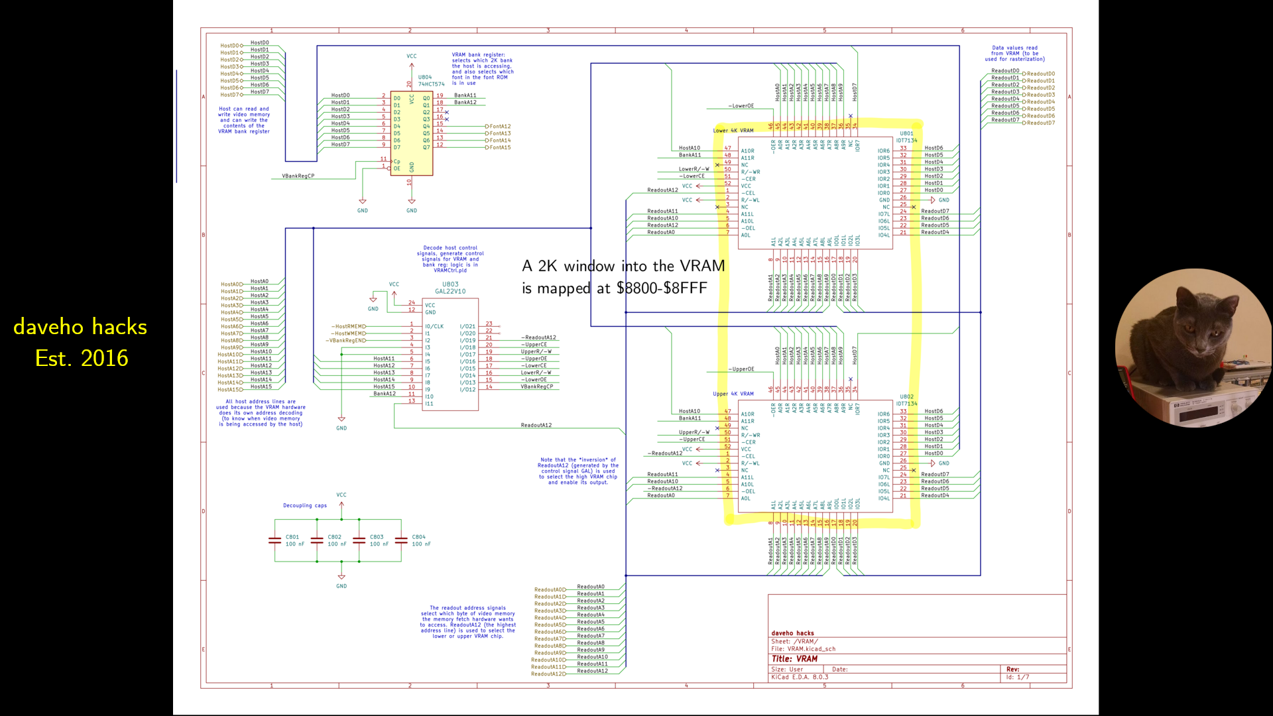
Episode02/Materials/HW_VGA_013_vram_window.png
