daveho/HW_VGA/Episode02/Materials/HW_VGA_019_readout_a12.png

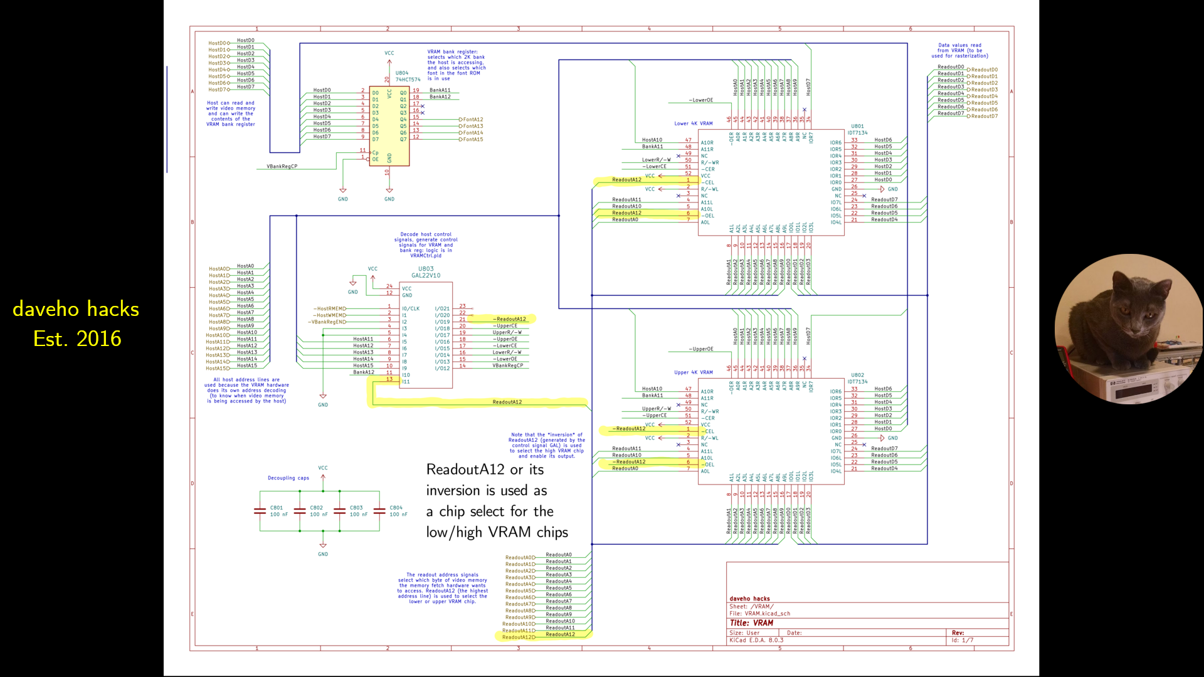
Episode02/Materials/HW_VGA_019_readout_a12.png
