daveho/HW_VGA/Episode02/Materials/ingo_e3615a.jpg

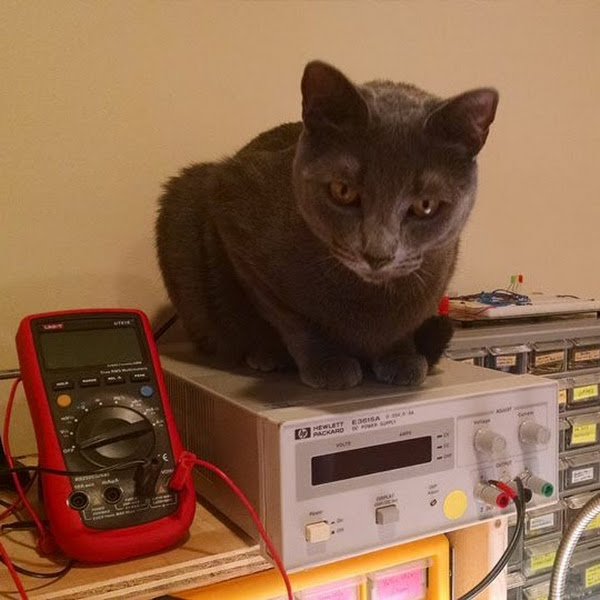
Episode02/Materials/ingo_e3615a.jpg
