daveho/HW_VGA/Episode04/Materials/vram_bg.png

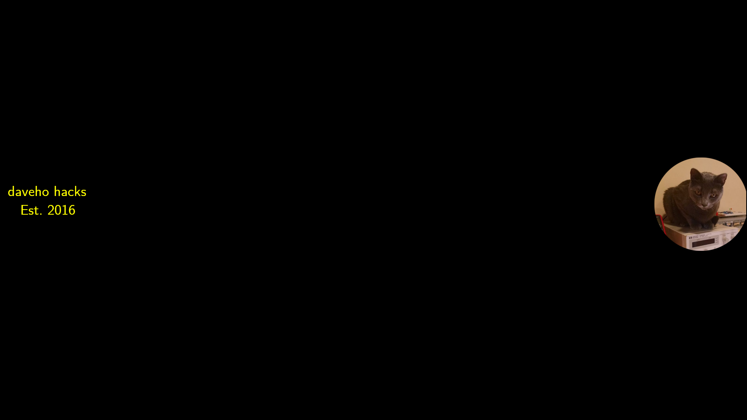
Episode04/Materials/vram_bg.png
