daveho/HW_VGA/Episode04/Materials/schematic-050.pdf

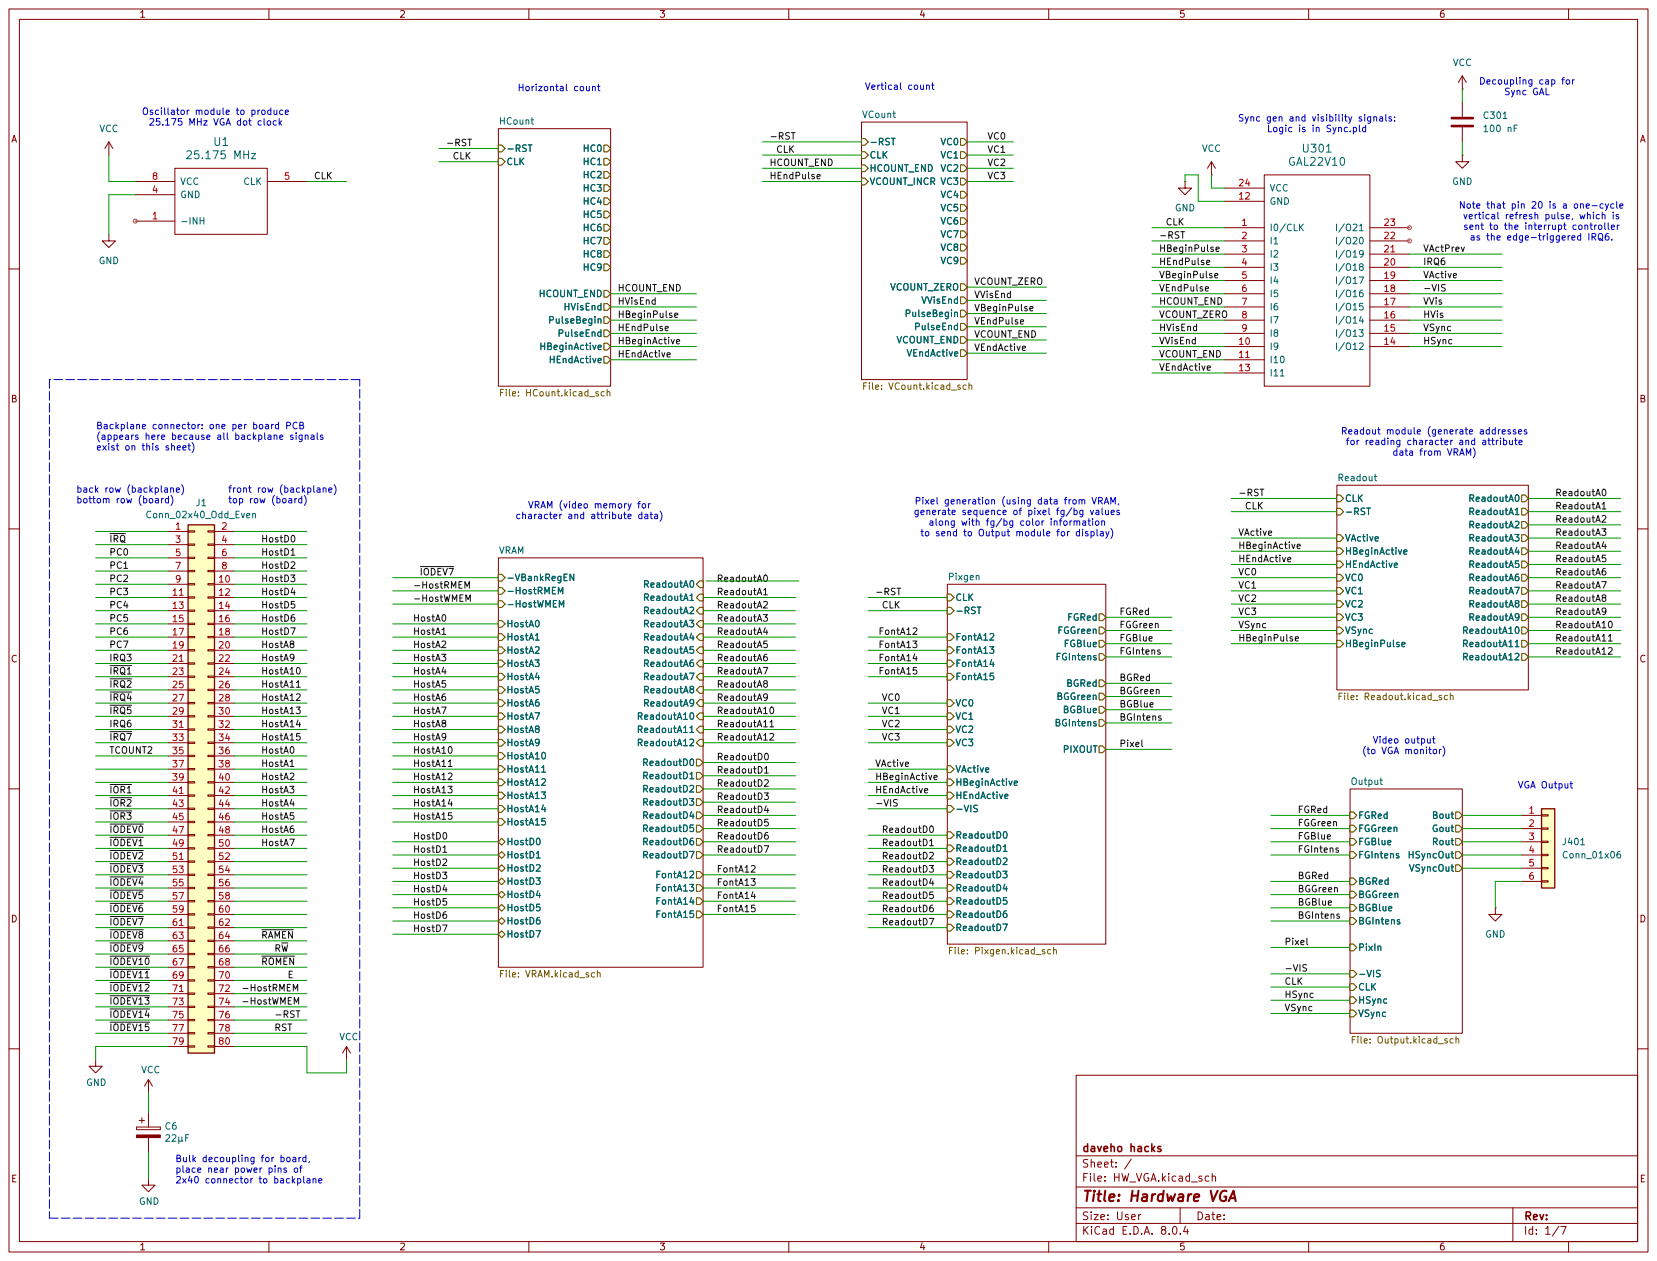
[picture p139: page 1]

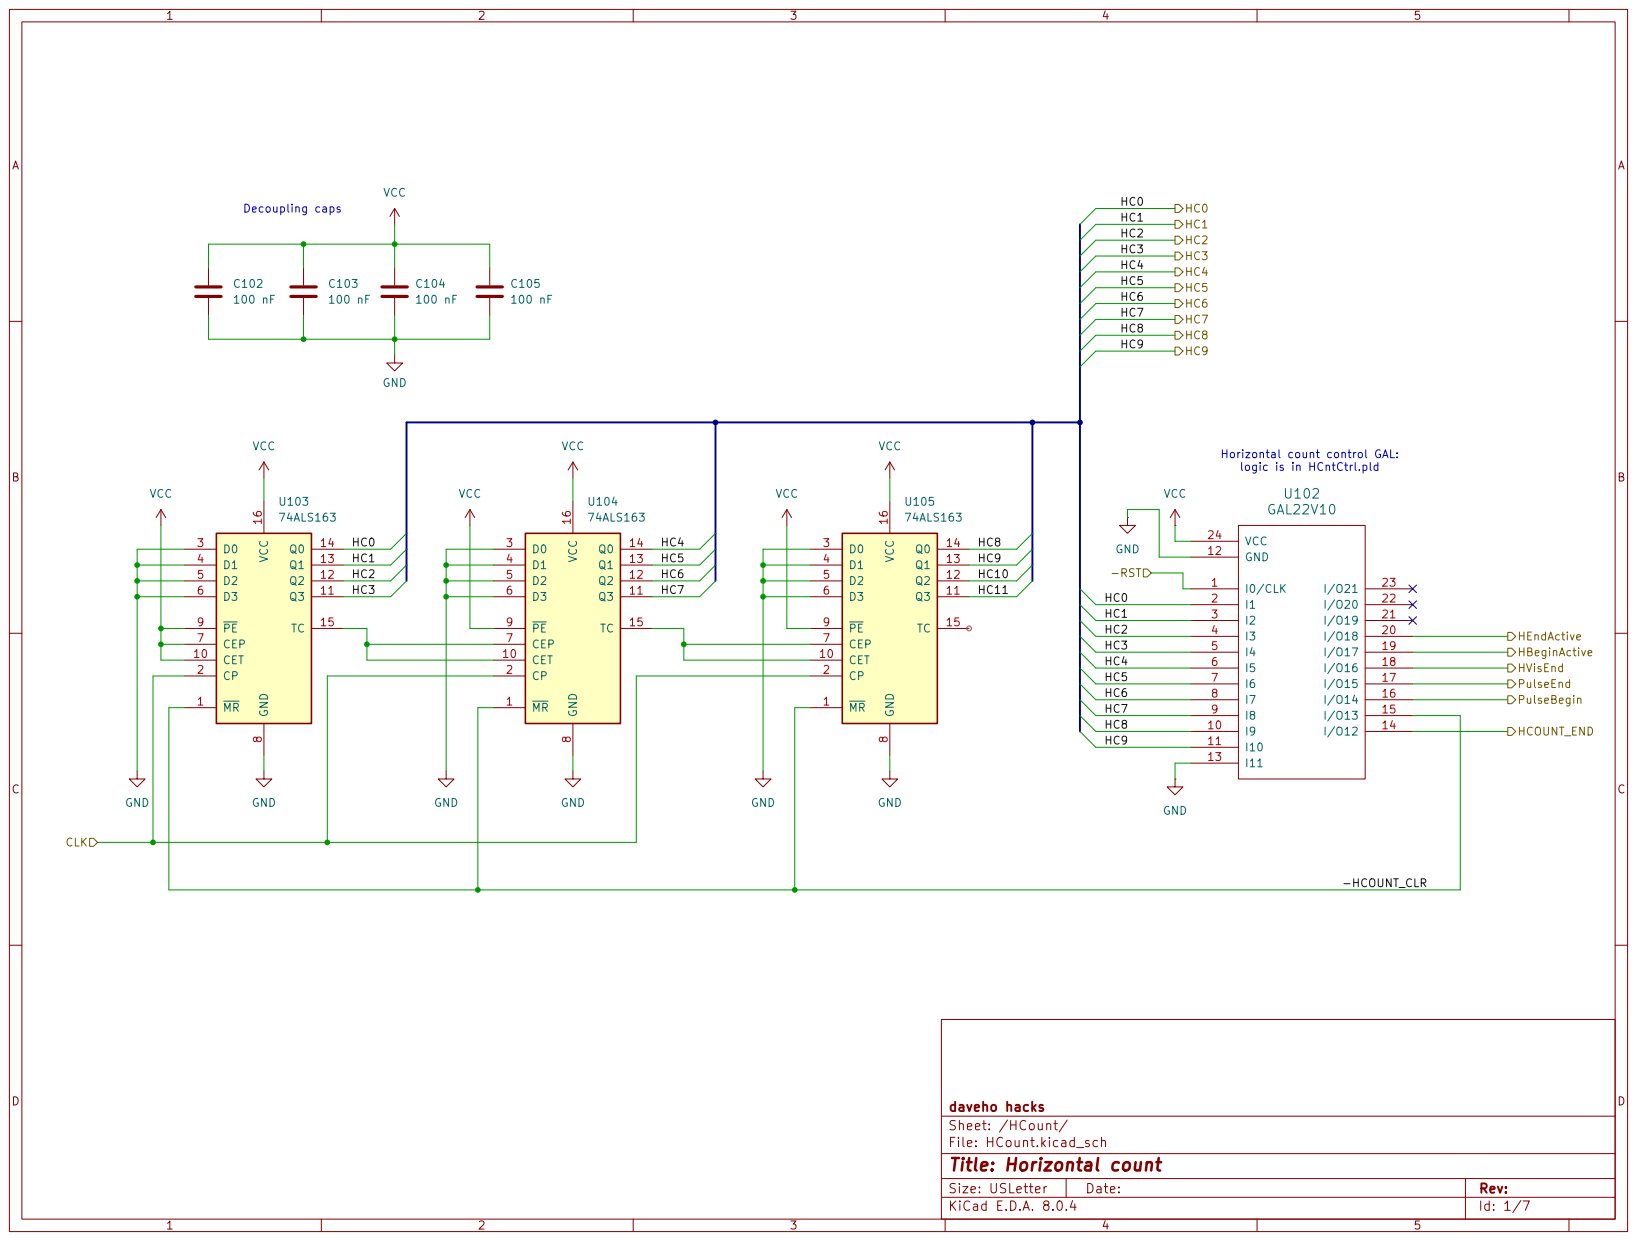
[picture p140: page 2]


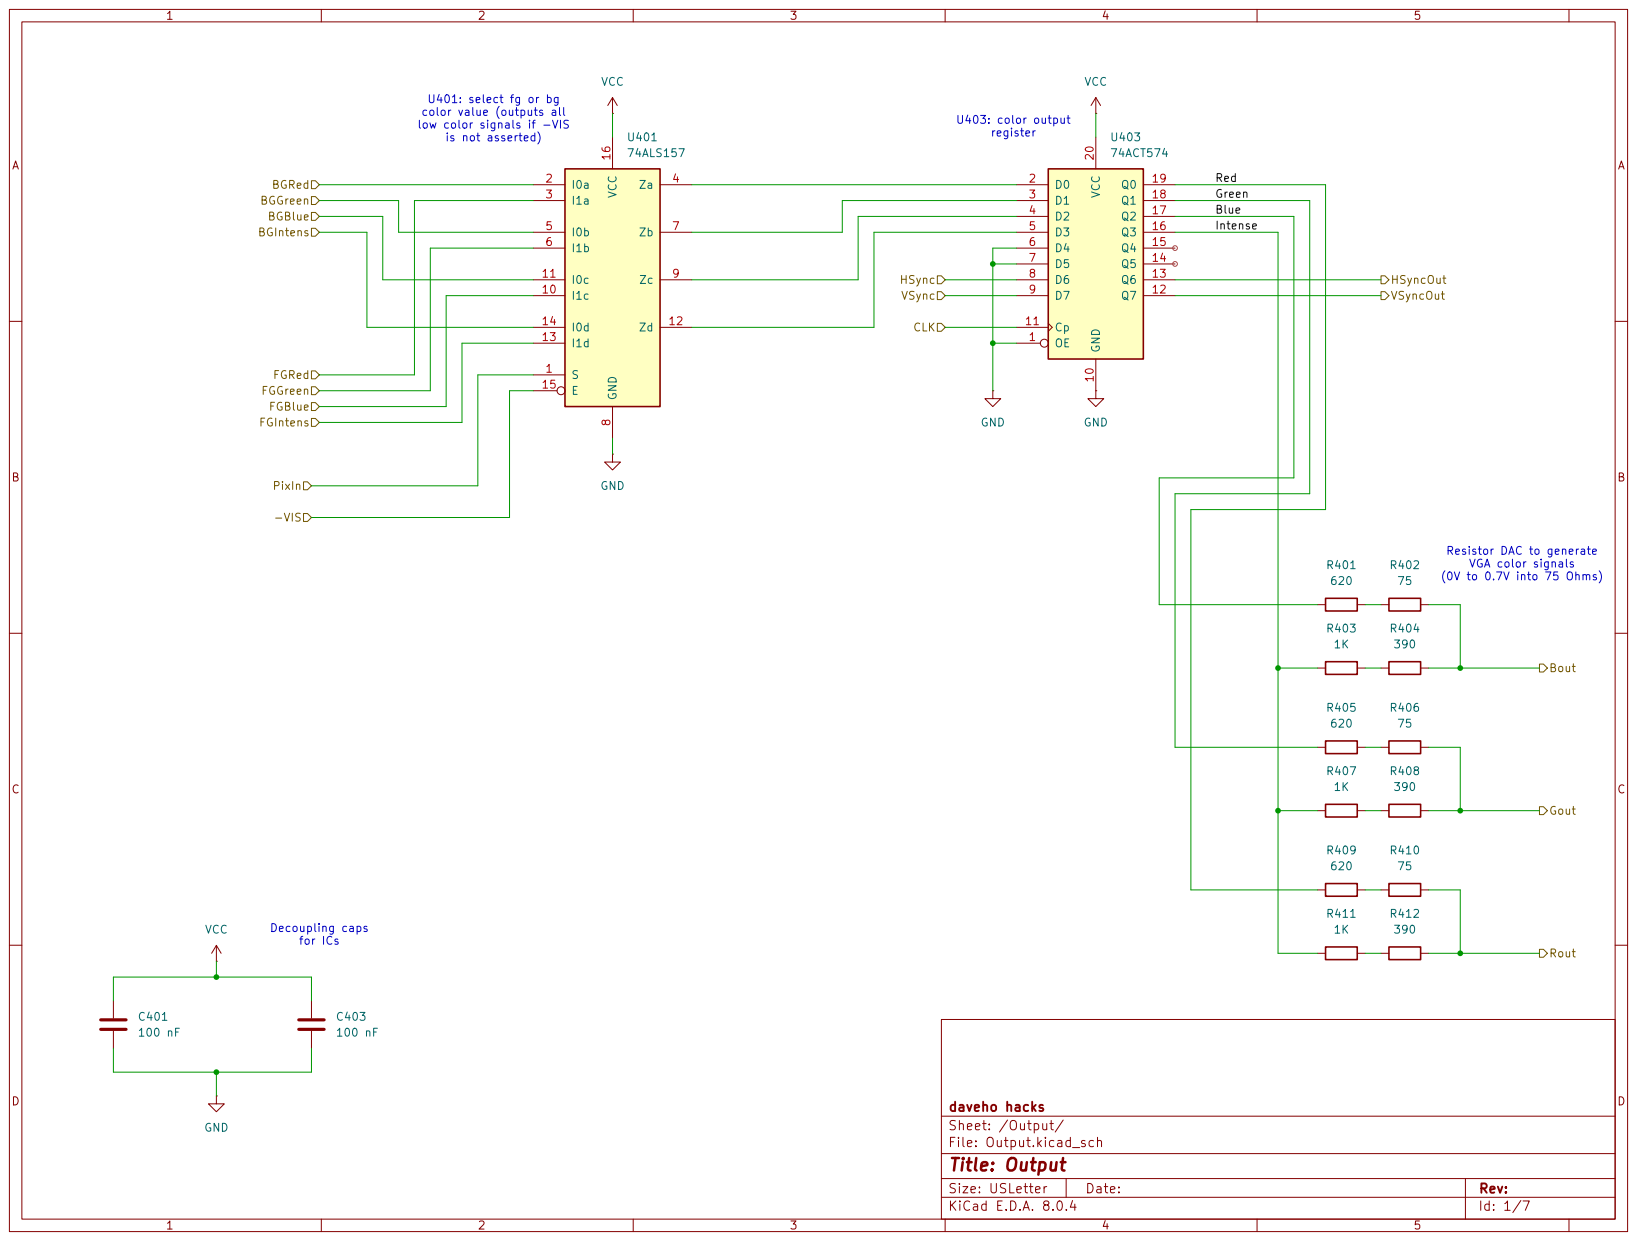
[picture p141: page 4]

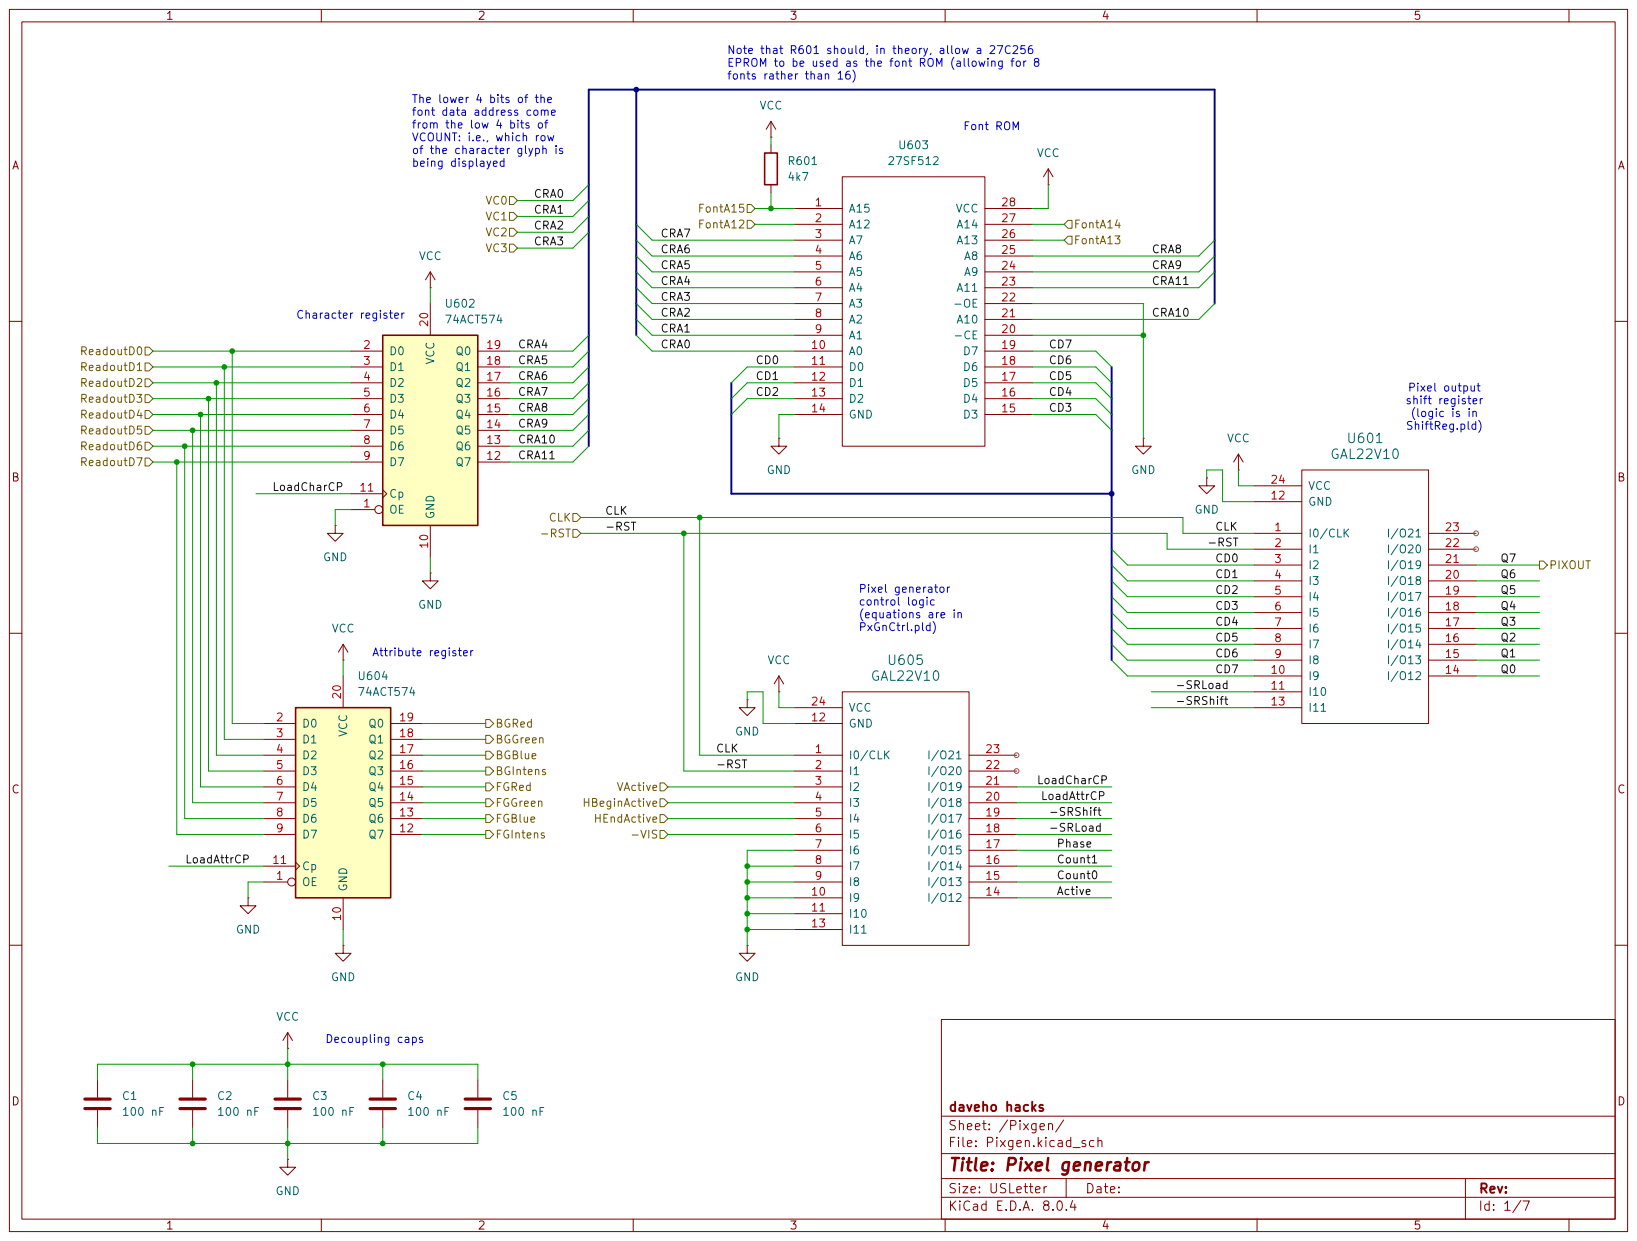
[picture p142: page 5]


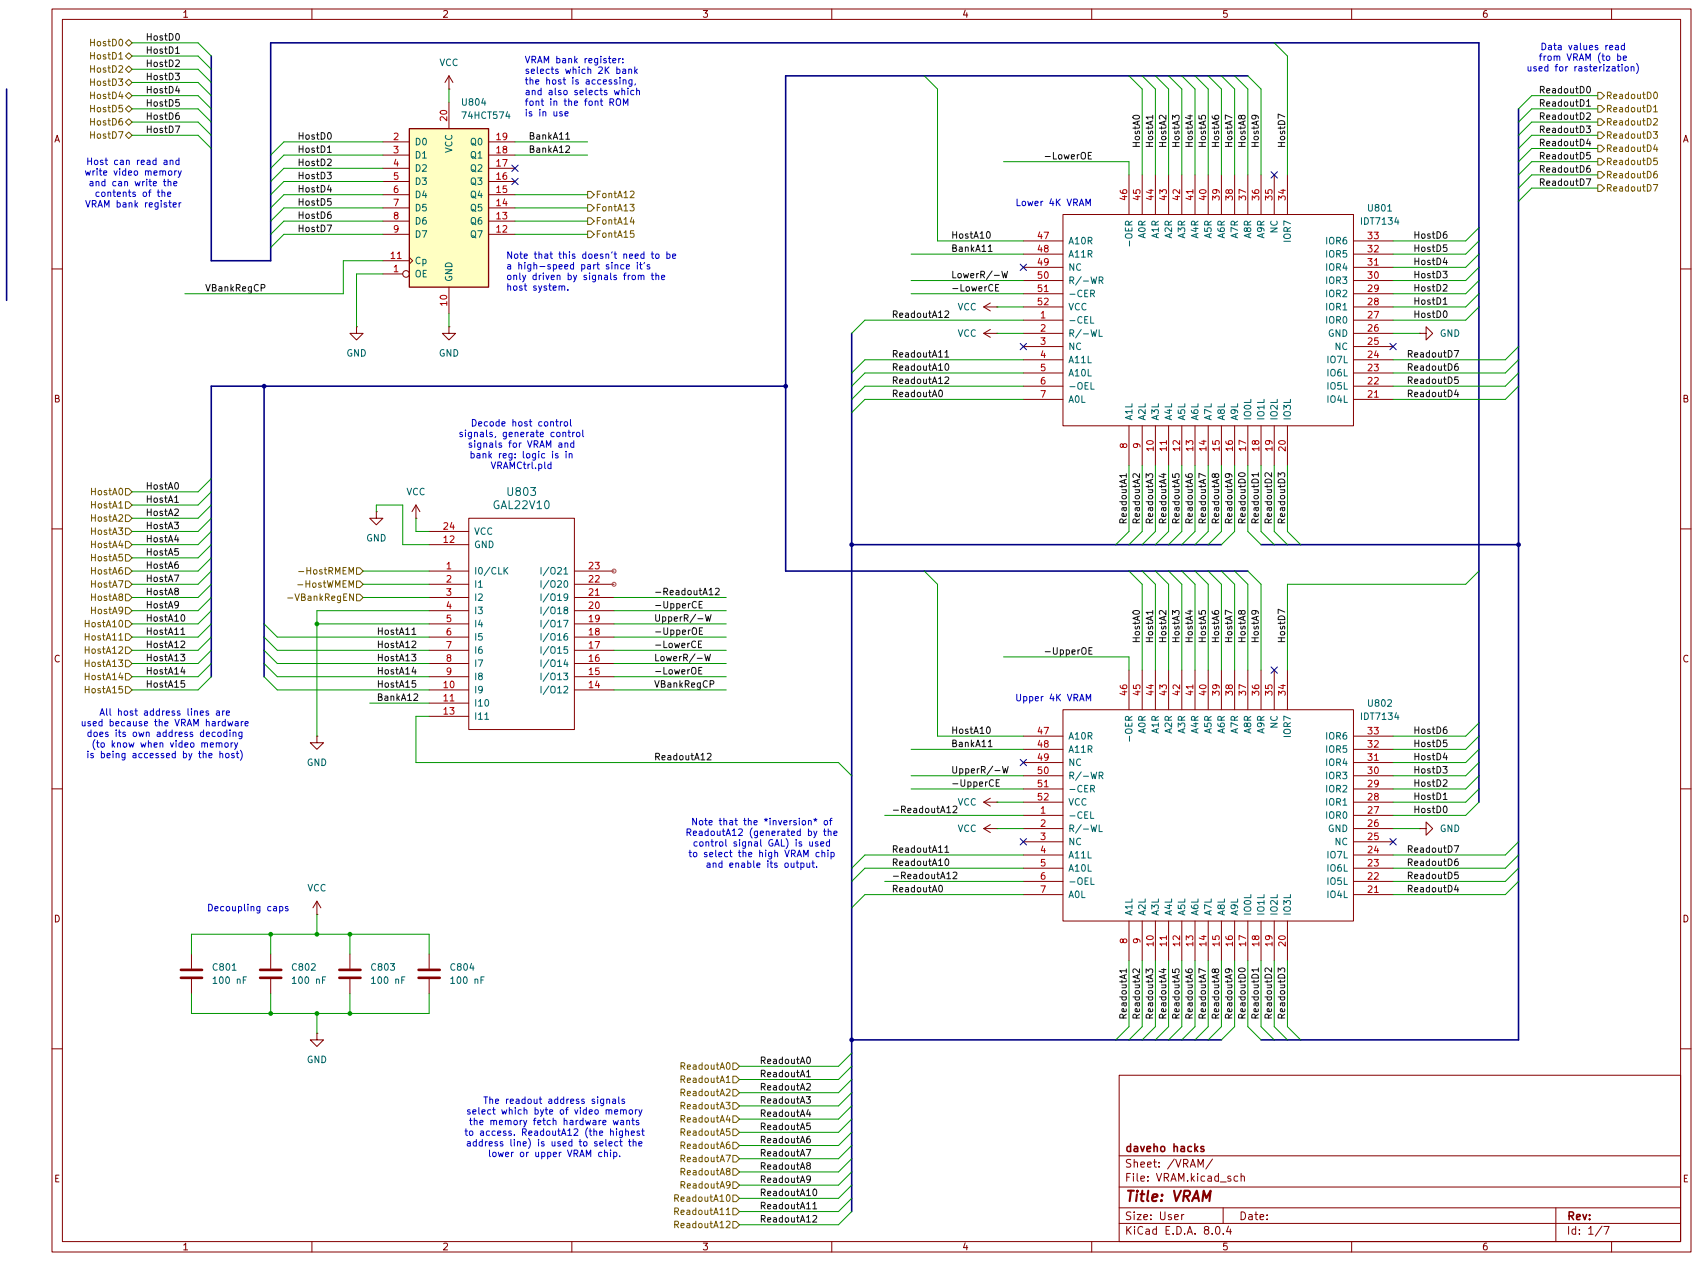
[picture p143: page 7]
