daveho/HW_VGA/Episode04/Materials/schematic-051.pdf

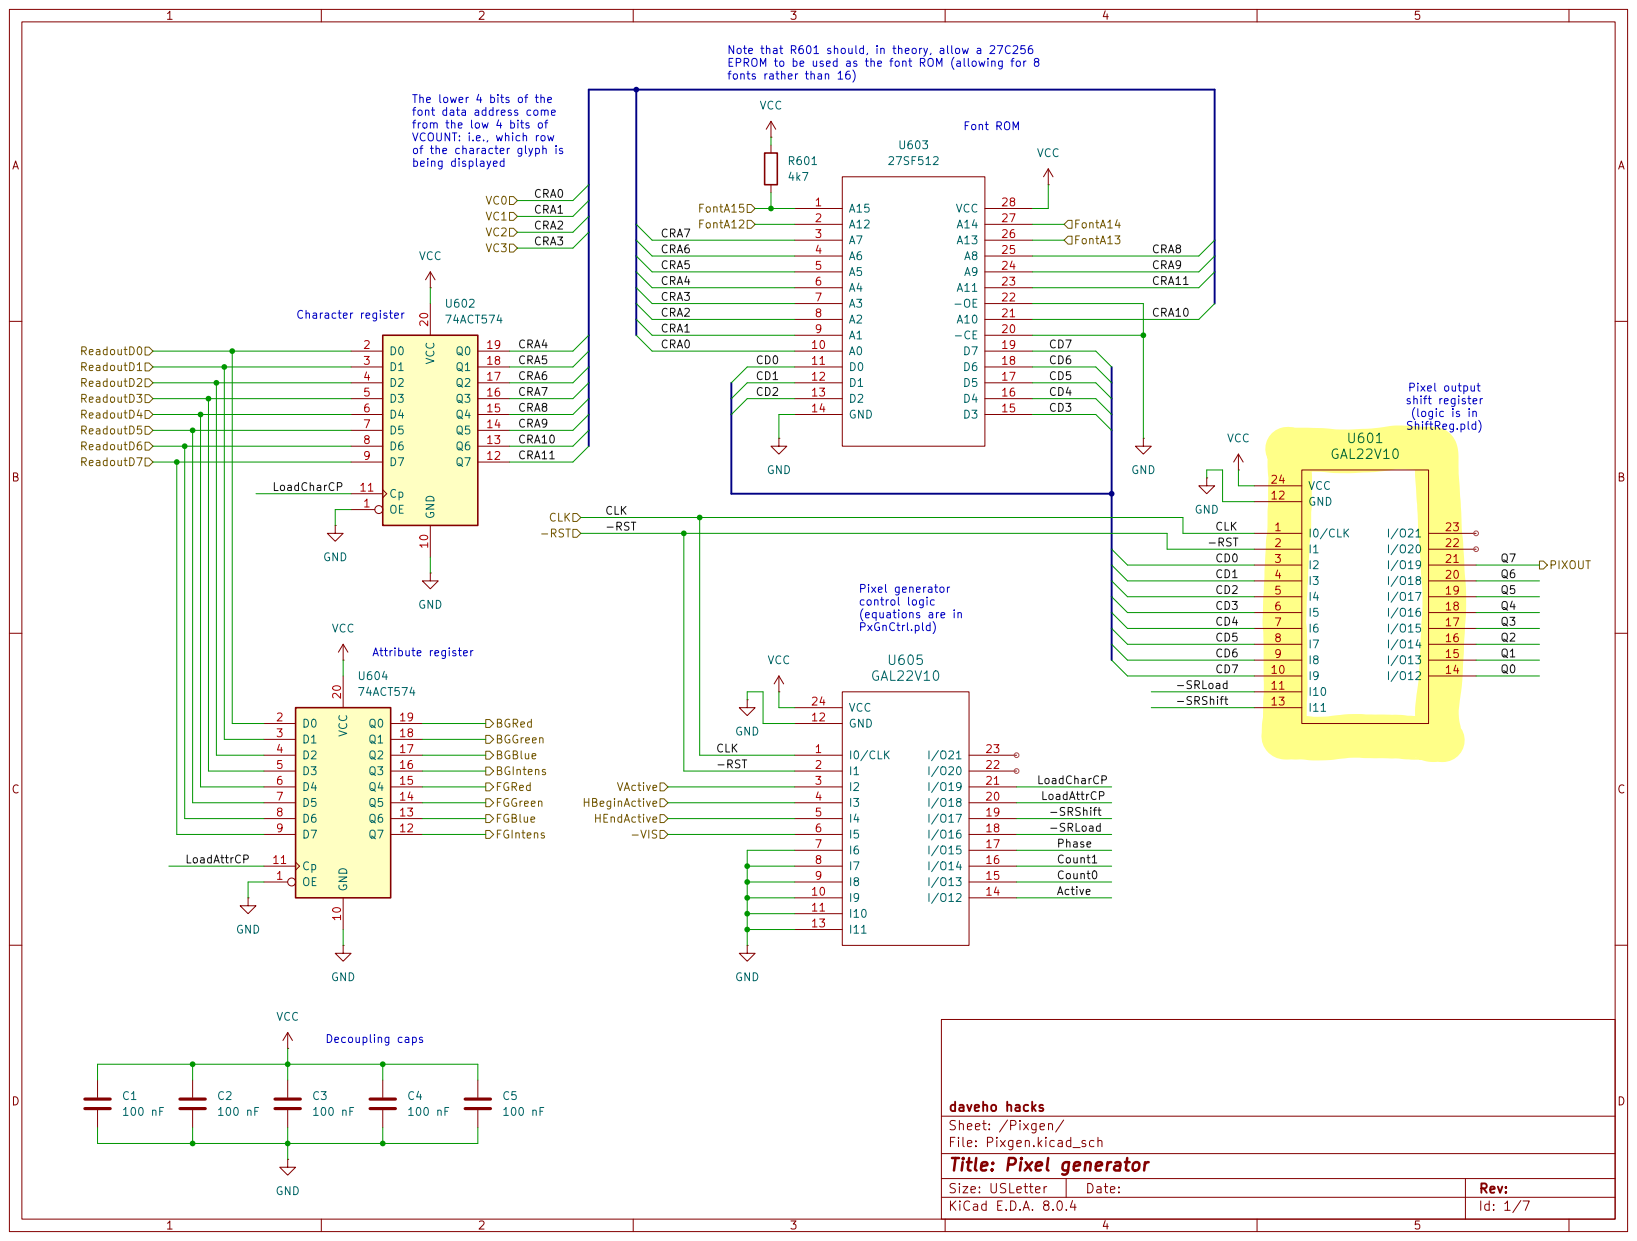
[picture p144: page 5]
