daveho/HW_VGA/Episode04/Materials/schematic-052.pdf

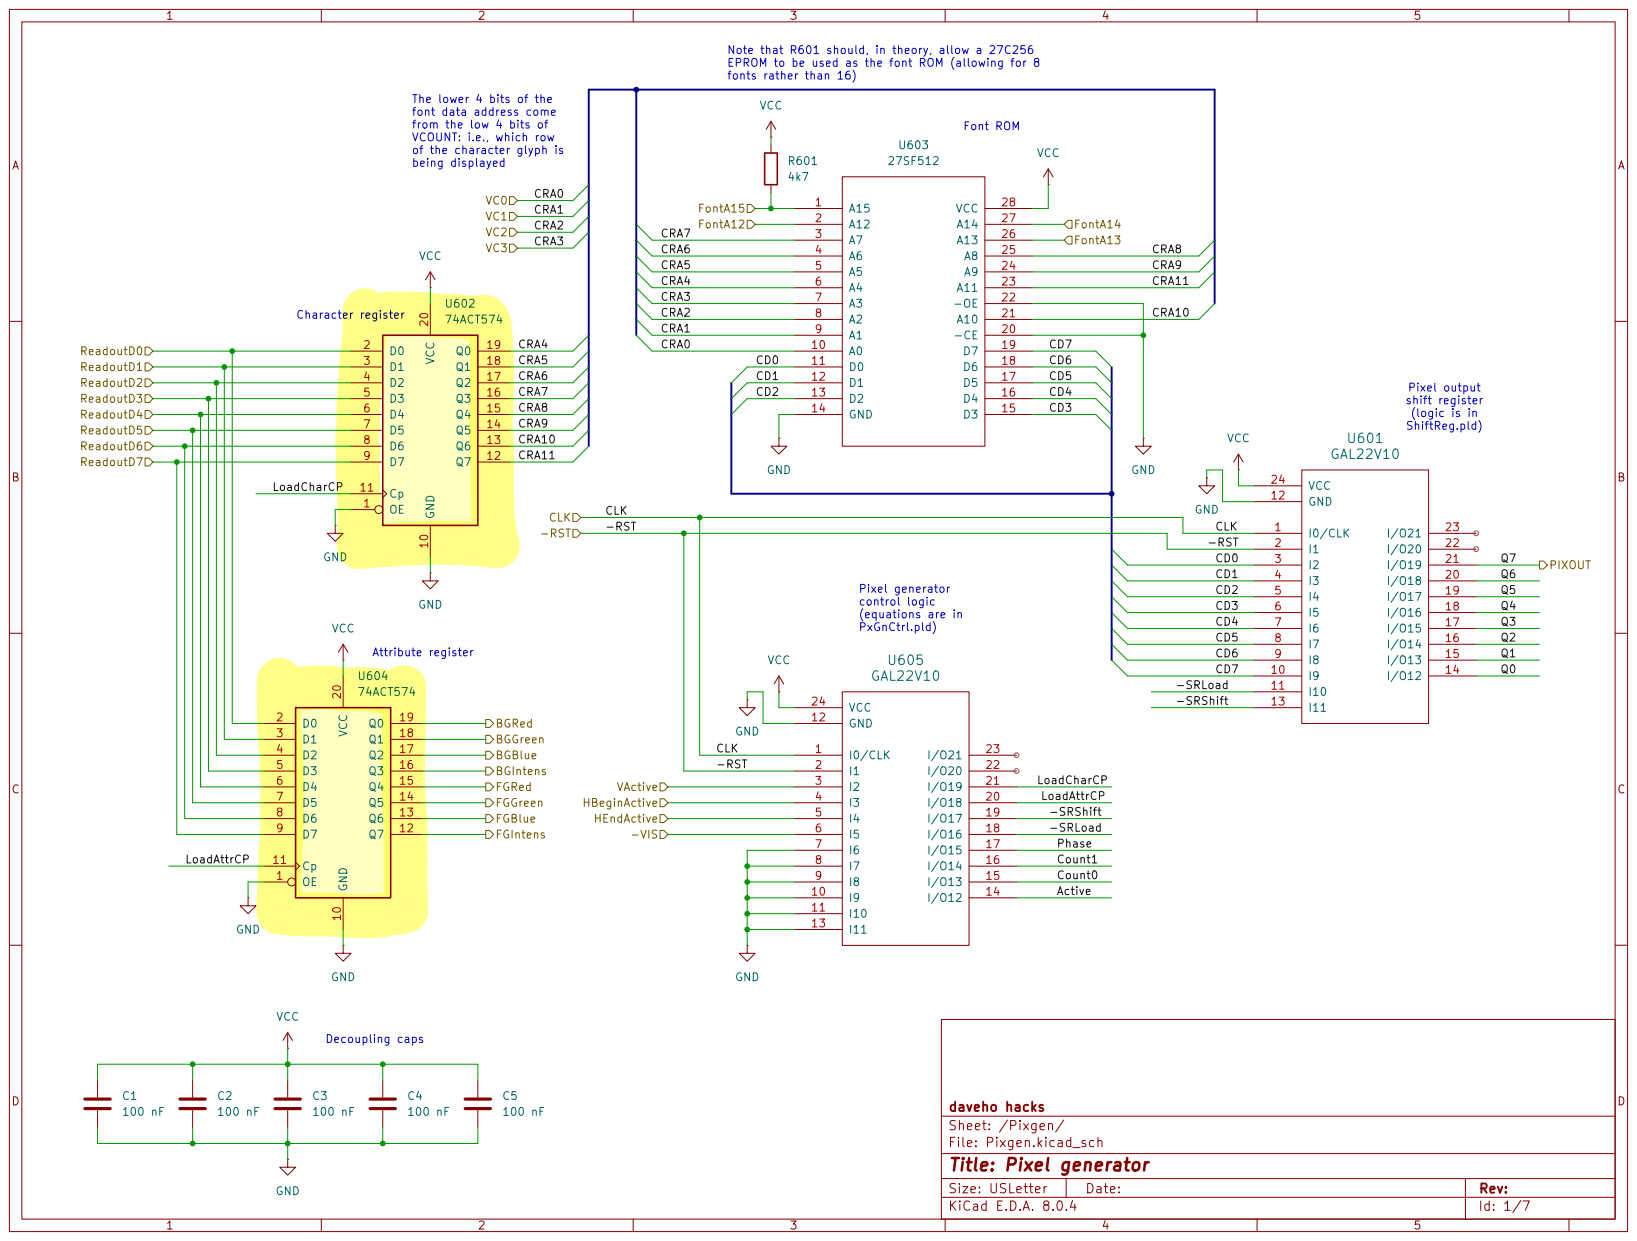
[picture p145: page 5]
