daveho/HW_VGA/Episode04/Materials/schematic-053.pdf

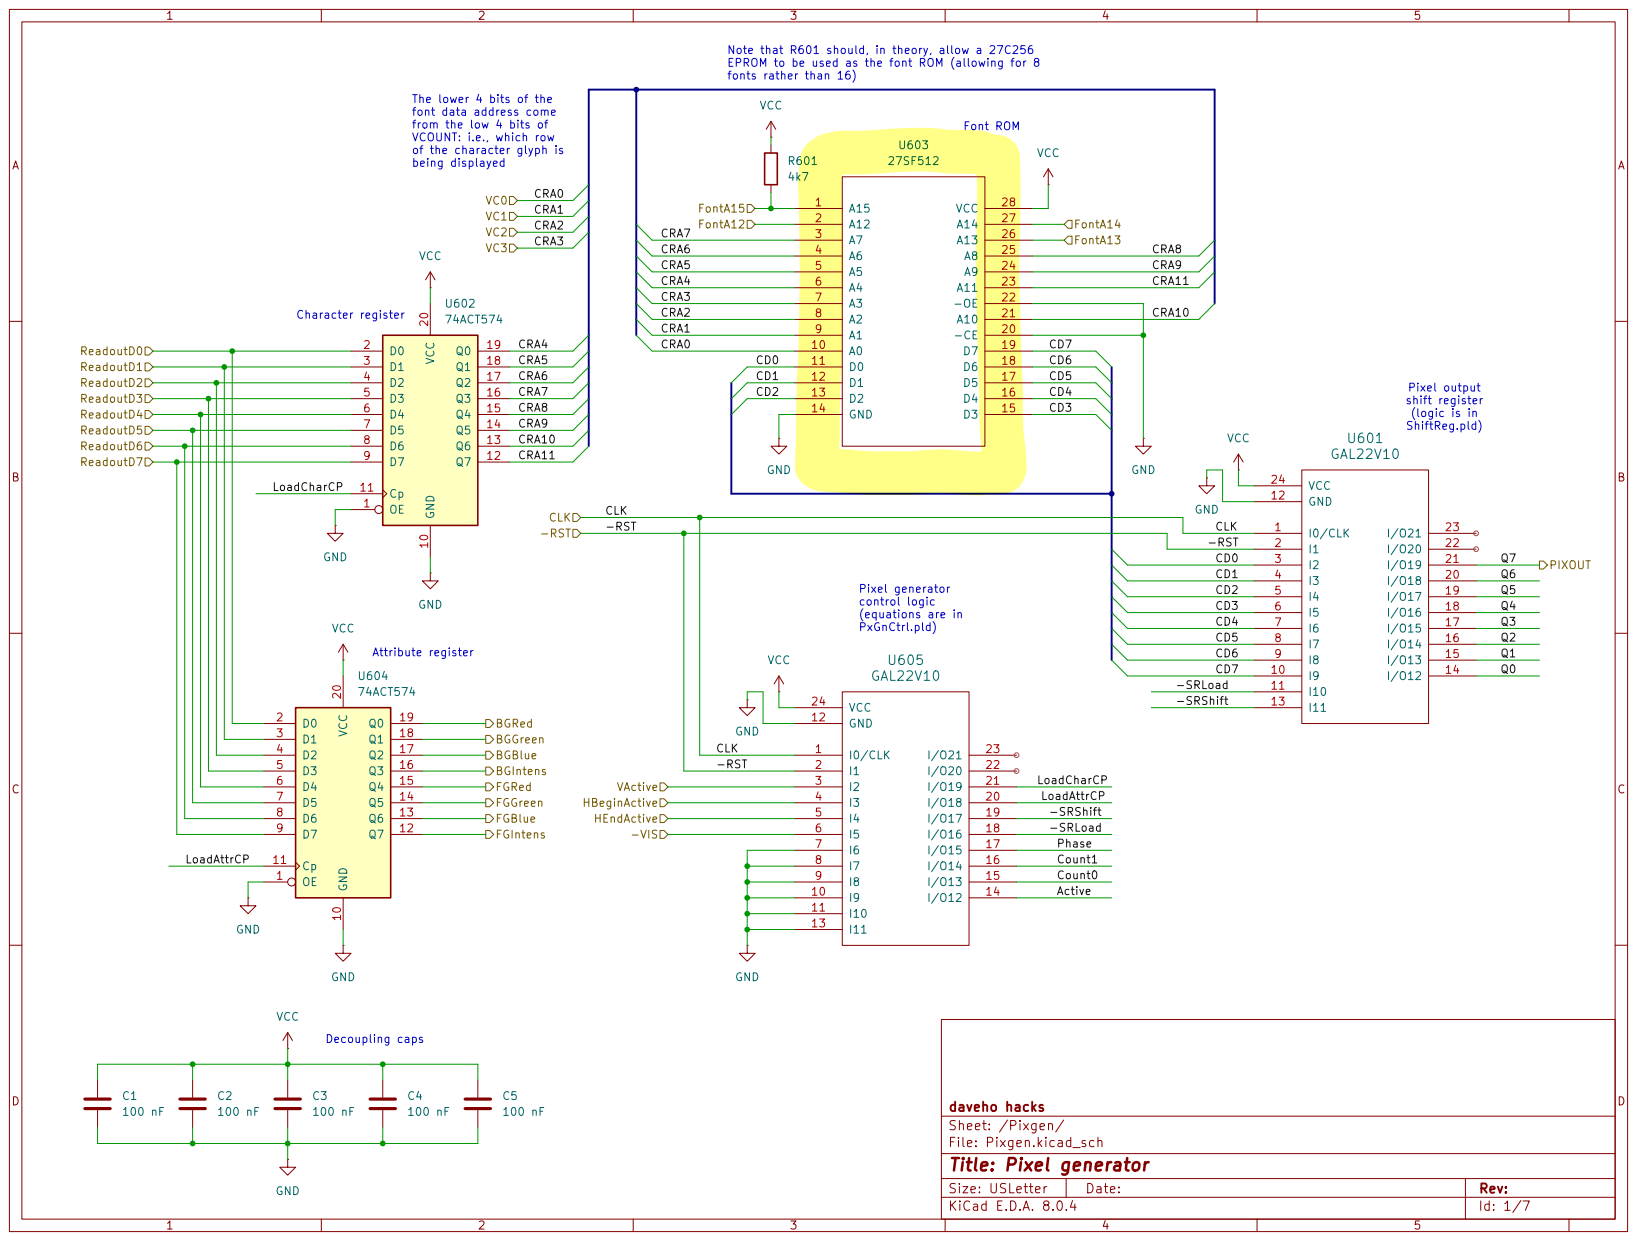
[picture p146: page 5]
