daveho/HW_VGA/Episode04/Materials/schematic-054.pdf

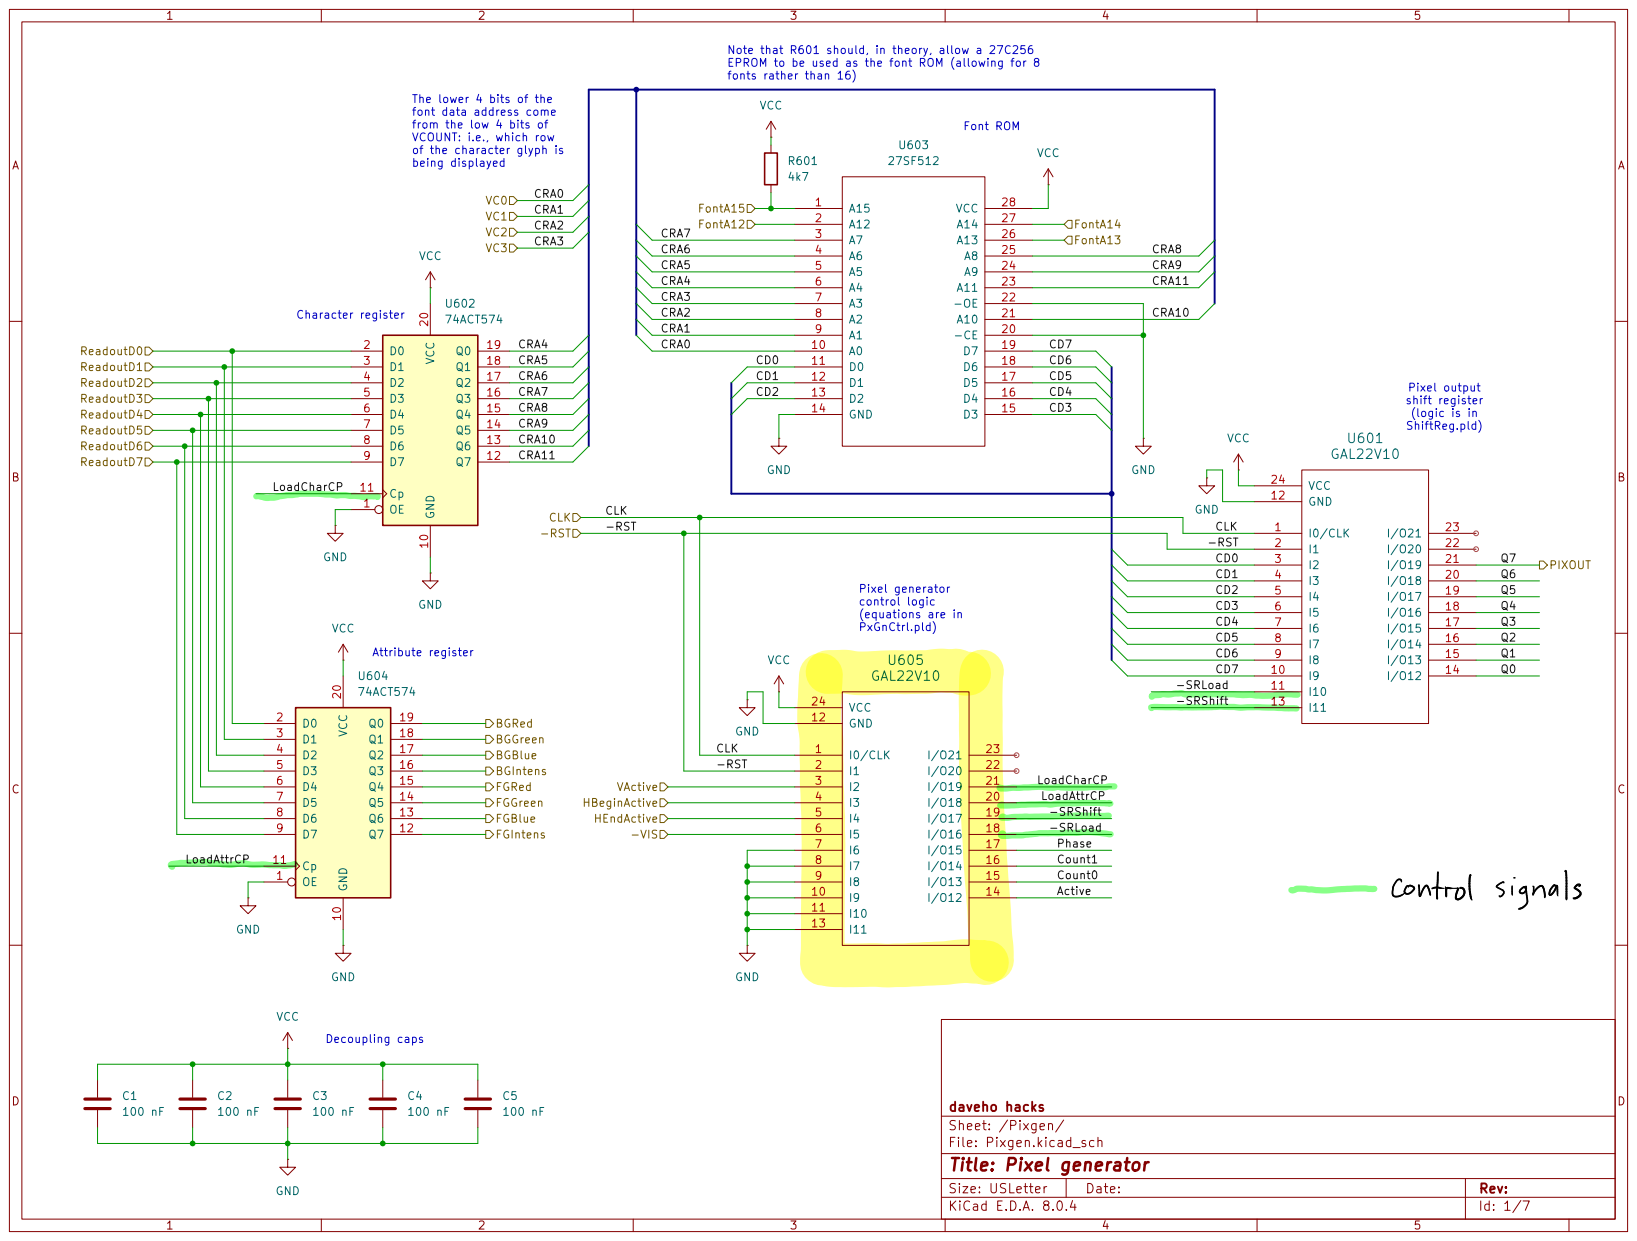
[picture p147: page 5]
