daveho/HW_VGA/Episode04/Materials/schematic-055.pdf

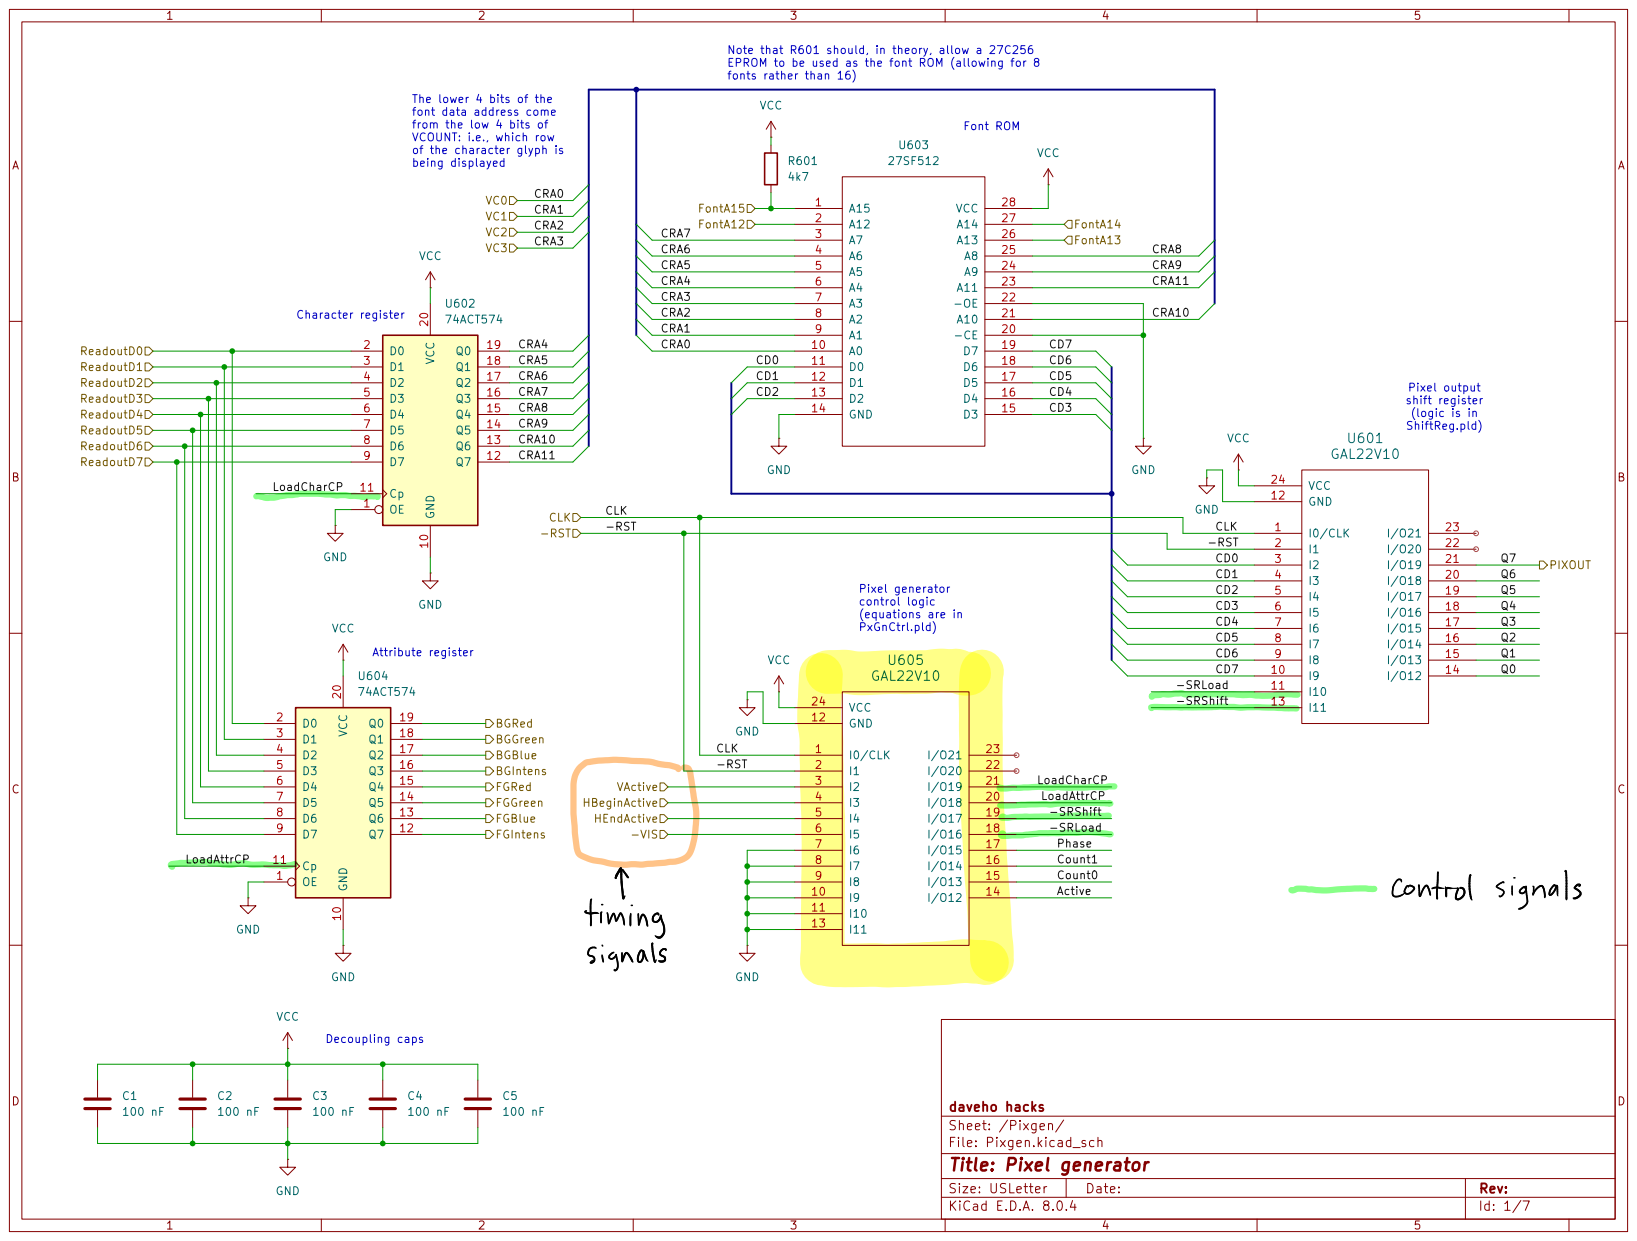
[picture p148: page 5]
