daveho/HW_VGA/Episode03/Materials/schematic_01.pdf

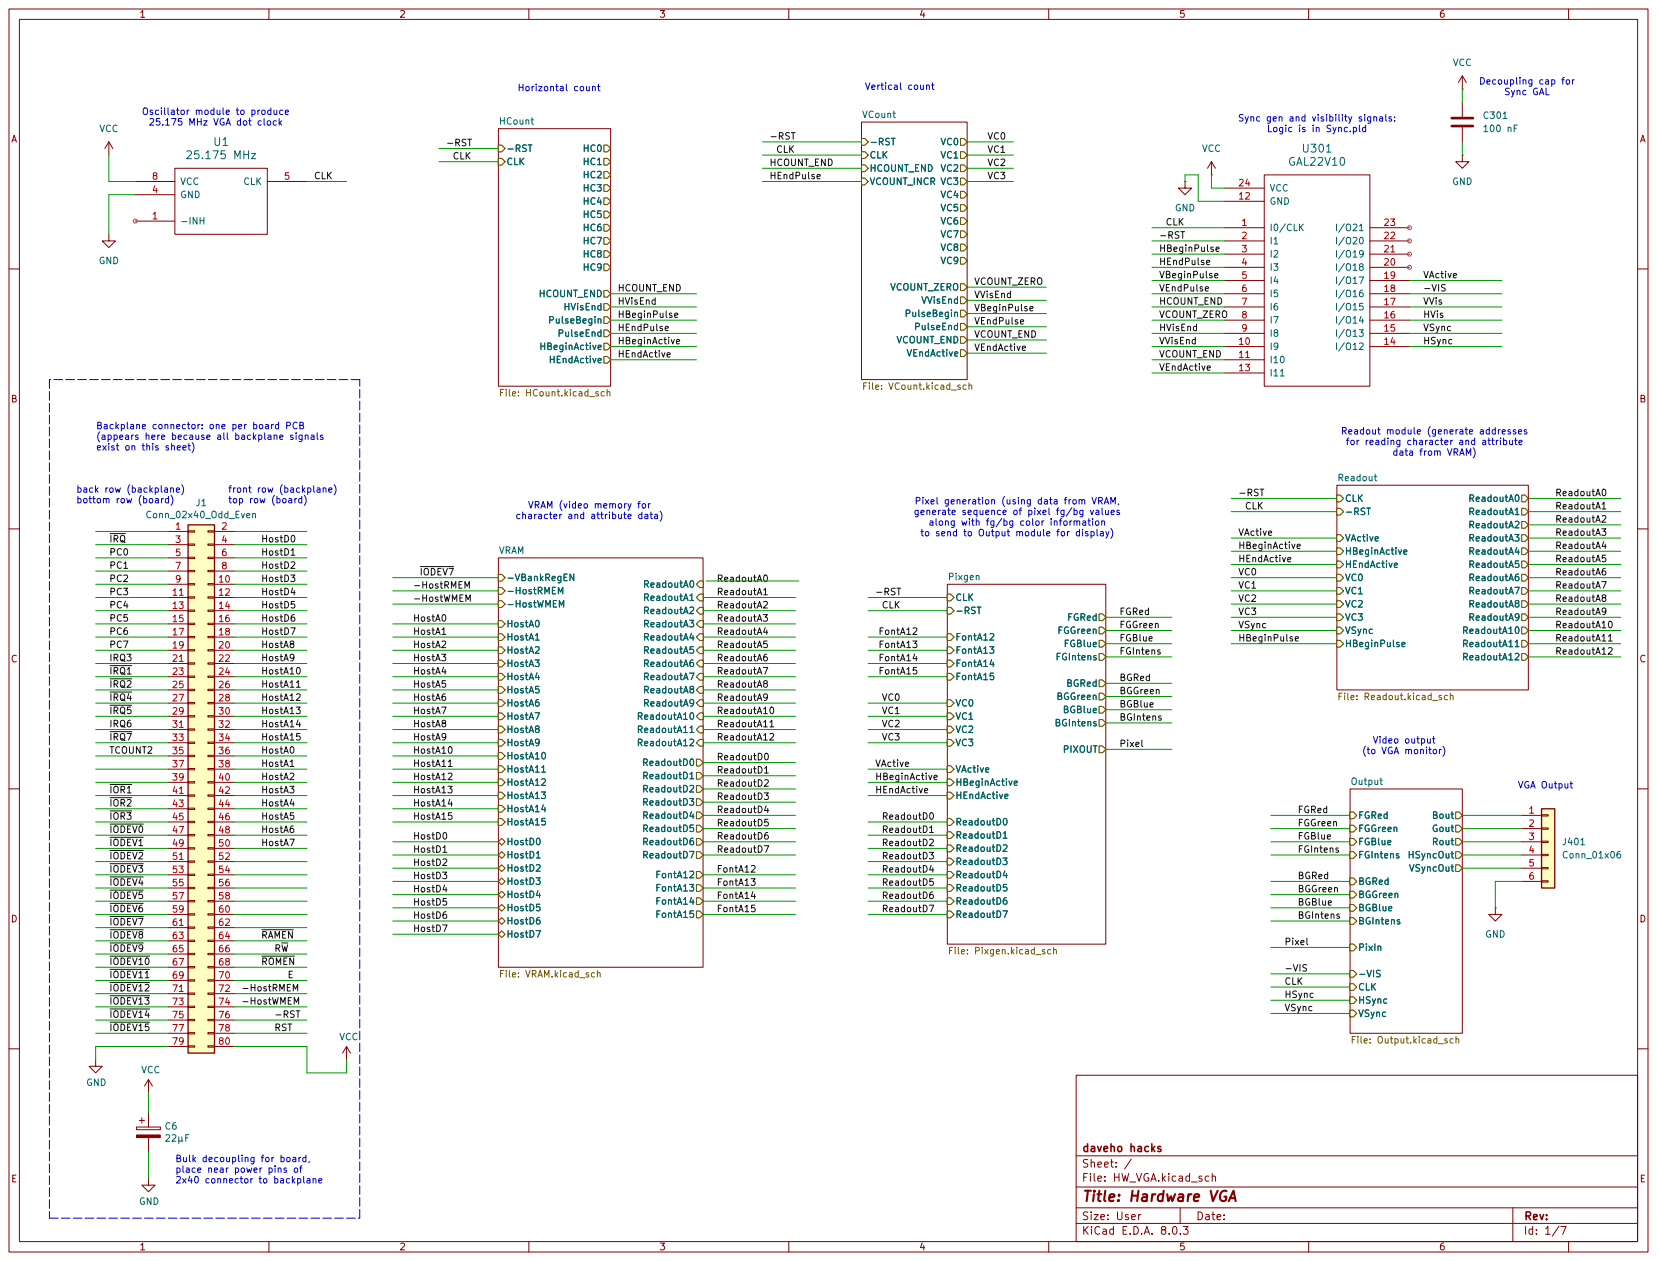
[picture p149: page 1]

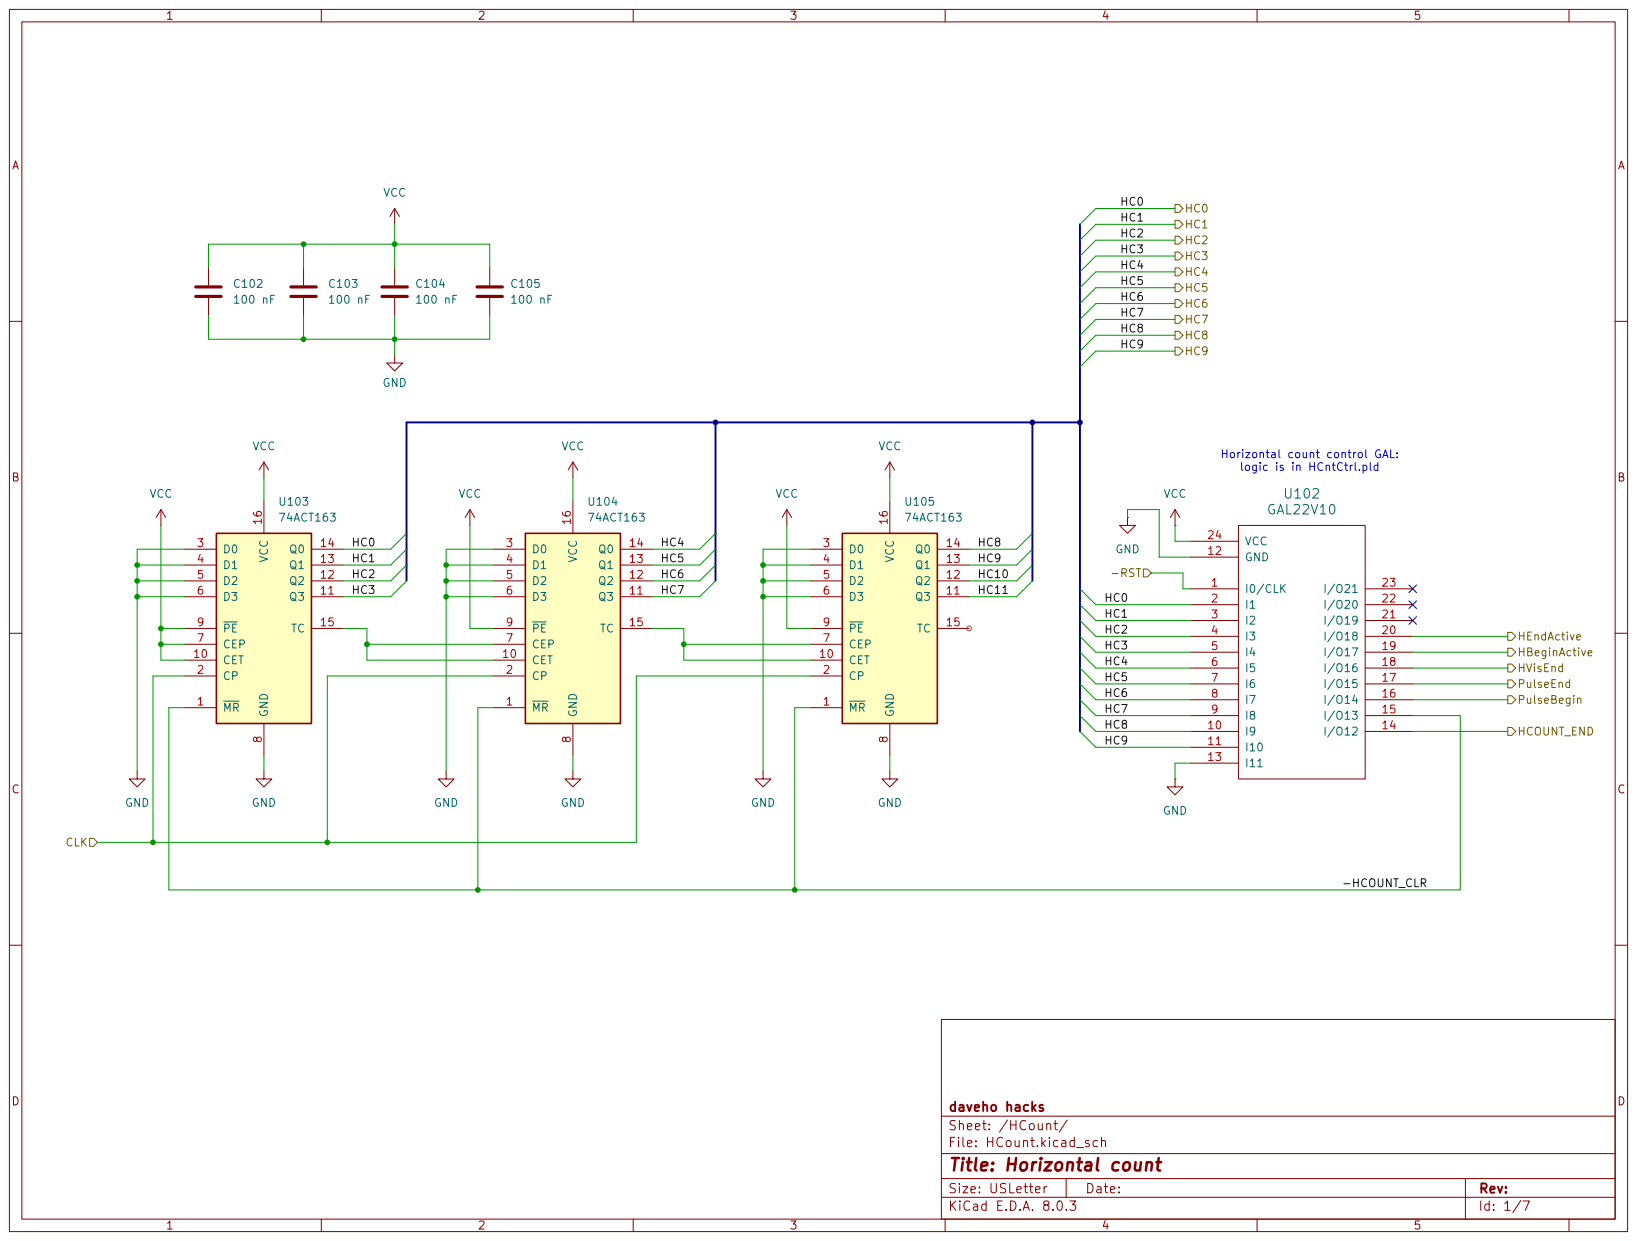
[picture p150: page 2]

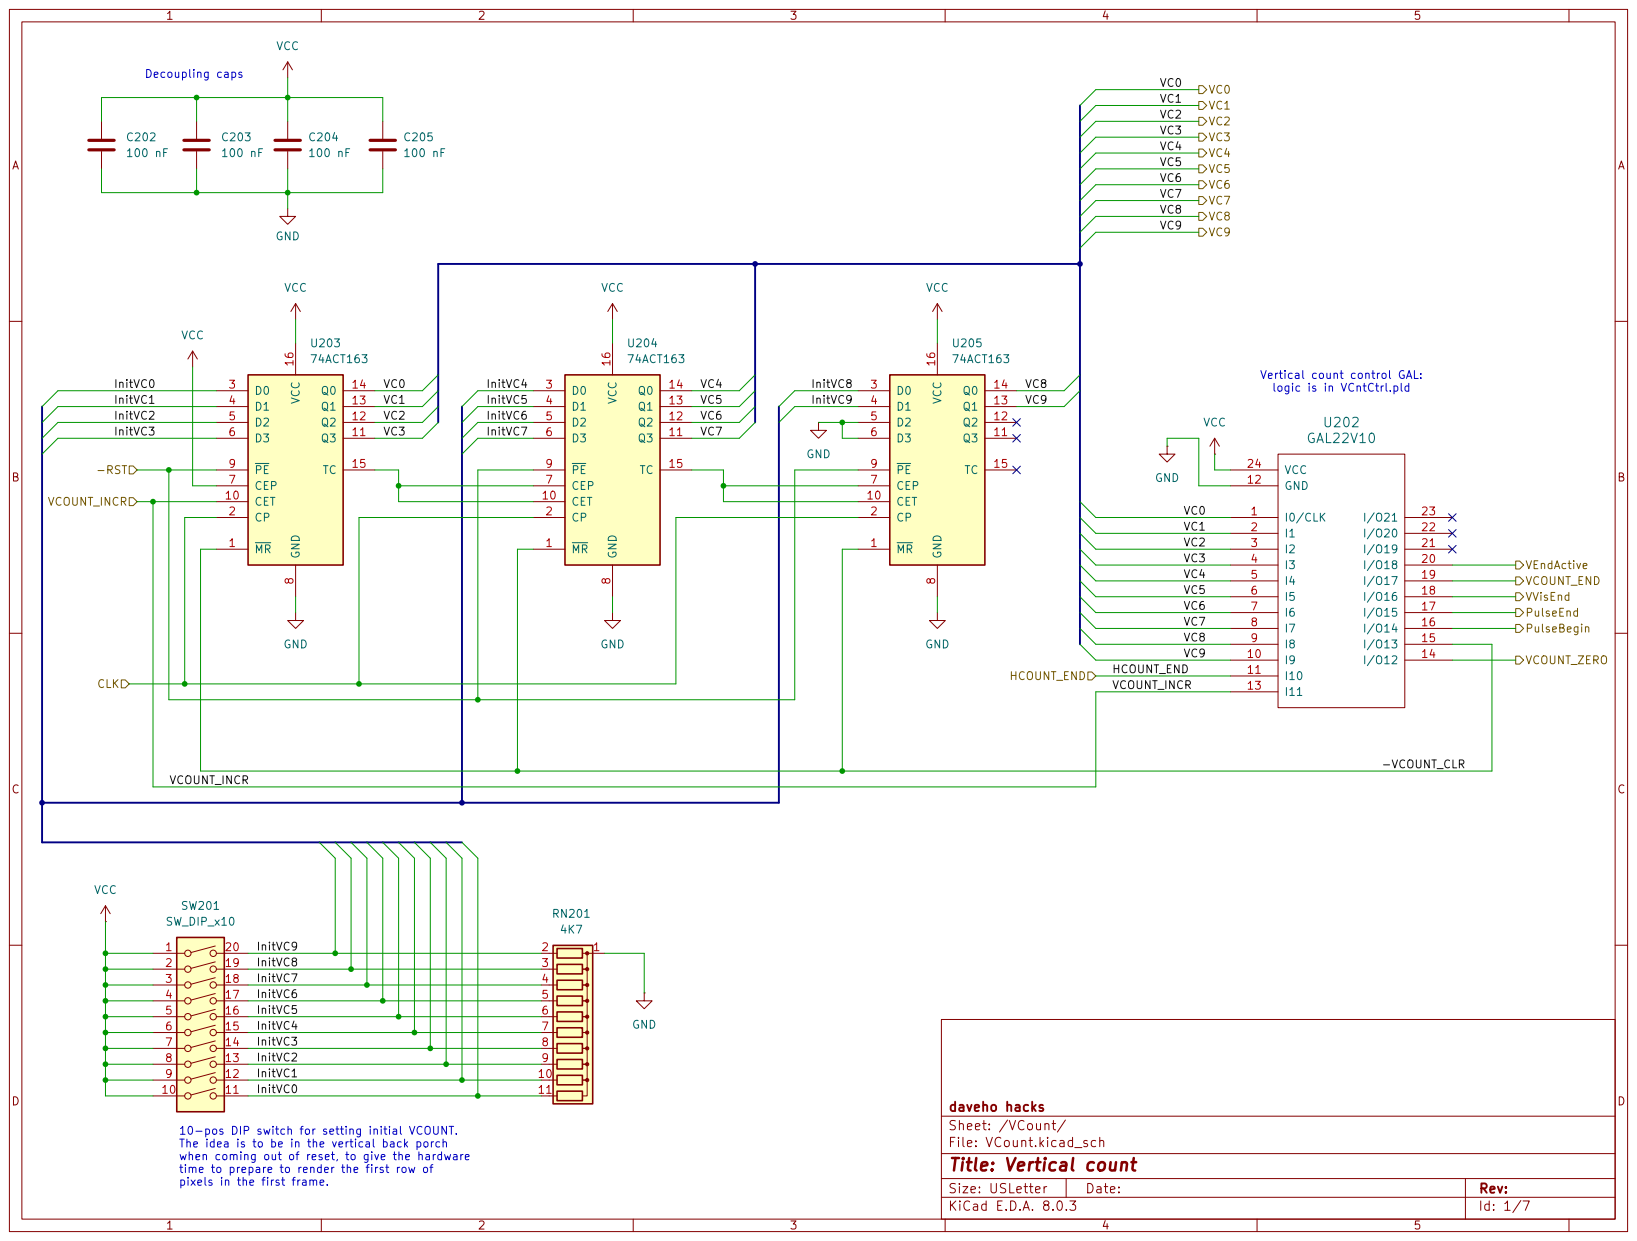
[picture p151: page 3]

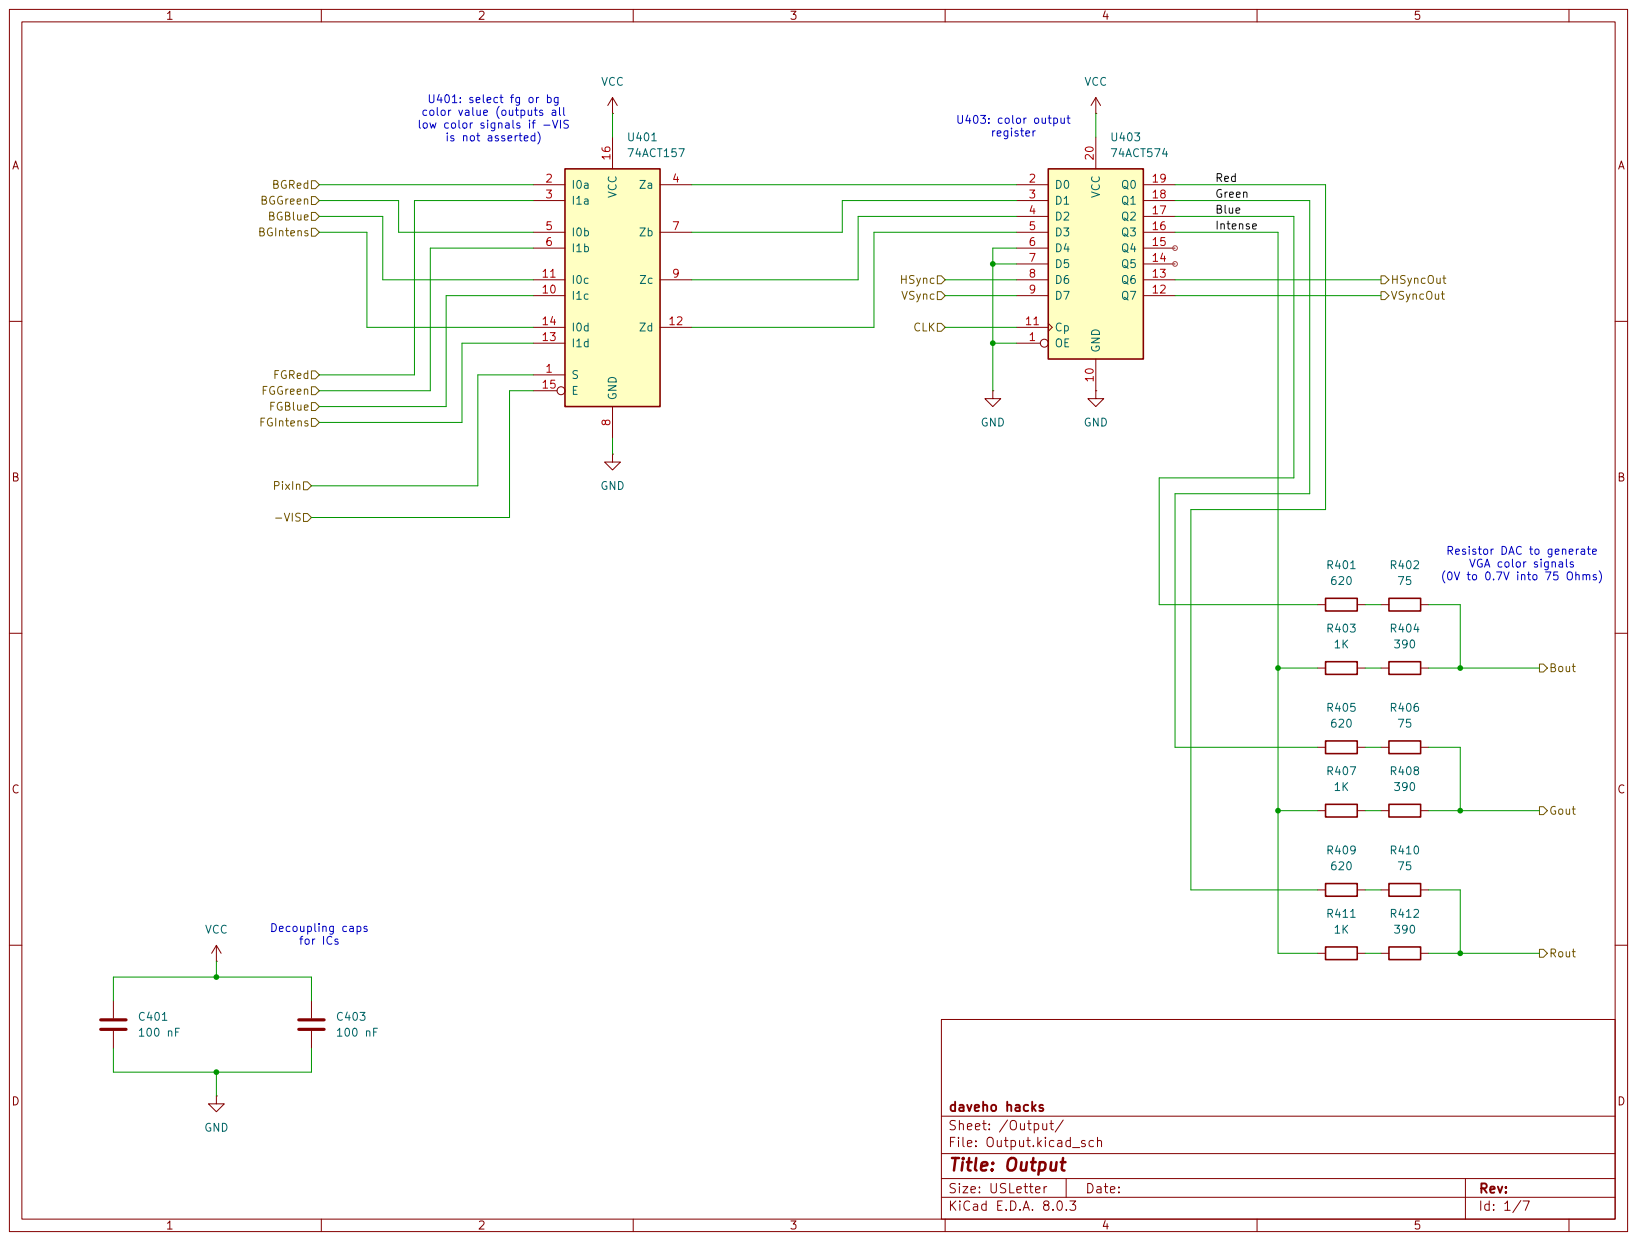
[picture p152: page 4]

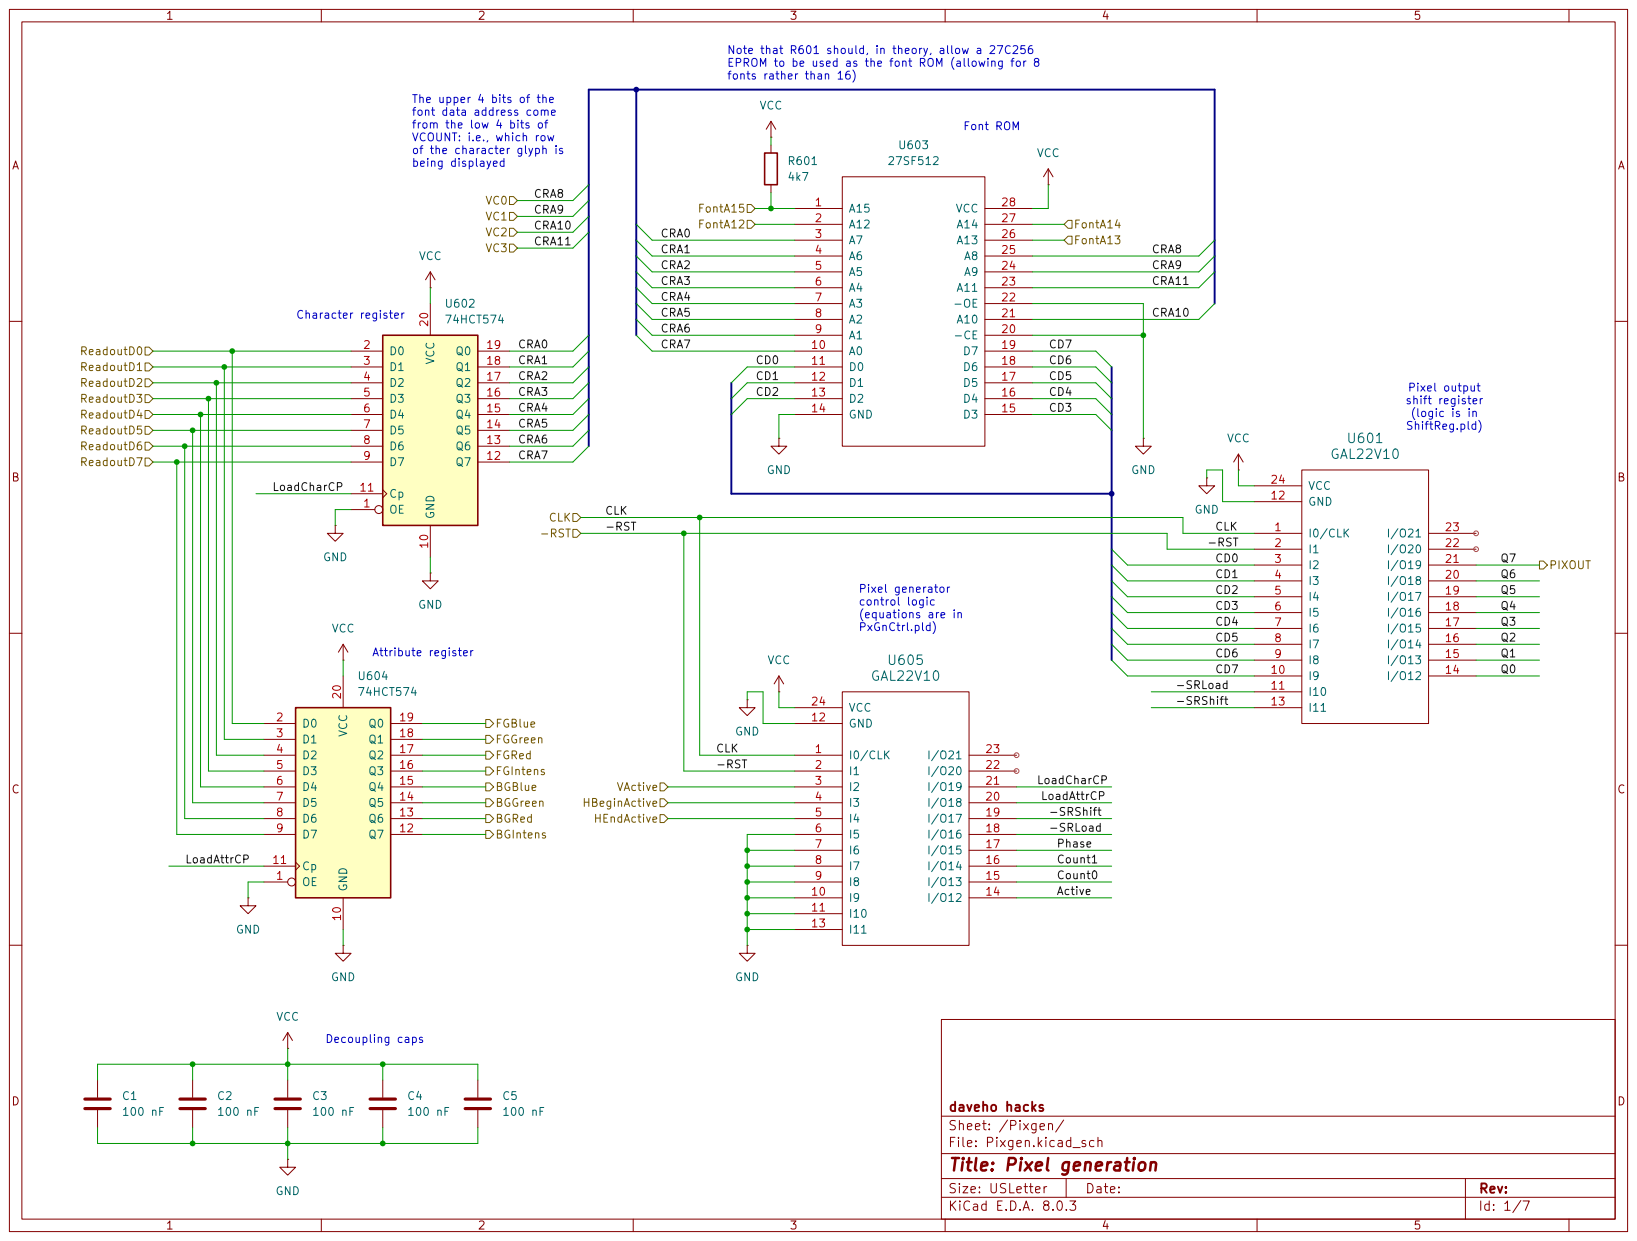
[picture p153: page 5]

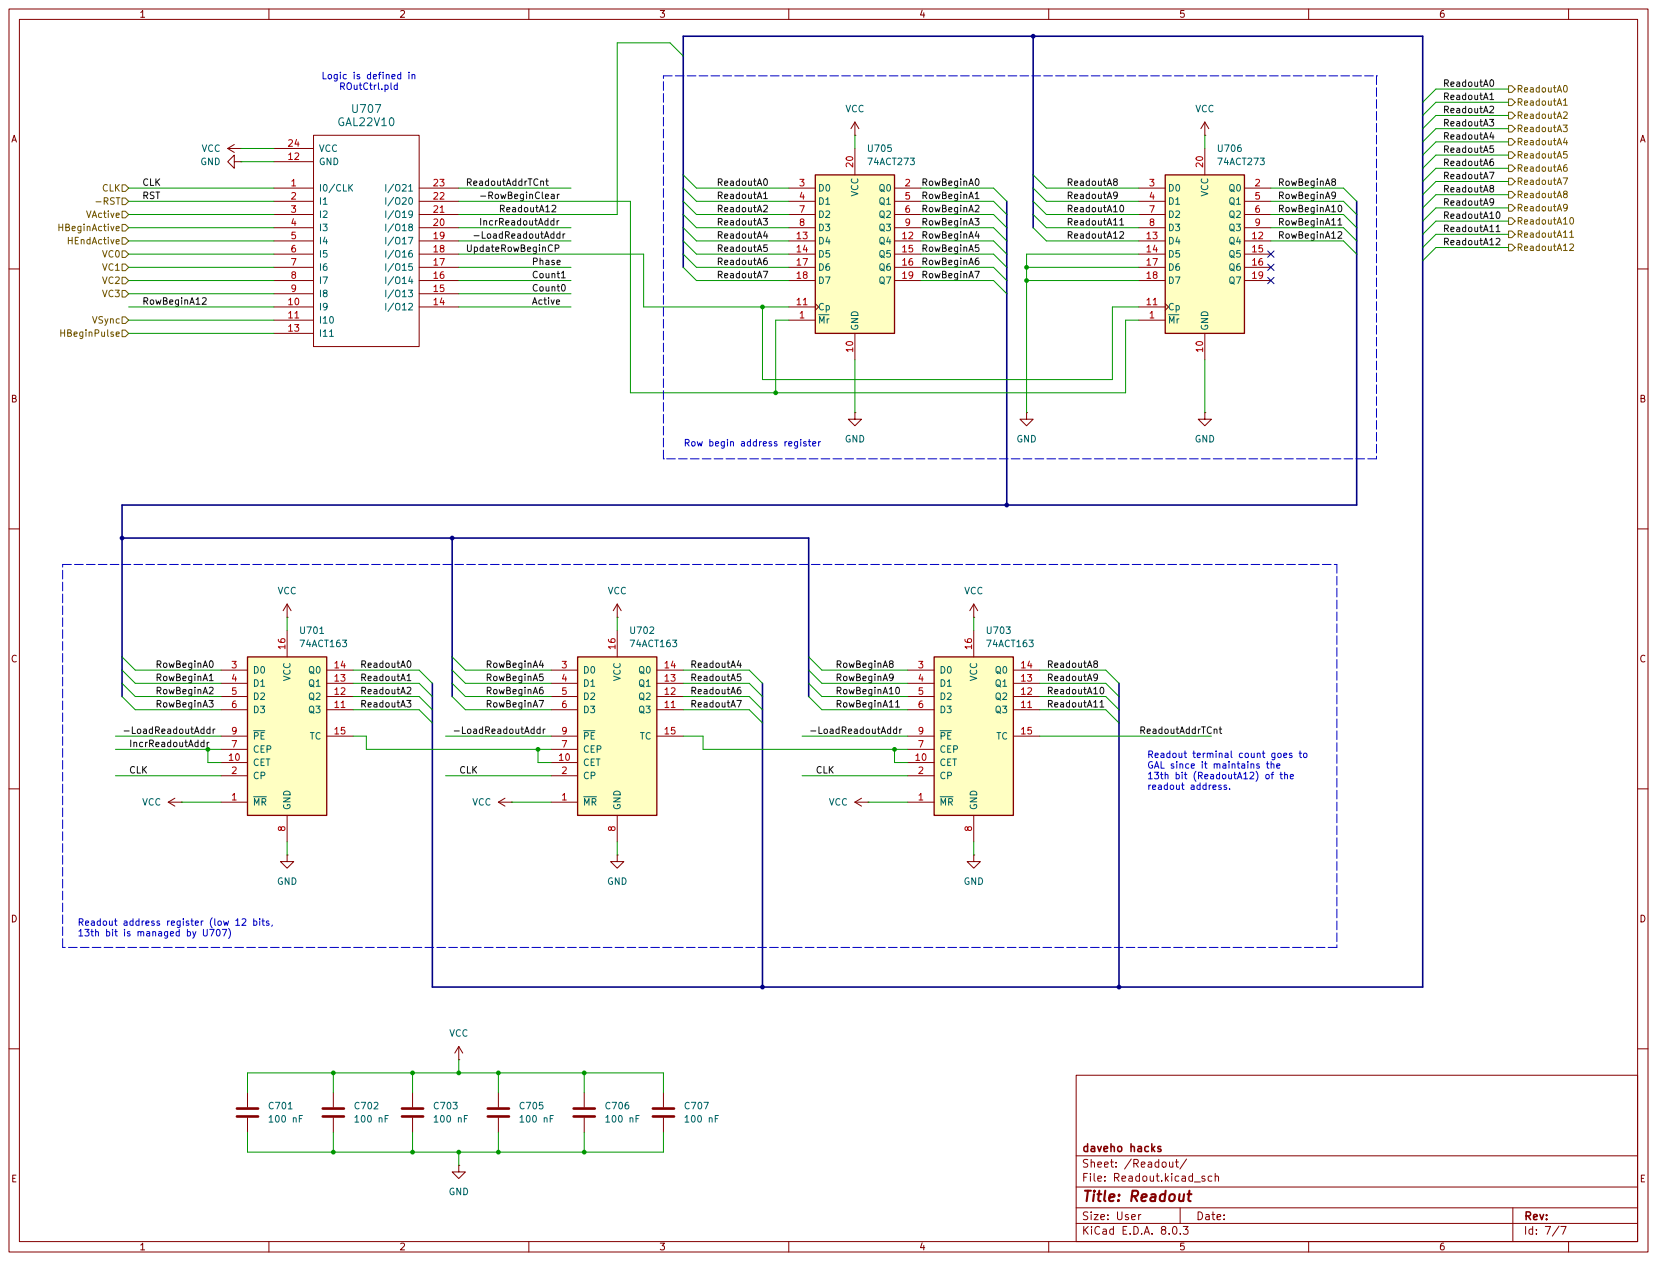
[picture p154: page 6]

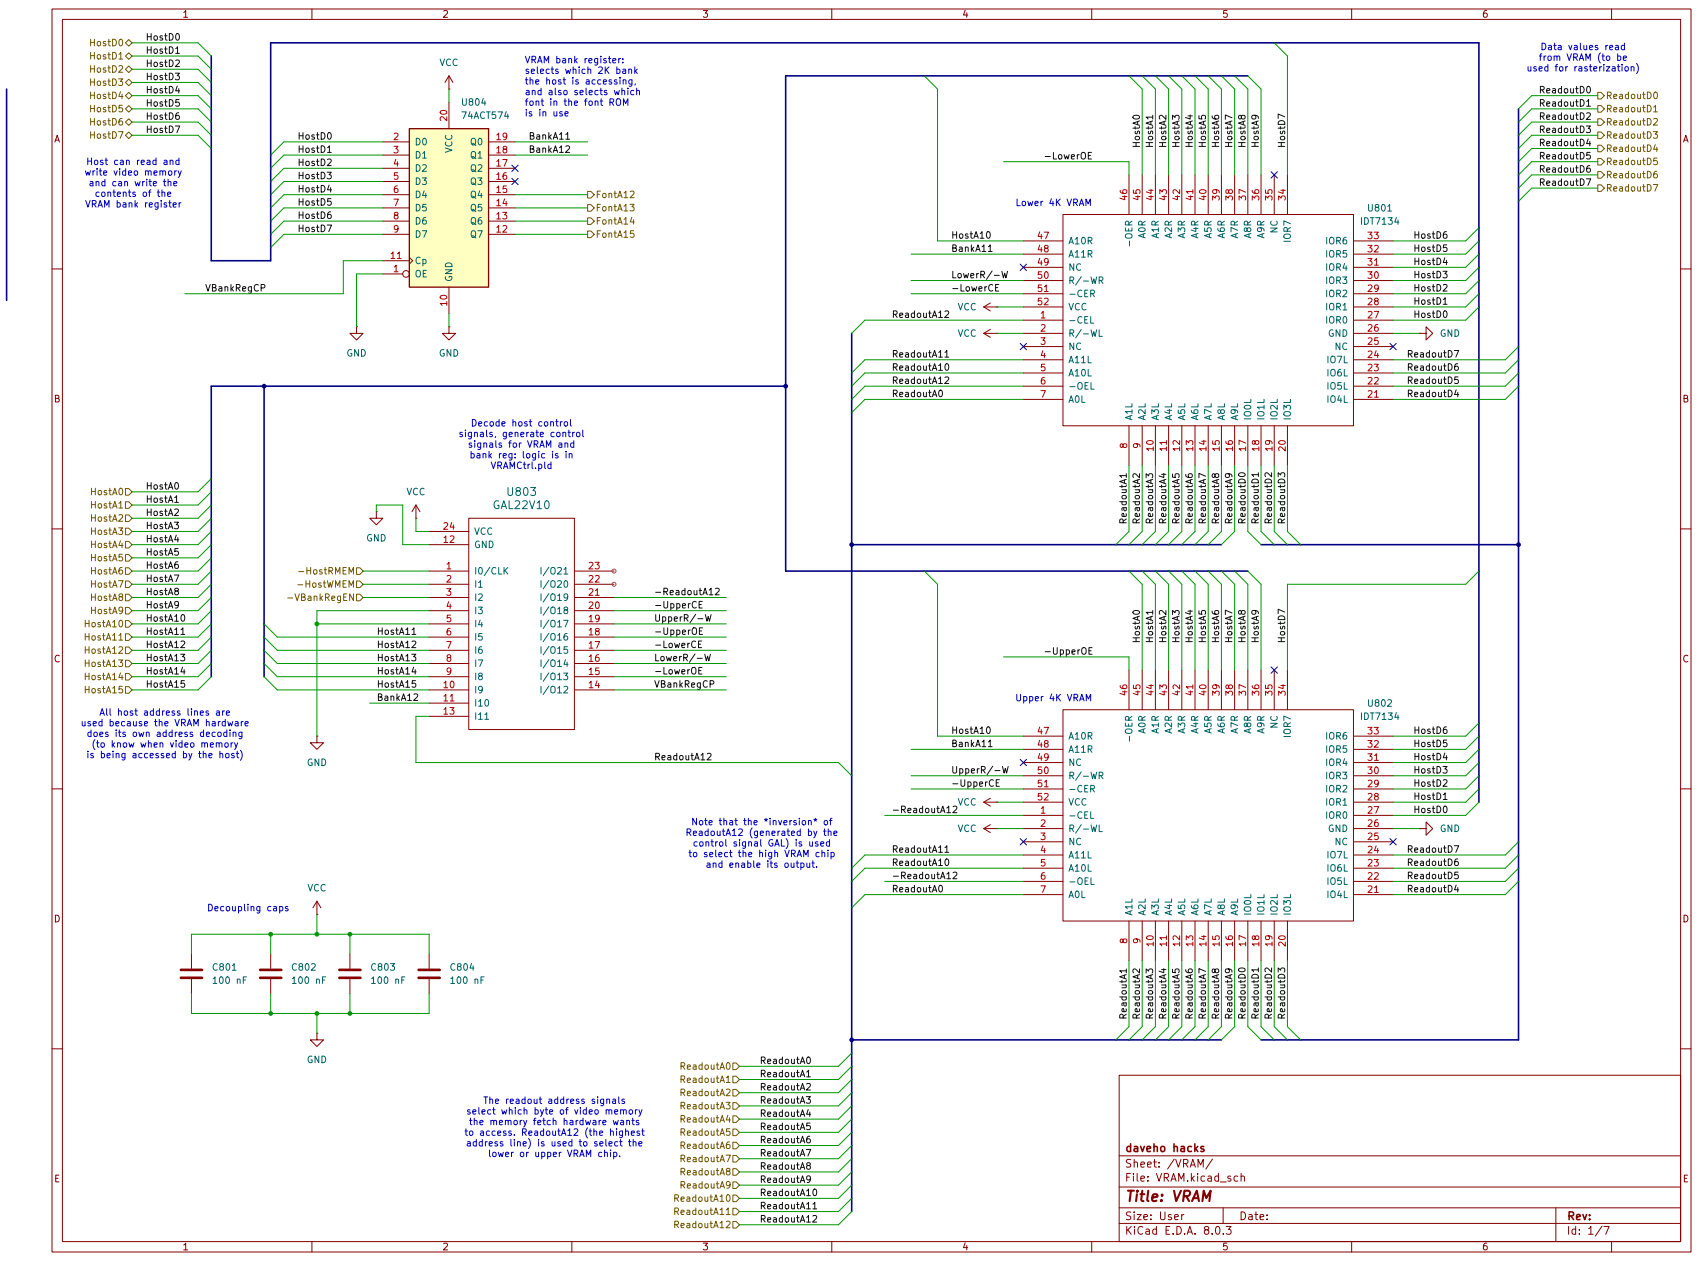
[picture p155: page 7]
