daveho/HW_VGA/Episode03/Materials/schematic_02.pdf

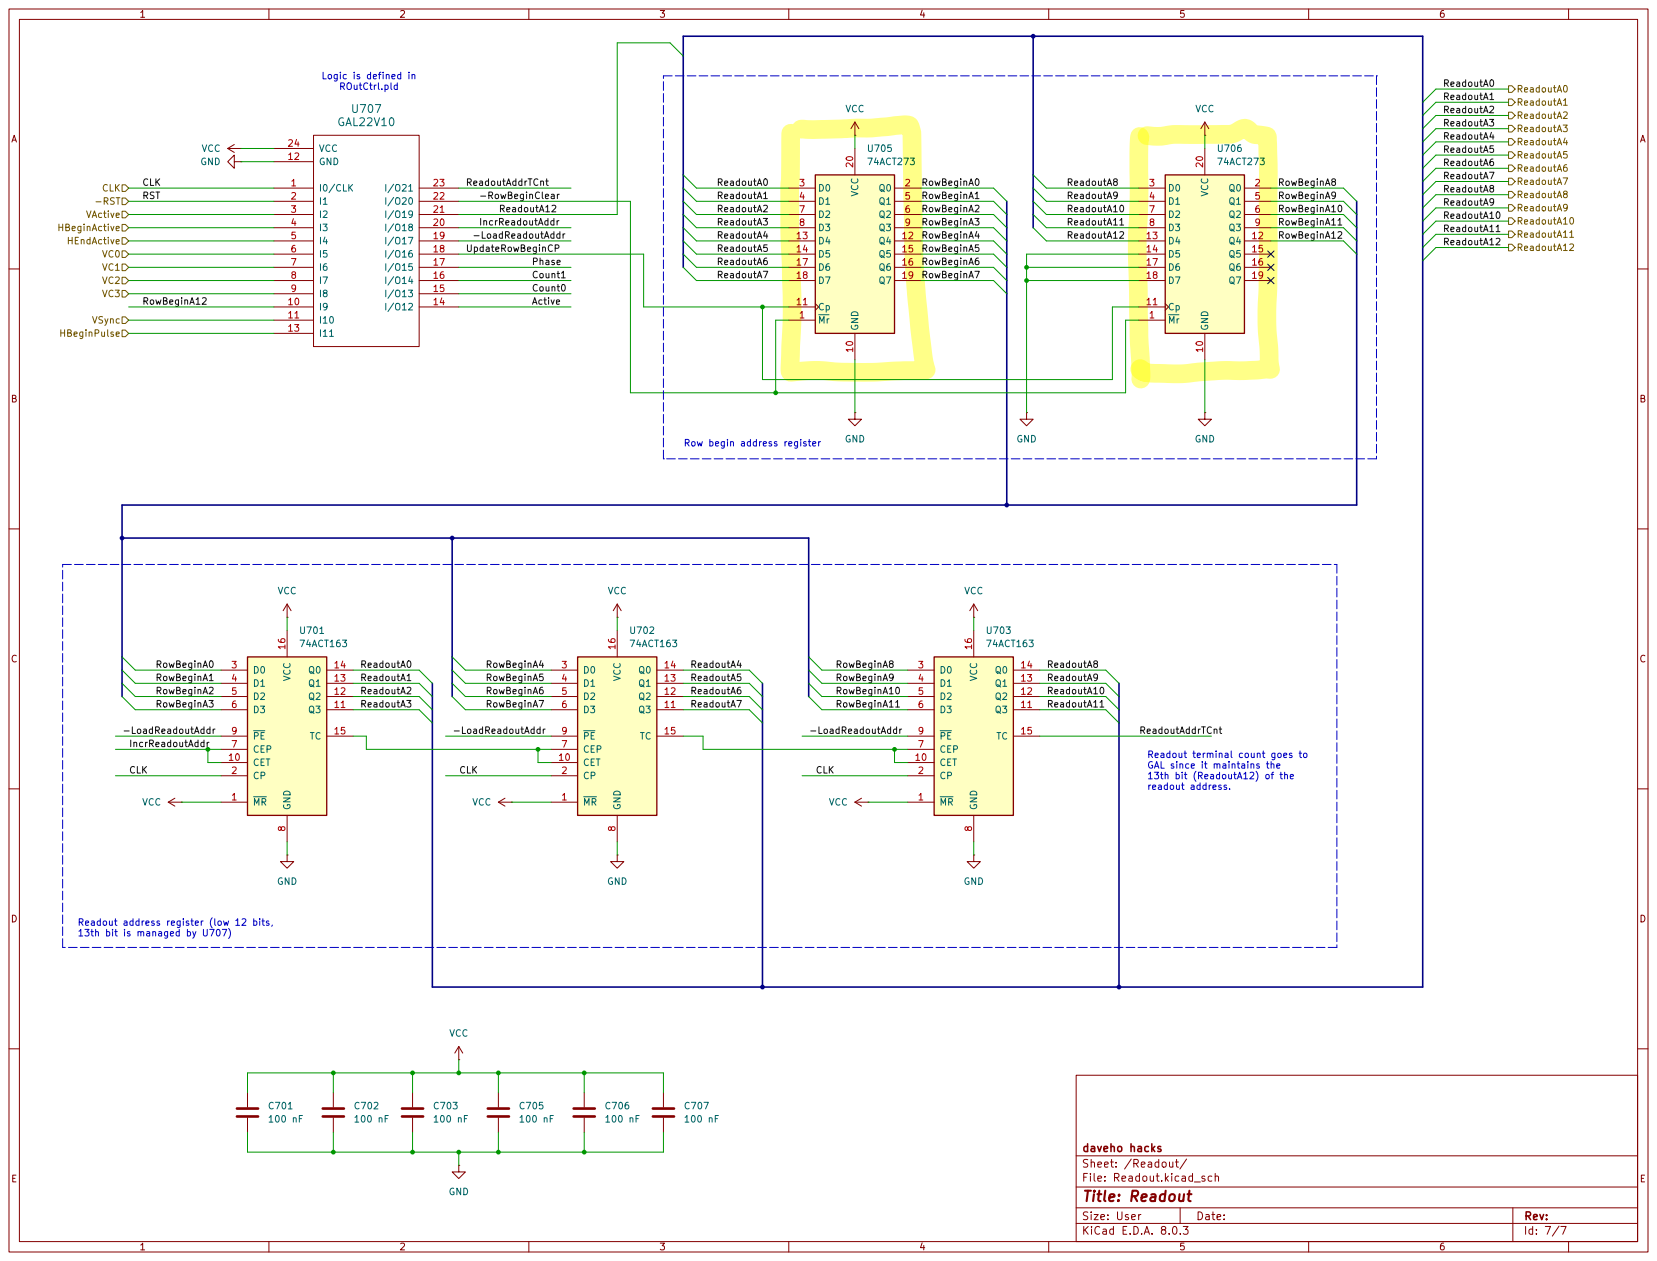
[picture p156: page 6]
