daveho/HW_VGA/Episode03/Materials/schematic_03.pdf

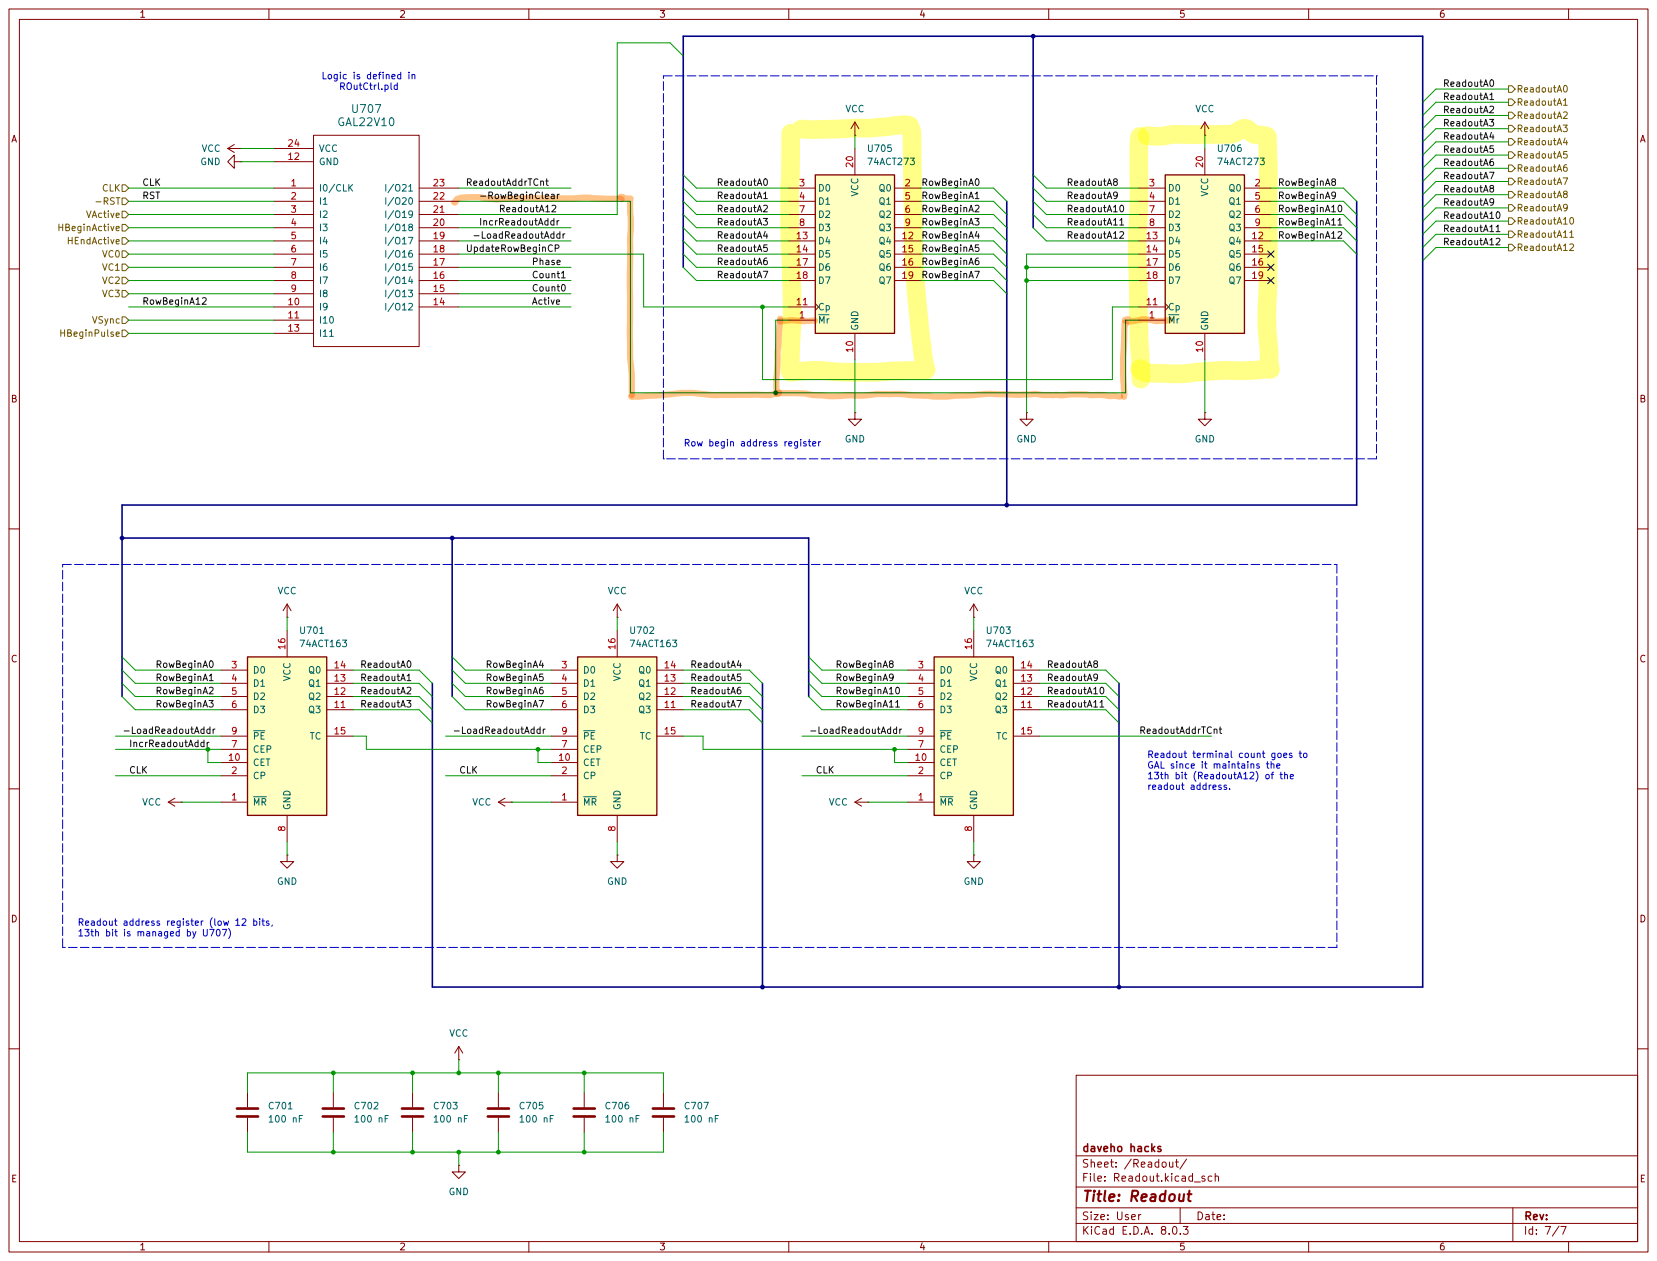
[picture p157: page 6]
