daveho/HW_VGA/Episode03/Materials/schematic_04.pdf

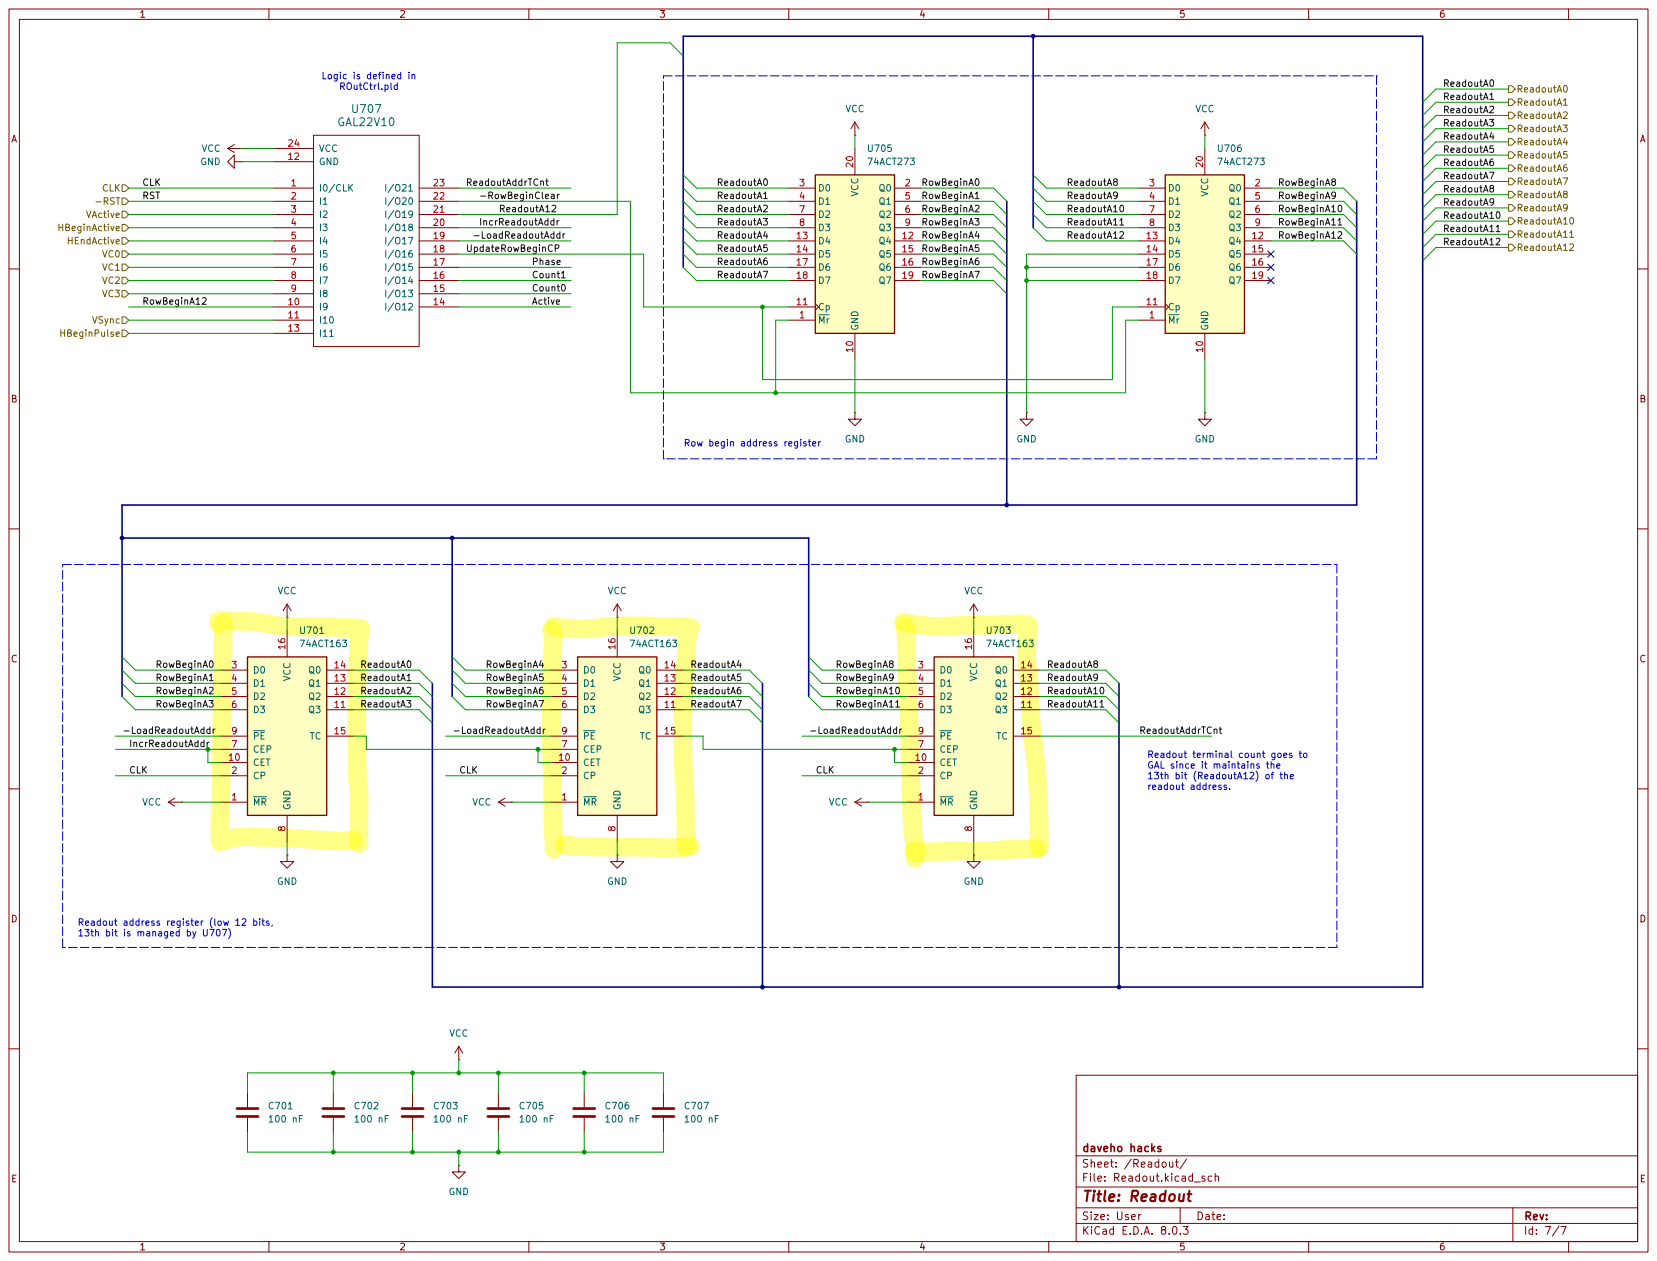
[picture p158: page 6]
