daveho/HW_VGA/Episode03/Materials/schematic_05.pdf

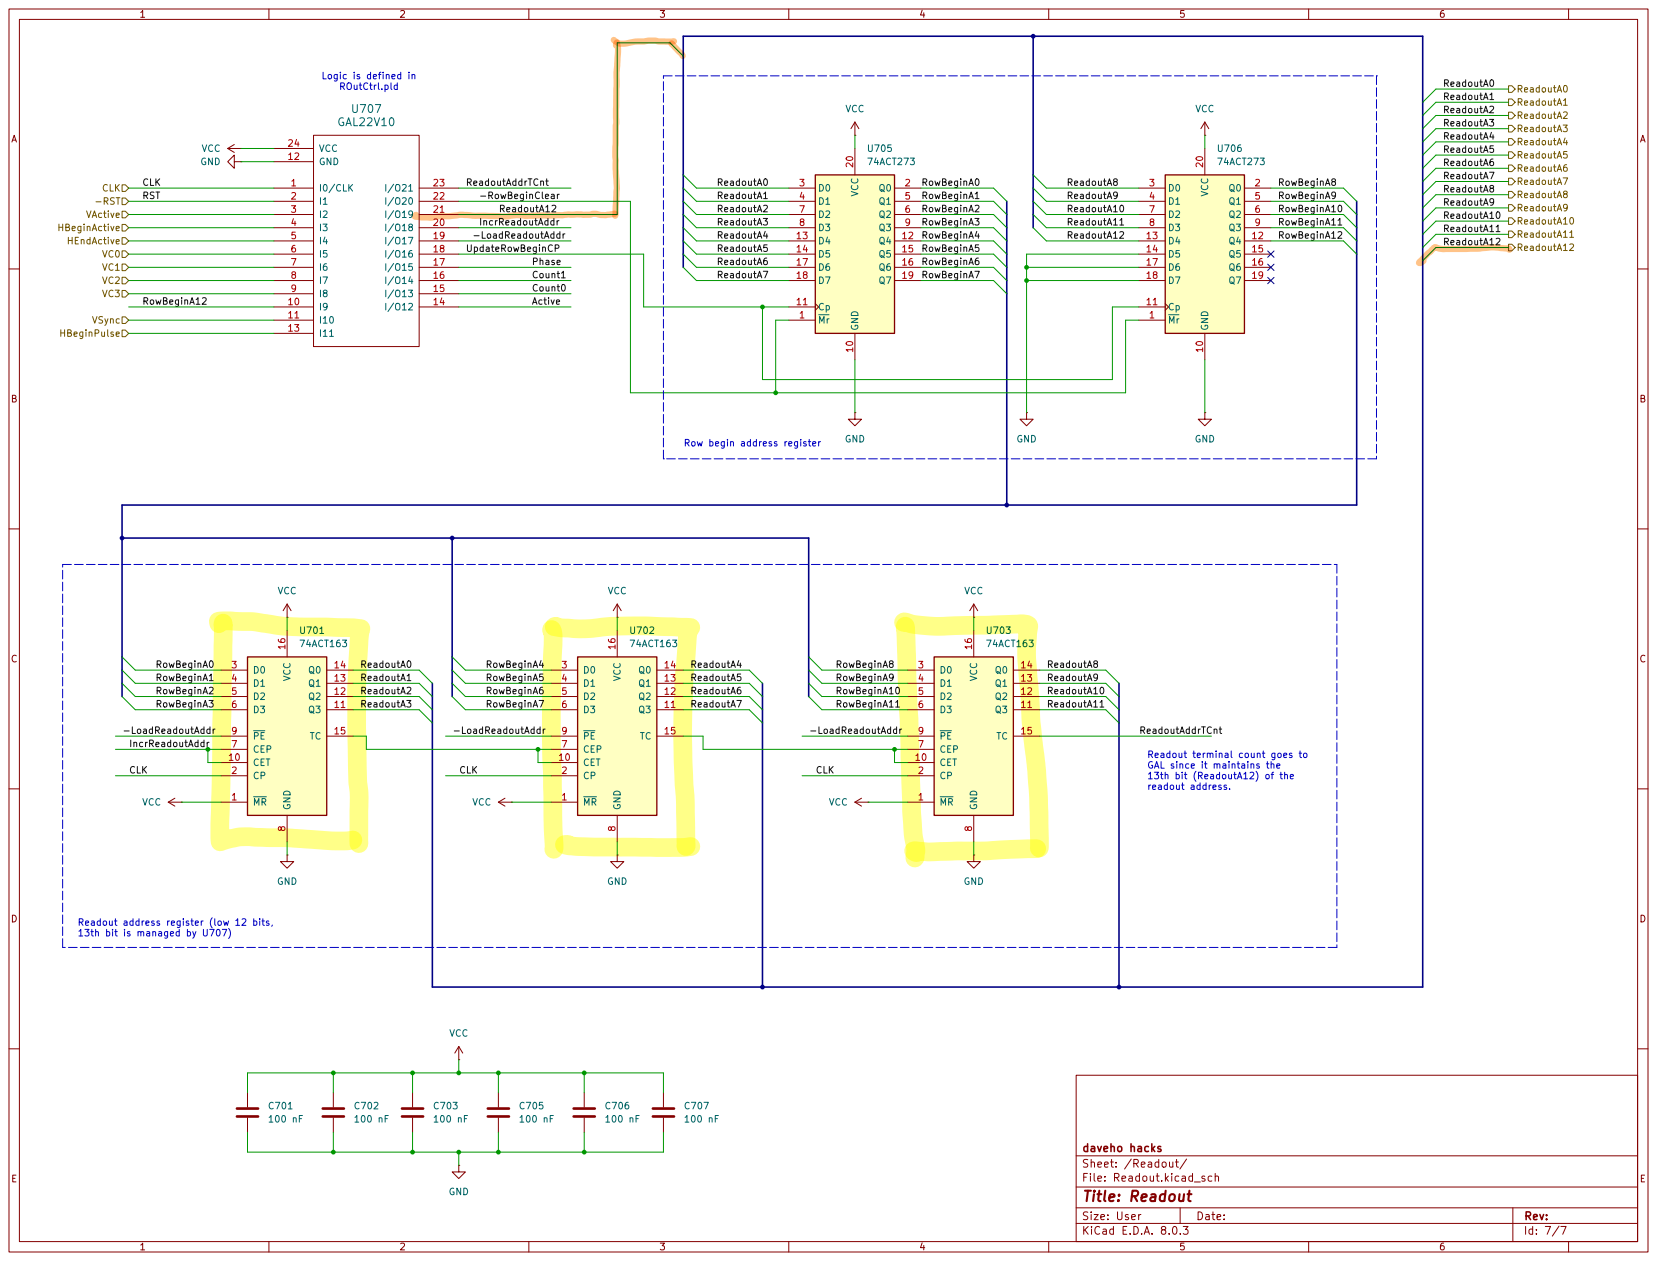
[picture p159: page 6]
