daveho/HW_VGA/Episode03/Materials/schematic_06.pdf

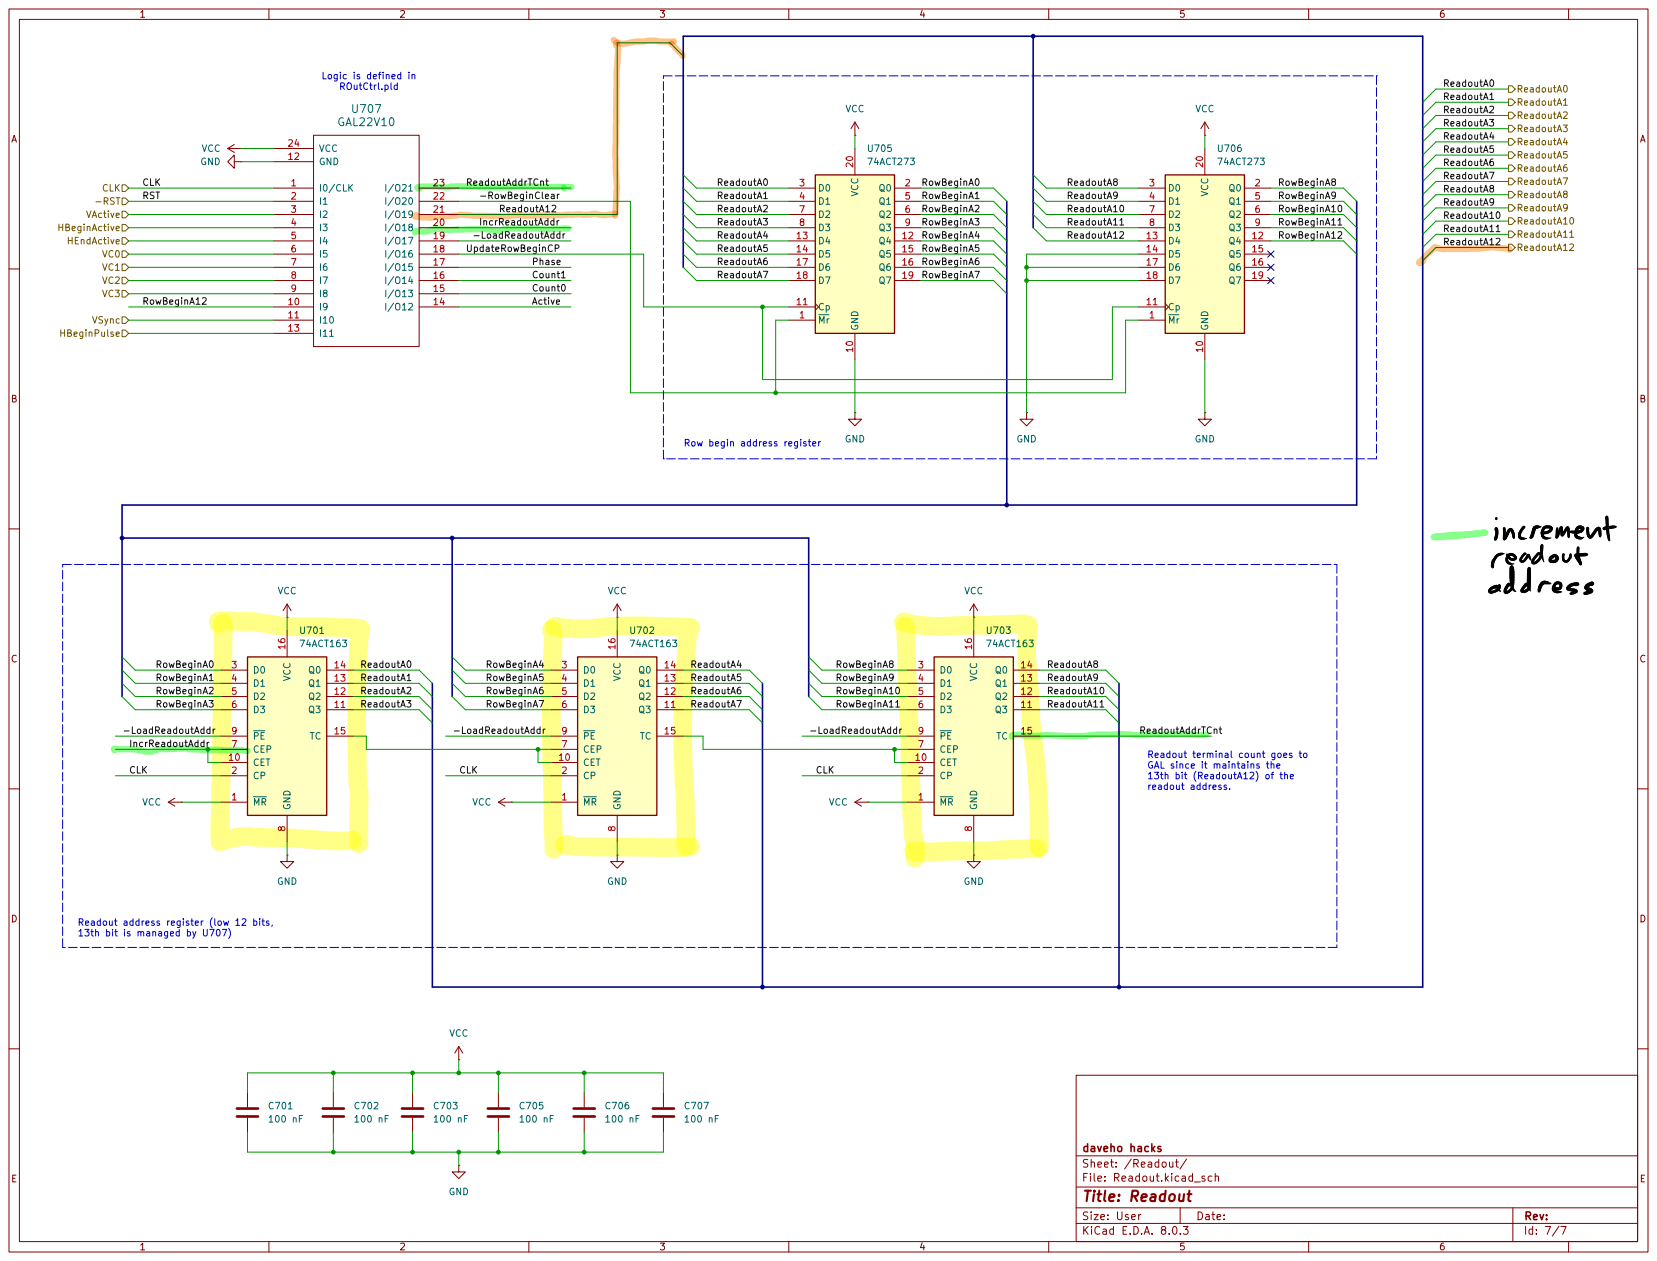
[picture p160: page 6]
