daveho/HW_VGA/Episode03/Materials/schematic_07.pdf

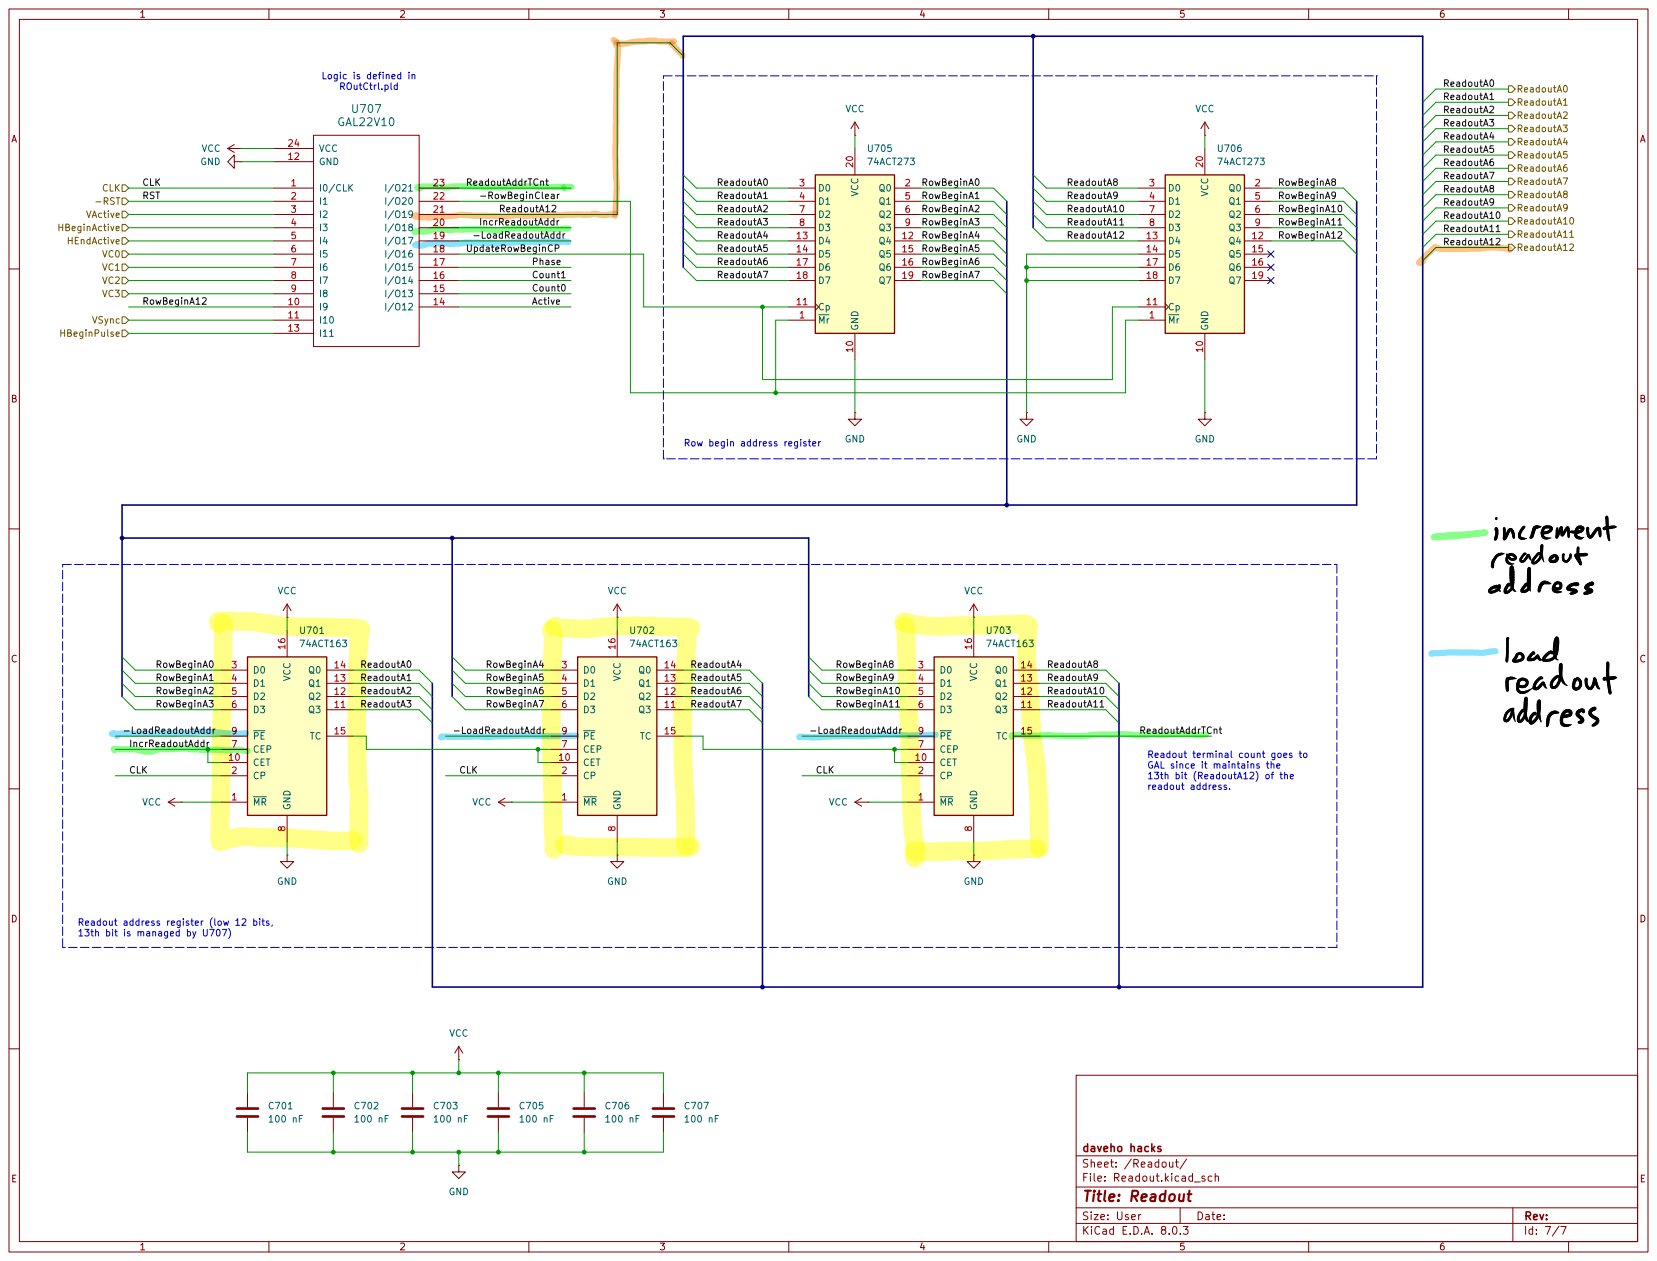
[picture p161: page 6]
