daveho/HW_VGA/Episode03/Materials/readout-overview-018.pdf

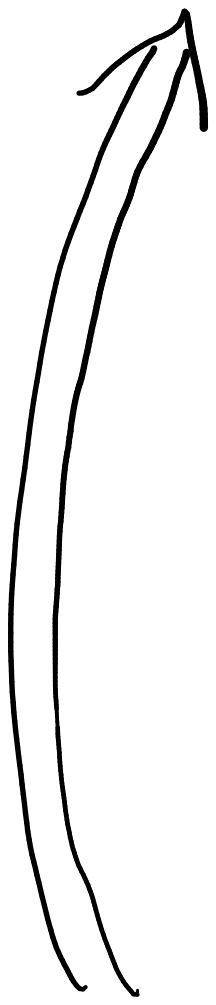
[picture p162: page 1]

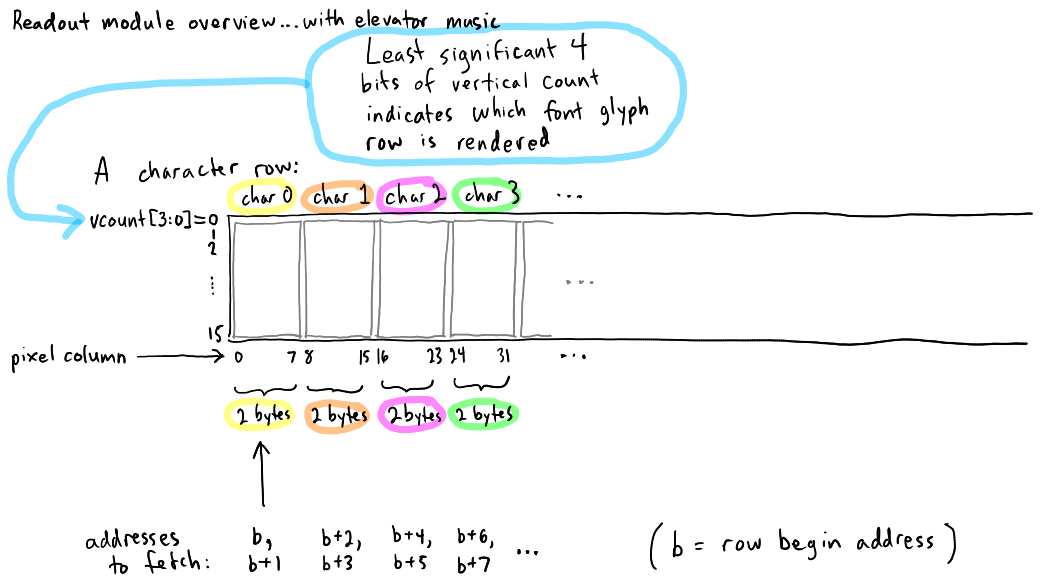
[picture p163: page 2]
