daveho/HW_VGA/HardwareDesign/VRAM.kicad_sch

## KiCad design HardwareDesign/VRAM.kicad_sch (2024-07-31)

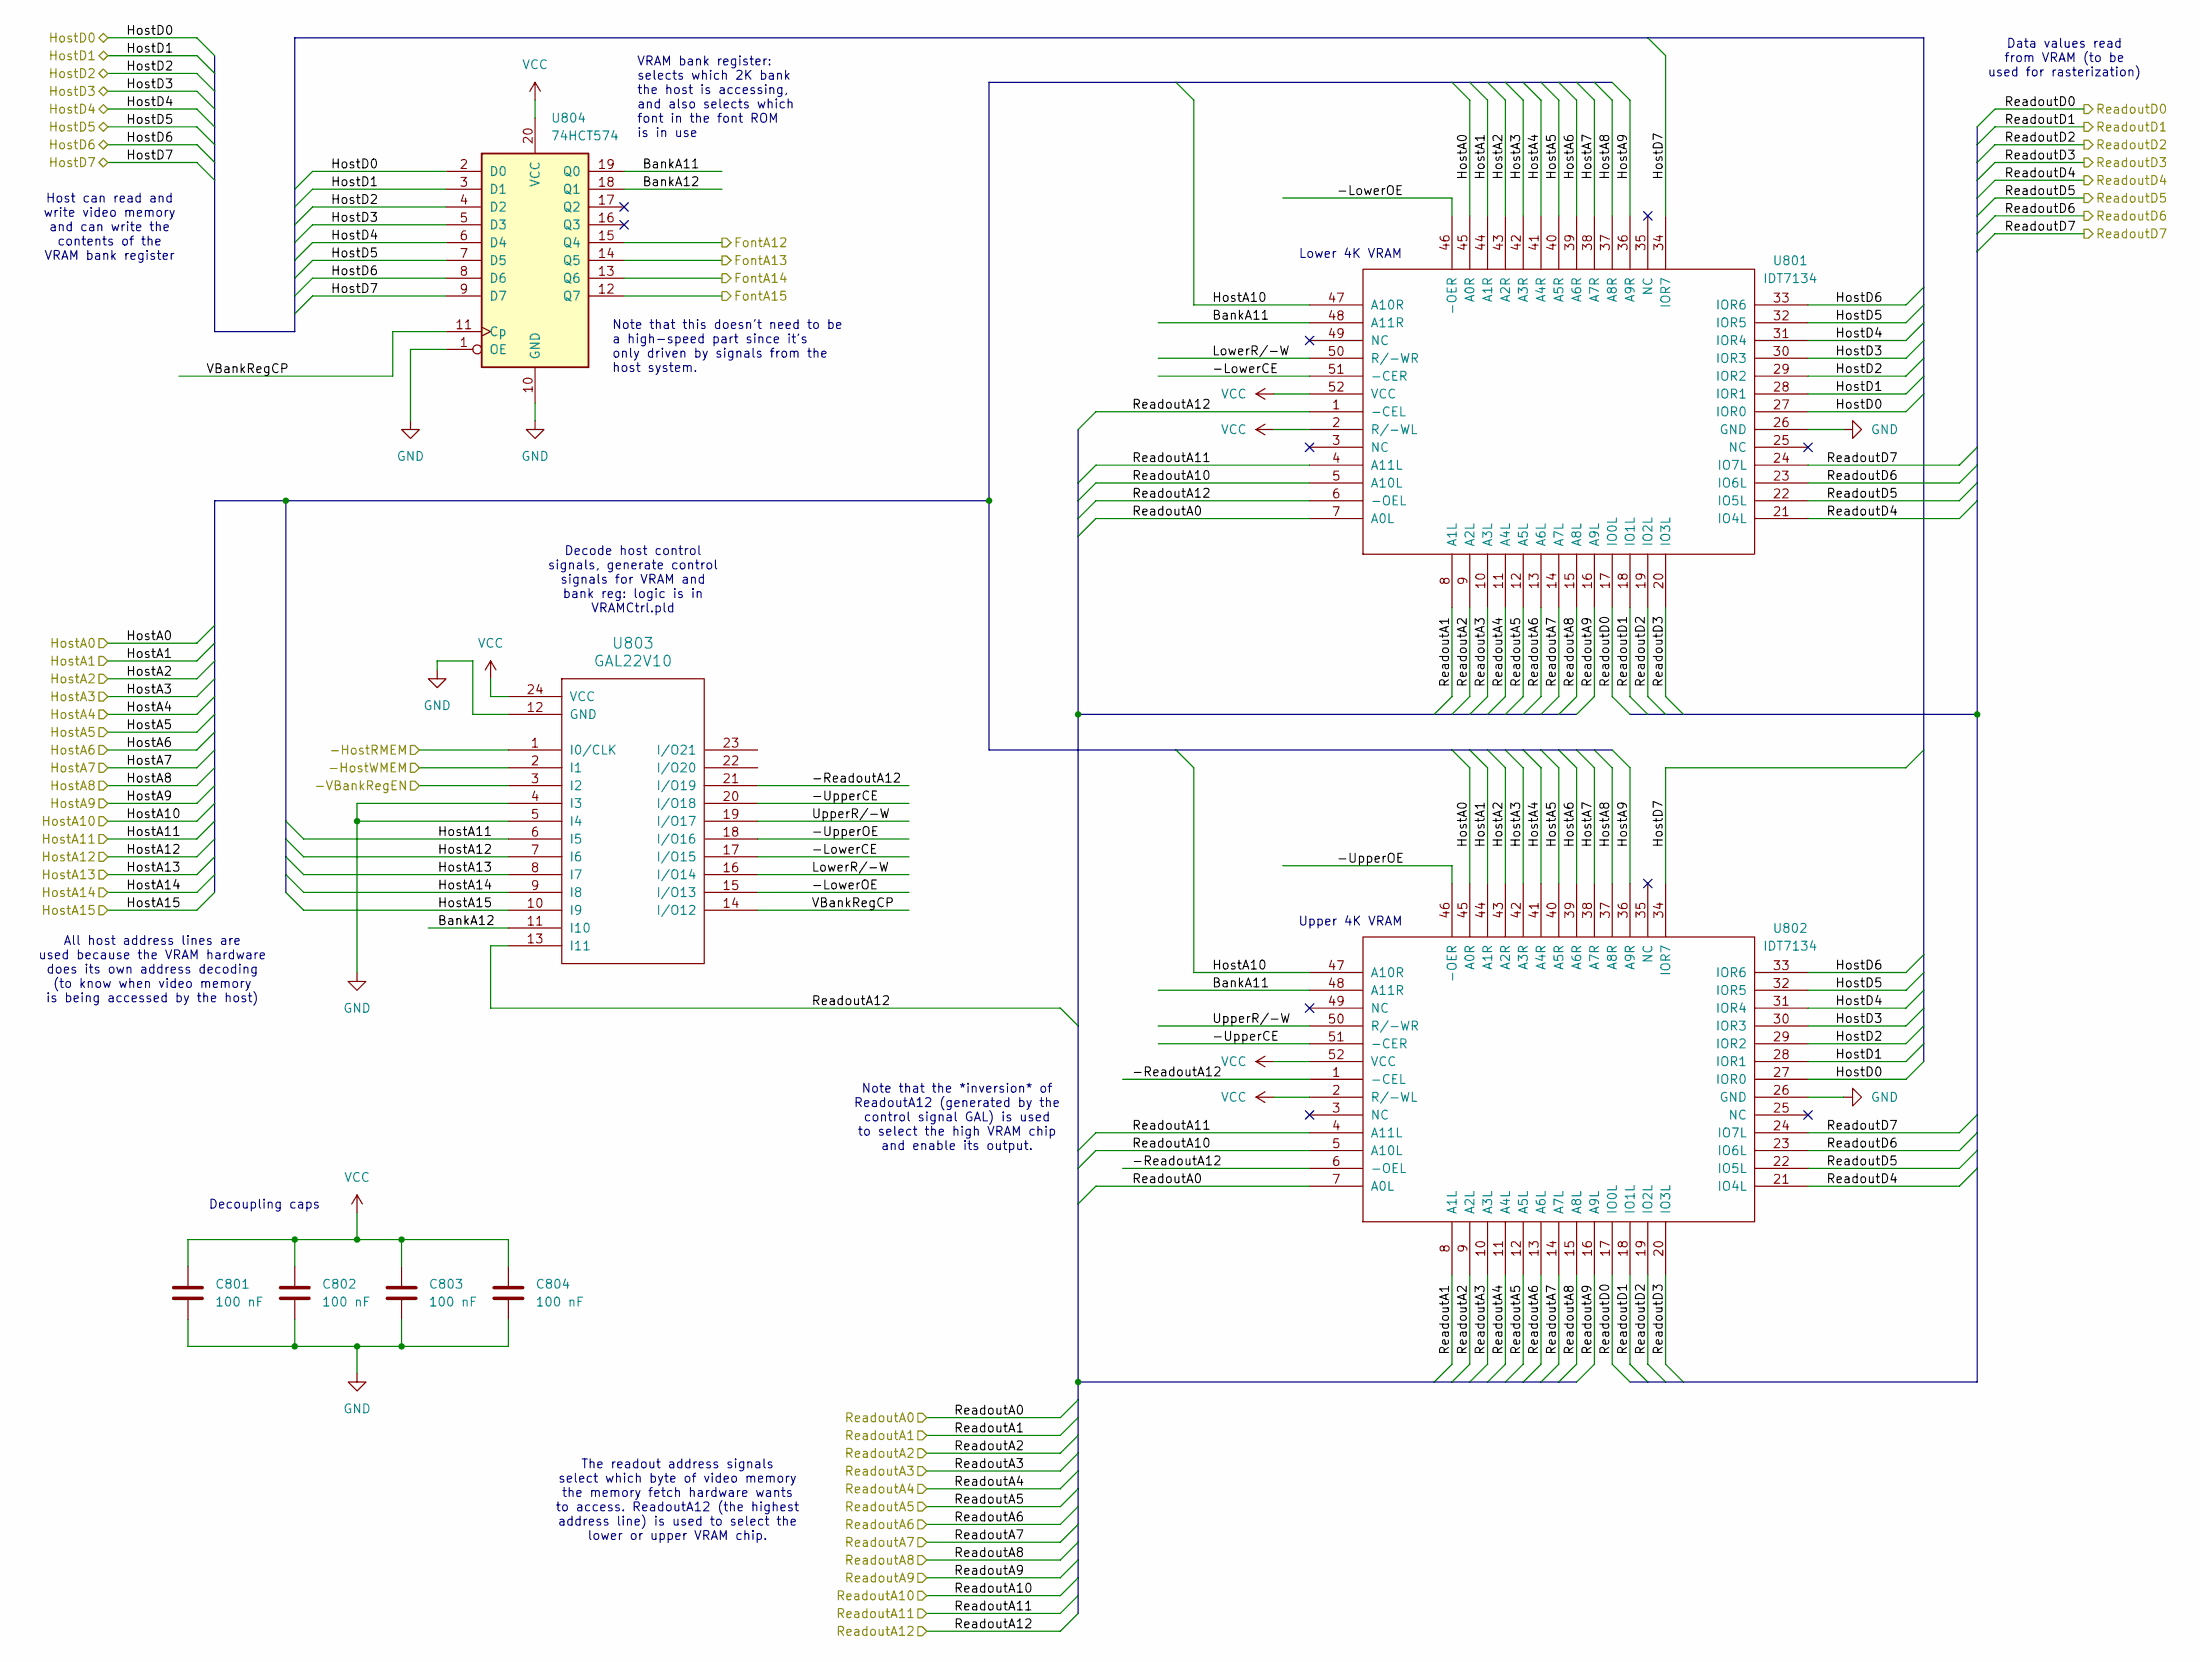
[picture p165: schematic VRAM.kicad_sch]

Parts:
C801, C802, C803, C804: 100 nF
U801, U802: IDT7134; MODULE
U803: GAL22V10
U804: 74HCT574

Connections:
-HostRMEM: U803.1 (I0/CLK)
-HostWMEM: U803.2 (I1)
-LowerCE: U801.51 (-CER), U803.17 (I/O15)
-LowerOE: U801.46 (-OER), U803.15 (I/O13)
-ReadoutA12: U802.1 (-CEL), U802.6 (-OEL), U803.21 (I/O19)
-UpperCE: U802.51 (-CER), U803.20 (I/O18)
-UpperOE: U802.46 (-OER), U803.18 (I/O16)
-VBankRegEN: U803.3 (I2)
BankA11: U801.48 (A11R), U802.48 (A11R), U804.19 (Q0)
BankA12: U803.11 (I10), U804.18 (Q1)
FontA12: U804.15 (Q4)
FontA13: U804.14 (Q5)
FontA14: U804.13 (Q6)
FontA15: U804.12 (Q7)
GND: C801.2, C802.2, C803.2, C804.2, U801.26 (GND), U802.26 (GND), U803.4 (I3), U803.5 (I4), U803.12 (GND), U804.1 (OE), U804.10 (GND)
HostA0: U801.45 (A0R), U802.45 (A0R)
HostA1: U801.44 (A1R), U802.44 (A1R)
HostA2: U801.43 (A2R), U802.43 (A2R)
HostA3: U801.42 (A3R), U802.42 (A3R)
HostA4: U801.41 (A4R), U802.41 (A4R)
HostA5: U801.40 (A5R), U802.40 (A5R)
HostA6: U801.39 (A6R), U802.39 (A6R)
HostA7: U801.38 (A7R), U802.38 (A7R)
HostA8: U801.37 (A8R), U802.37 (A8R)
HostA9: U801.36 (A9R), U802.36 (A9R)
HostA10: U801.47 (A10R), U802.47 (A10R)
HostA11: U803.6 (I5)
HostA12: U803.7 (I6)
HostA13: U803.8 (I7)
HostA14: U803.9 (I8)
HostA15: U803.10 (I9)
HostD0: U801.27 (IOR0), U802.27 (IOR0), U804.2 (D0)
HostD1: U801.28 (IOR1), U802.28 (IOR1), U804.3 (D1)
HostD2: U801.29 (IOR2), U802.29 (IOR2), U804.4 (D2)
HostD3: U801.30 (IOR3), U802.30 (IOR3), U804.5 (D3)
HostD4: U801.31 (IOR4), U802.31 (IOR4), U804.6 (D4)
HostD5: U801.32 (IOR5), U802.32 (IOR5), U804.7 (D5)
HostD6: U801.33 (IOR6), U802.33 (IOR6), U804.8 (D6)
HostD7: U801.34 (IOR7), U802.34 (IOR7), U804.9 (D7)
LowerR/-W: U801.50 (R/-WR), U803.16 (I/O14)
ReadoutA0: U801.7 (A0L), U802.7 (A0L)
ReadoutA1: U801.8 (A1L), U802.8 (A1L)
ReadoutA2: U801.9 (A2L), U802.9 (A2L)
ReadoutA3: U801.10 (A3L), U802.10 (A3L)
ReadoutA4: U801.11 (A4L), U802.11 (A4L)
ReadoutA5: U801.12 (A5L), U802.12 (A5L)
ReadoutA6: U801.13 (A6L), U802.13 (A6L)
ReadoutA7: U801.14 (A7L), U802.14 (A7L)
ReadoutA8: U801.15 (A8L), U802.15 (A8L)
ReadoutA9: U801.16 (A9L), U802.16 (A9L)
ReadoutA10: U801.5 (A10L), U802.5 (A10L)
ReadoutA11: U801.4 (A11L), U802.4 (A11L)
ReadoutA12: U801.1 (-CEL), U801.6 (-OEL), U803.13 (I11)
ReadoutD0: U801.17 (IO0L), U802.17 (IO0L)
ReadoutD1: U801.18 (IO1L), U802.18 (IO1L)
ReadoutD2: U801.19 (IO2L), U802.19 (IO2L)
ReadoutD3: U801.20 (IO3L), U802.20 (IO3L)
ReadoutD4: U801.21 (IO4L), U802.21 (IO4L)
ReadoutD5: U801.22 (IO5L), U802.22 (IO5L)
ReadoutD6: U801.23 (IO6L), U802.23 (IO6L)
ReadoutD7: U801.24 (IO7L), U802.24 (IO7L)
UpperR/-W: U802.50 (R/-WR), U803.19 (I/O17)
VBankRegCP: U803.14 (I/O12), U804.11 (Cp)
VCC: C801.1, C802.1, C803.1, C804.1, U801.2 (R/-WL), U801.52 (VCC), U802.2 (R/-WL), U802.52 (VCC), U803.24 (VCC), U804.20 (VCC)

Notes on the sheet:
Decode host control signals, generate control signals for VRAM and bank reg: logic is in VRAMCtrl.pld
Note that this doesn't need to be a high-speed part since it's only driven by signals from the host system.
All host address lines are used because the VRAM hardware does its own address decoding (to know when video memory is being accessed by the host)
Decoupling caps
Lower 4K VRAM
Host can read and write video memory and can write the contents of the VRAM bank register
The readout address signals select which byte of video memory the memory fetch hardware wants to access. ReadoutA12 (the highest address line) is used to select the lower or upper VRAM chip.
VRAM bank register: selects which 2K bank the host is accessing, and also selects which font in the font ROM is in use
Upper 4K VRAM
Data values read from VRAM (to be used for rasterization)
Note that the *inversion* of ReadoutA12 (generated by the control signal GAL) is used to select the high VRAM chip and enable its output.
