daveho/HW_VGA/Episode01/HardwareDesign/ReadAddr.kicad_sch

## KiCad design Episode01/HardwareDesign/ReadAddr.kicad_sch (2024-05-03)

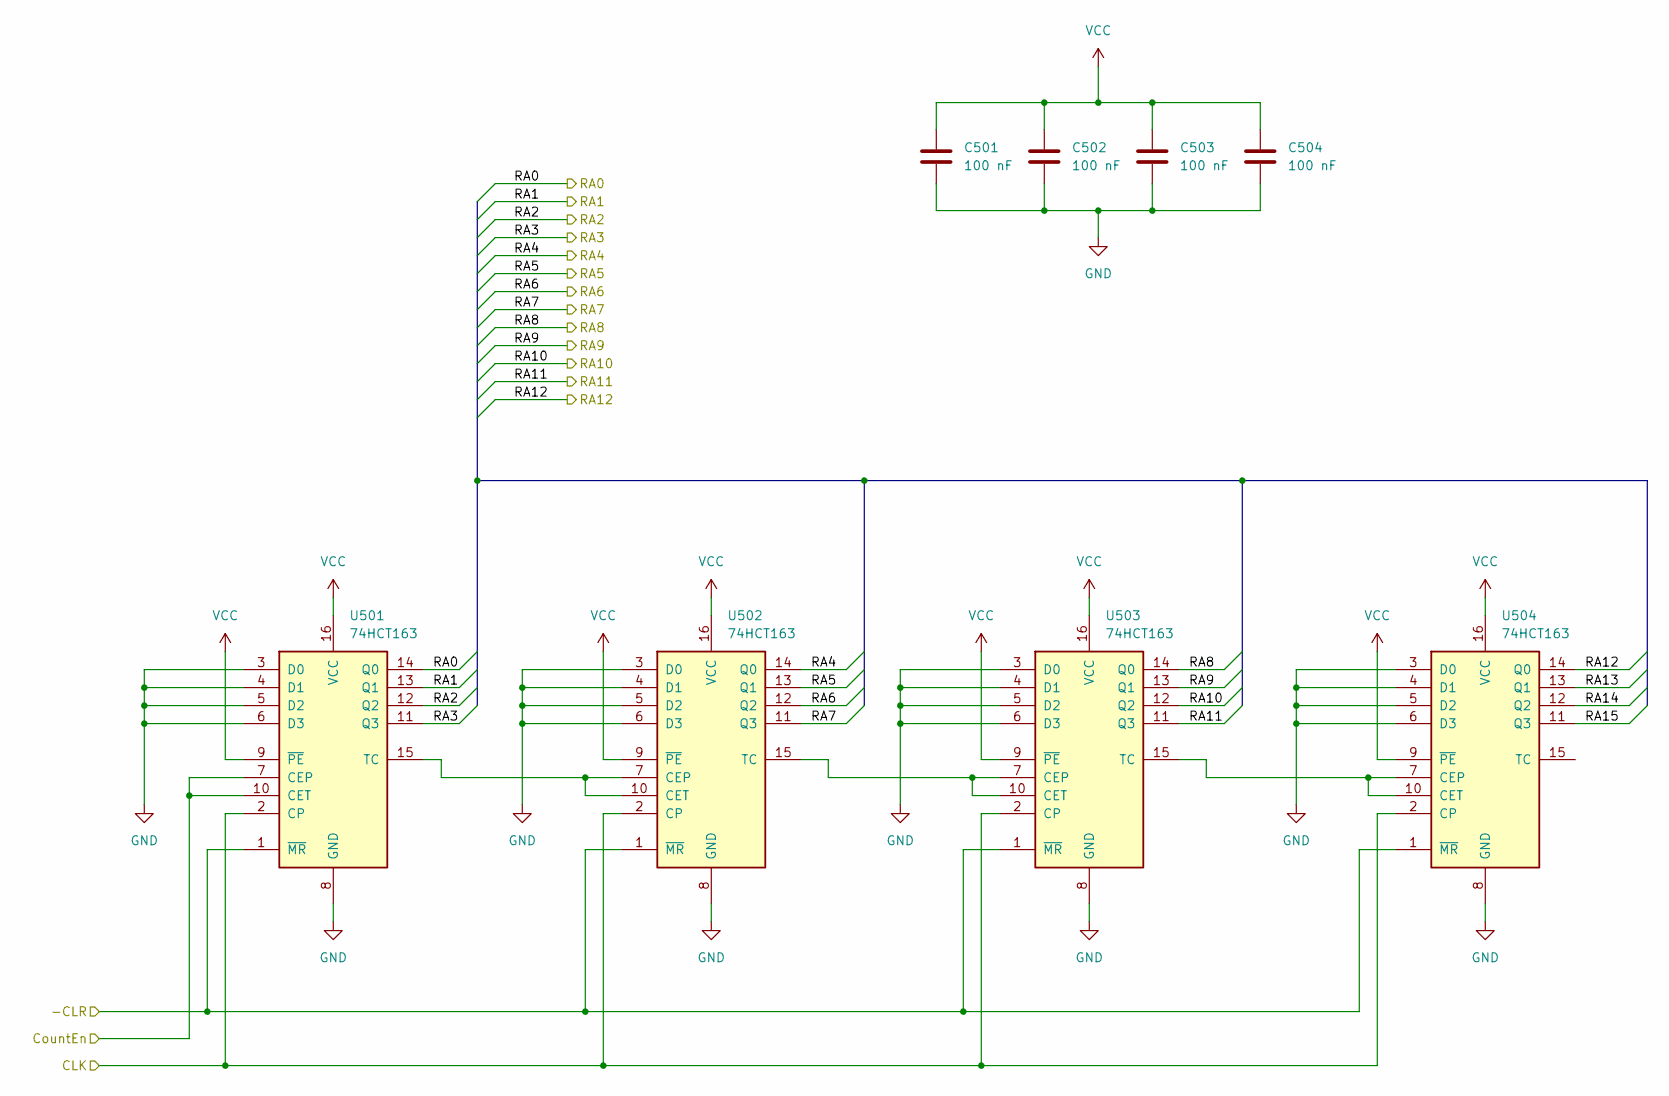
[picture p166: schematic ReadAddr.kicad_sch]

Parts:
C501, C502, C503, C504: 100 nF
U501, U502, U503, U504: 74HCT163

Connections:
-CLR: U501.1 (~MR), U502.1 (~MR), U503.1 (~MR), U504.1 (~MR)
CLK: U501.2 (CP), U502.2 (CP), U503.2 (CP), U504.2 (CP)
CountEn: U501.7 (CEP), U501.10 (CET)
GND: C501.2, C502.2, C503.2, C504.2, U501.3 (D0), U501.4 (D1), U501.5 (D2), U501.6 (D3), U501.8 (GND), U502.3 (D0), U502.4 (D1), U502.5 (D2), U502.6 (D3), U502.8 (GND), U503.3 (D0), U503.4 (D1), U503.5 (D2), U503.6 (D3), U503.8 (GND), U504.3 (D0), U504.4 (D1), U504.5 (D2), U504.6 (D3), U504.8 (GND)
unnamed: U501.15 (TC), U502.7 (CEP), U502.10 (CET)
unnamed: U502.15 (TC), U503.7 (CEP), U503.10 (CET)
unnamed: U503.15 (TC), U504.7 (CEP), U504.10 (CET)
RA0: U501.14 (Q0)
RA1: U501.13 (Q1)
RA2: U501.12 (Q2)
RA3: U501.11 (Q3)
RA4: U502.14 (Q0)
RA5: U502.13 (Q1)
RA6: U502.12 (Q2)
RA7: U502.11 (Q3)
RA8: U503.14 (Q0)
RA9: U503.13 (Q1)
RA10: U503.12 (Q2)
RA11: U503.11 (Q3)
RA12: U504.14 (Q0)
RA13: U504.13 (Q1)
RA14: U504.12 (Q2)
RA15: U504.11 (Q3)
VCC: C501.1, C502.1, C503.1, C504.1, U501.9 (~PE), U501.16 (VCC), U502.9 (~PE), U502.16 (VCC), U503.9 (~PE), U503.16 (VCC), U504.9 (~PE), U504.16 (VCC)
